jphein/ember.realm.watch/site/README.md

# Ember — GitHub Pages site

Mirrors the repo layout morpheus confirmed: **`docs/` is the Pages root.**

```
index.src.html           ← EDIT THIS
build.py                 ← then run this (it also runs build_print_sheet.py)
build_print_sheet.py     enclosure/PRINT-SHEET.md → docs/print-sheet.html
check_generated_current.py   pre-commit: source staged without its rebuilt page
check_served_current.py      after a push: what a VISITOR downloads vs origin/main
renders/                 enclosure figures — GENERATED, not hand-drawn:
                           case-*    enclosure/tools/make_renders.py        (desk)
                           mobile-*  enclosure/tools/make_mobile_renders.py (battery)
ember-art-web/og_card.py ← regenerates the social preview card
docs/                    ← the deliverable; stage this whole directory
  index.html          HTML + inline <style> + the inlined hero SVG
  print-sheet.html    generated; .nojekyll would otherwise serve the .md as text
  assets/*.wav        the six chimes, fetched on click
  assets/og-card.png  1200x630 social preview (PLACEHOLDER — see below)
  .nojekyll           serve the tree untouched by Jekyll
```

**The figures under `renders/` carry no hand-drawn geometry, and that is load-bearing.** The
button outline was once typed twice — once as a solid in `ember_case.py`, once as a polygon in
`make_renders.py` — and the two copies were free to disagree forever with nothing to notice.
They did: both were rectangles, the part was asked to become hexagons, and only the figure is
ever looked at. Every figure now reads the case module. *A second hand-drawn copy of geometry
is not documentation of it, it is a rumour about it.*

**No byte counts here on purpose.** They used to be quoted and they went stale every
build — this file claimed 138 KB for a page that had grown past 250. `build.py` prints
the real sizes, the inline/copied split and every outbound link on each run, so that
output is authoritative and this list is only a map.

## Editing a source is not publishing it, and publishing is not serving

Three separate gaps, and each one has produced a wrong **published** page while the repo looked
correct. The two checks above exist because notes about this did not work:

| gap | symptom seen | caught by |
|---|---|---|
| source edited, page not rebuilt | `docs/print-sheet.html` said **"⛔ DO NOT PRINT"** for hours after the source was cleared | `check_generated_current.py`, pre-commit |
| committed, not pushed | the retraction sat locally while the page still warned | `git status` / the sweep's ahead-behind line |
| pushed, not yet served | the fixed STL download served the **blocked** part for ~1 min | `check_served_current.py`, after a push |

⚠️ **`enclosure/PRINT-SHEET.md` does not look like a build input.** It is a markdown file in the
enclosure directory, and nothing at the point of editing says a page depends on it — which is
why the guard is mechanical rather than a request to remember. If you add another
source → page pair, add it to `PAIRS` in `check_generated_current.py` in the same change, and
run `--self-test`.

**`renders/` is now in `PAIRS` too, and it should have been from the start.** The guard's own
list of what it exists to prevent opens with *"`docs/assets/case-hero.png` was one render behind
after the case geometry changed"* — and the figures were never actually added, so that first
entry was the one case still uncovered. It matters more than "cosmetic" suggests: `build.py`
**inlines** the SVGs into `docs/index.html`, so regenerating a section drawing and staging it
without rebuilding publishes the previous geometry while the repo looks correct. All 13 figures
are listed, and `_compare` runs each builder once regardless of how many are staged, so the
guard did not get 13× slower. `--self-test` reports **15 pairs**.

The hook is not tracked by git (`.git/hooks` never is), so **a fresh clone starts unprotected**.
The install line is in [`docs/verification.md`](../docs/verification.md).

## ⚠️ One thing still outstanding

**`assets/og-card.png` is still the placeholder.** The card the site *should* ship —
lyra's, with the web-scale wyrm — is generated by `ember-art-web/og_card.py`, which is
in this repo and verified reproducible. What has not happened is the swap itself:
dropping its `og-card.png` into `docs/assets/` **and** updating `og:image:alt` in
`index.src.html` in the same change, because the alt currently describes the
placeholder. That pairing is the whole point — the page renders perfectly with a stale
alt, so nothing local will flag it. It surfaces only in a screen reader or a social
preview.

`og_card.py` will not let a wrong *engine name* through: it carries a `CLAIMS`
provenance table and a `BLOCKED` list (`whisper`, `openai`, `cloud api`, …) checked
against the artwork text and the alt text, and it exits non-zero on a hit. It cannot
check whether the alt still describes the right *picture*. That part is the human's.

*(Resolved: the canonical URL used to be flagged here as assumed. It is confirmed —
`https://jphein.github.io/ember.realm.watch/` serves 200.)*

**Never edit `docs/index.html`** — it is generated and will be overwritten.

```bash
$EDITOR index.src.html
python3 build.py
```

`build.py` replaces `{{ASSET:name}}` placeholders and refuses to write a file with any
placeholder left unresolved. It also warns if an off-box URL appears.

## Why one page

The story is one arc — what Ember is, what it looks like, what it sounds like, what went
wrong building it. The engineering half is the most interesting part, and splitting it across
routes would break the narrative exactly where a reader decides whether the project is
serious. One page is also one artifact to review and nothing to keep in sync.

If it grows past ~2× this length the natural seam is lifting "Engineering" out. Not before.

**The engineering notes deliberately do not duplicate `docs/hardware.md`** (nebula-docs owns
that). The split is by *job*: the site's job is to make you care, the reference doc's job is to
help you build. So the site carries a curated six-row table with narrative framing and links
out for the exhaustive version. If you find yourself copying a table between the two, one of
them is in the wrong place.

## Why art is inline and audio is not

The first version base64'd everything into one 345 KB file. The measurement said that was
wrong:

```
audio data URIs : 255 KB  (74% of the page)
image data URIs :  59 KB
everything else :  31 KB
```

A `data:` URI is **part of the document**, so `<audio preload="none">` over one is a lie — the
bytes are downloaded before the tag is parsed. Every visitor paid 255 KB for six chimes whether
or not they clicked one. As real files under `assets/`, `preload="none"` becomes true and each
chime is fetched on click. **345 KB → 95 KB initial page.**

Art stays inline: it is small, it is needed for first paint, and an extra round trip would cost
more than base64's ~33% overhead. It shrinks again when lyra's SVG lands — and SVG must be
inline regardless, because CSS cannot reach inside an `<img>` to animate it.

Still nothing off-box: no CDN, no external fonts, no remote images. Verify after any edit:

```bash
grep -o 'https\?://[^"'"'"')]*' docs/index.html | grep -v w3.org    # must print nothing
```

## Assets

`build.py` **discovers** `art/` and `sounds/` rather than hardcoding a path, because this page
was written before its repo existed. `_CANDIDATE_ROOTS`, in the order the code actually uses:

1. `REPO/esphome` — where the extraction put `art/` and `sounds/`. **This must stay first.**
2. `site/ember-art-web/` — lyra's web art.
3. `REPO` — assets at the repo root.
4. `~/Projects/ha/esphome` — pre-extraction, and **behind a hard stop**; see below.

⚠️ **Do not reorder this list from memory, and do not "tidy" entry 4 away.** This README
previously described a different order, with `ember-art-web` first and the old repo as a
plain fallback. Restoring that order is the bug: every candidate misses, discovery falls
through to `~/Projects/ha/esphome`, and the site rebuilds **from the old repo —
correctly, indefinitely, with nothing in the output to show it.** That is the exact
failure the extraction existed to end, and it has already been reintroduced once by a
drop that overwrote `build.py`.

Entry 4 is not a fallback. `_find()` **refuses to build** if discovery reaches it, with
an explicit message, unless `EMBER_ALLOW_STALE_ASSETS=1` is set by someone who means it.
A build that succeeds wrongly is worse than one that stops. `build.py` also prints which
roots it used on every run — that output, not this list, is the authority.

Curation is deliberate; every byte ships to every visitor.

- `chime_timer` is **omitted** — largest file, musically the least distinct (a longer
  `announce`), so it costs the most weight for the least added information.
- `chime_listening` is **included** even though the device never plays it. Hearing the tone
  that was deliberately silenced is the point of that section.
- The hero and the five state cards are **one** sprite (`wyrm_states_shipped.png`) sliced with
  CSS `background-position`, so the largest image is inlined once and used six times.

## Themes

Dark and light, both via `prefers-color-scheme` and CSS custom properties, plus
`:root[data-theme="dark"|"light"]` overrides so a host page or a future toggle can force
either. **Dark is the default** — it is the base `:root`, and the device itself is a dark
screen. The palette is the firmware's own fire ramp (ember → amber → gold → white-hot, ash
off-ramp) so the site and the hardware are the same object.

Embedded device art keeps its dark background in both themes on purpose: it is a screenshot of
a screen, and recolouring it would misrepresent the hardware.

Check light without changing your OS:

```bash
sed 's|<html lang="en-GB">|<html lang="en-GB" data-theme="light">|' docs/index.html > /tmp/l.html
xdg-open /tmp/l.html
```

## Accessibility

- Sprite-backed panels are `role="img"` with descriptive `aria-label`s, because a CSS
  background is invisible to a screen reader.
- Chimes are real `<button>`s with `aria-label` and `aria-pressed`.
- `prefers-reduced-motion` disables the hero glow and all transitions. **Note for lyra:** the
  global rule is `*{animation-duration:.001ms !important}`, which will neutralise your
  keyframes — that is intended, but it means you don't need your own media query.
- `:focus-visible` styled; mono type ≥ .68rem; contrast holds in both themes.

## Lyra's art — integrated

From `../ember-art-web/`, located by `_WEBART` in `build.py` (it is a *flat* directory, not an
`art/` subdir, so it is discovered separately from the device art).

| asset | how it is used | why |
|---|---|---|
| `wyrm-startle.svg` | **inlined** as markup | Its keyframes live inside it and CSS cannot cross an `<img>` boundary. This is the only asset that earns inlining. |
| `wyrm-states.svg` | file, CSS `background` | CSS never reaches *inside* a background image, so inlining would buy nothing and cost 33% base64 plus a worse gzip ratio. |
| `favicon.svg` | file, `<link rel="icon">` | 2.8 KB inline in every page load is worse than one cached fetch, and a favicon is a separate request regardless. |

**The inlining rule, stated once:** inline only what CSS must reach inside. That rule took the
page from 345 KB to 138 KB (31 KB gzipped) and it applies to art exactly as it applied to audio.

### Geometry that the CSS depends on

- Hero viewBox is **1136×528** (2.15:1). It fills the content column; nothing depends on the
  exact ratio, so a re-pose is safe.
- States viewBox is **1136×3020 — five exact panels of 1136×604.** The card CSS slices it with
  `background-size:100% 500%` at positions 0/25/50/75/100%. **If the panel count or the equal
  spacing changes, those stops need recomputing.** Card `aspect-ratio` is `1136/604`.

### Two things worth knowing before editing the hero

- **Do not add an overlay on top of the inline SVG.** It carries its own idle breath, so a second
  animation fights it — and an overlay sits between the pointer and the thing it is meant to wake.
  An earlier version of this page had exactly that and it was removed.
- **Her `<style>` block leaks to the whole document**, as every inline SVG's does. Its selectors
  are `.wyrm`, `.hearth`, `.is-awake` — verified against every class token on this page, no
  collisions. Her IDs (`belly`, `eyeglow`, `hearthglow`, `rim`, `skull`, `tongue`) are unprefixed
  but do not overlap `wyrm-states.svg`, so nothing cross-wires *while only the hero is inlined*.
  **If anyone ever inlines the states sheet as well, prefix both first.**

### Labels

Her art carries the state *name* ("1 · listening"); the HTML `.rung` line carries its position
on the fire *ramp*. Different information on purpose — and the HTML one matters because her
label is set in the artwork, so it shrinks with the two-column cards while the HTML does not.

## The share kit

Lifted from `~/Projects/moyoung-watch/docs/index.html` — JP's established pattern for a project
page — so the two sites behave the same way. Full Open Graph + Twitter card set, then six
buttons: Facebook, Hacker News and Reddit as real submit intents with pre-written titles;
Hackaday as copy-then-open (they take tips by paste, not by intent); Instagram as copy-only
(no web share exists); and `Share…`, hidden by CSS and revealed by JS only where
`navigator.share` actually exists.

Pre-written titles are in `index.src.html`. The hook is deliberately *no cloud at all* rather
than *dragon*, because the dragon is the reason people stay and the privacy claim is the reason
they click:

- **HN**: `Show HN: A $20 voice assistant with no cloud — local STT, a 35B LLM, and a dragon`
- **Reddit**: the same claim, spelled out, since Reddit tolerates length

`build.py` distinguishes **fetched resources** from **outbound links**. Self-containment means
nothing is *fetched* off-box; an `<a href>` to Amazon or Hacker News is a navigation and is the
whole point of those sections. The old check flagged both and would have cried wolf on every
build.

## Notes for whoever edits next

- Nothing here reads or writes `~/Projects/ha/scratch/ember-satellite.yaml`.
- **Hedge where the engineering is open — and tighten when it closes.** This note used to say
  the pop section's two candidate mechanisms "have not been distinguished, because they
  haven't," and asked the next editor not to tighten it into a victory claim. **That is no
  longer true and the instruction is now backwards.** The pop was resolved the same evening:
  the amp is the mechanism, and the codec mute is *positively excluded* rather than merely
  doubted. The page was correctly rewritten to match, and anyone obeying the old note would
  revert a good change.

  The principle it was protecting is still right, so keep it and drop the stale example:
  being accurate about what is open is part of why the page is worth reading — which cuts
  both ways. A hedge left standing after the question is answered is as wrong as a victory
  claim made before it. When a section's engineering settles, the section moves with it.
- Corollary, and it is cheap: **check a claim against the rendered page, not the source.**
  Flatten whitespace first — `re.sub(r'\s+', ' ', ...)` — because a per-line `grep` for a
  phrase that wraps across two lines returns nothing and reads as "absent". That false
  negative has bitten this project more than once.
