jphein/ember.realm.watch/docs/assets/dragon_sheet.png

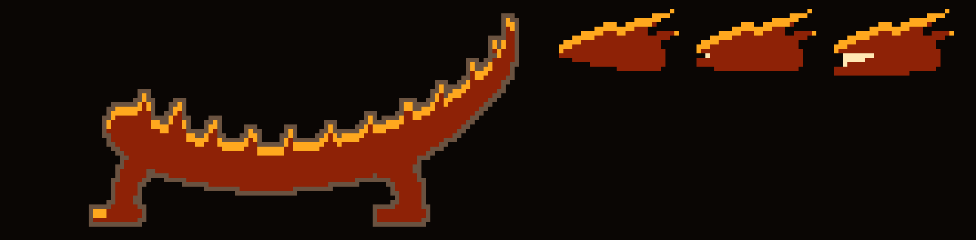
docs/assets/dragon_sheet.png
