jphein/ember.realm.watch/docs/assets/og-card.png

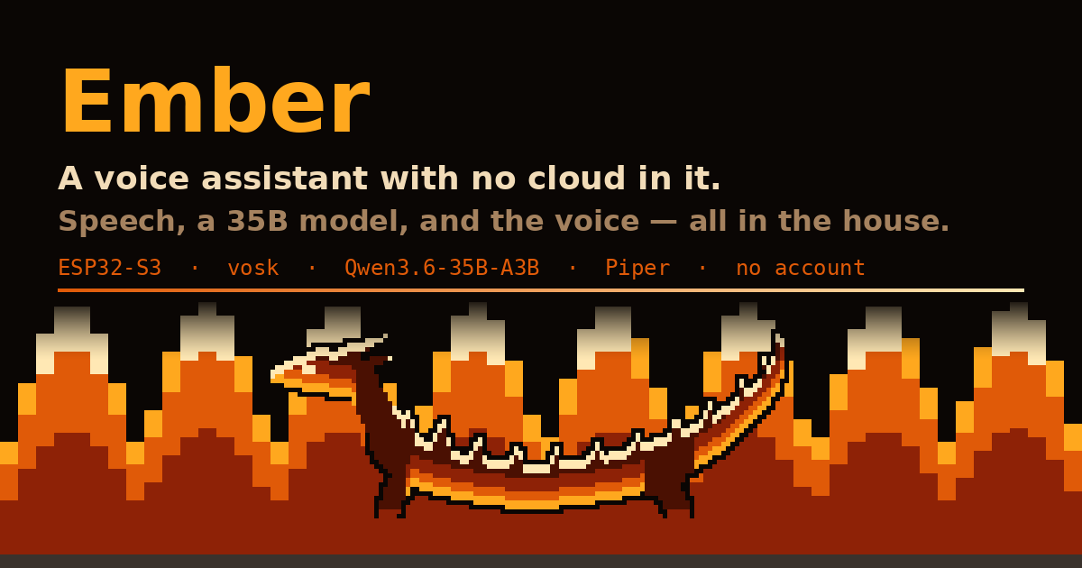
docs/assets/og-card.png
