jphein/ember.realm.watch/esphome/art/dragon_2x.png

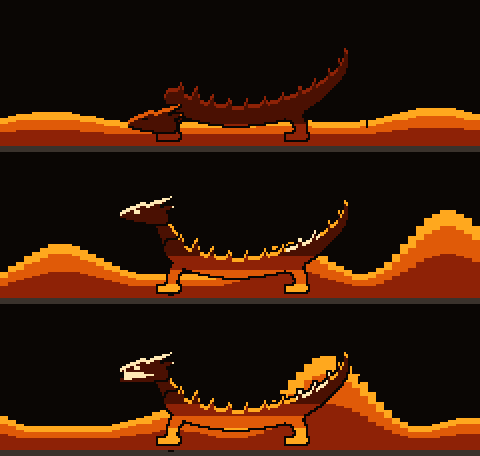
esphome/art/dragon_2x.png
