jphein/ember.realm.watch/esphome/art/dragon_in_fire.png

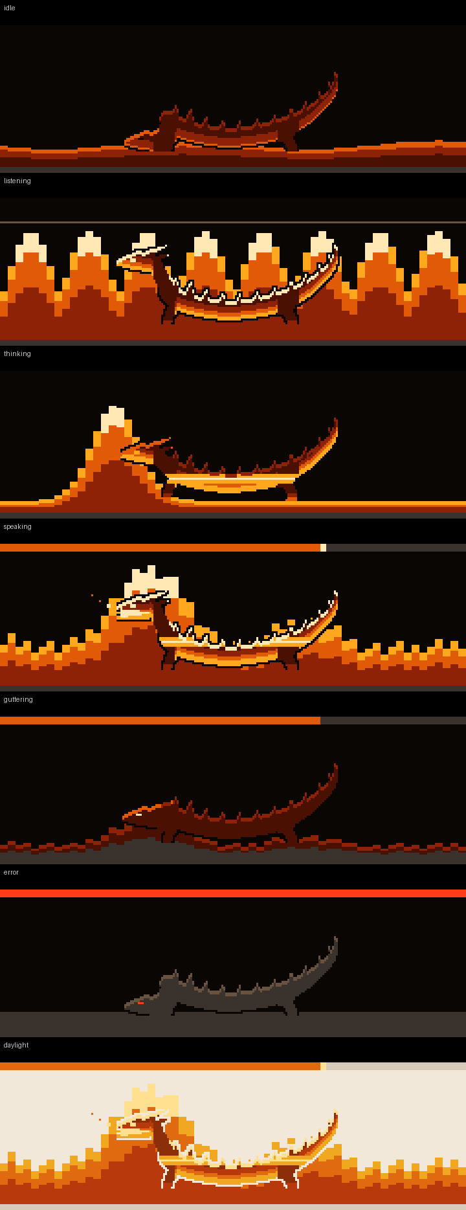
esphome/art/dragon_in_fire.png
