jphein/ember.realm.watch/esphome/art/dragon_speaking.png

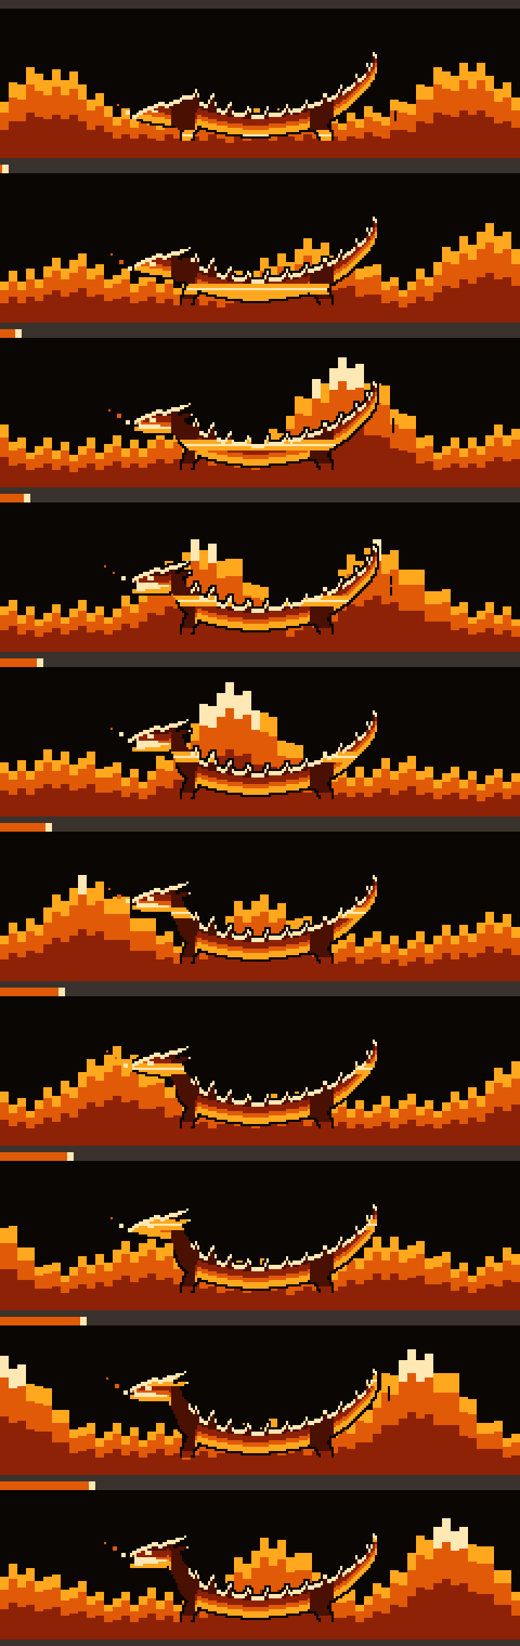
esphome/art/dragon_speaking.png
