jphein/ember.realm.watch/esphome/art/dragon_states.png

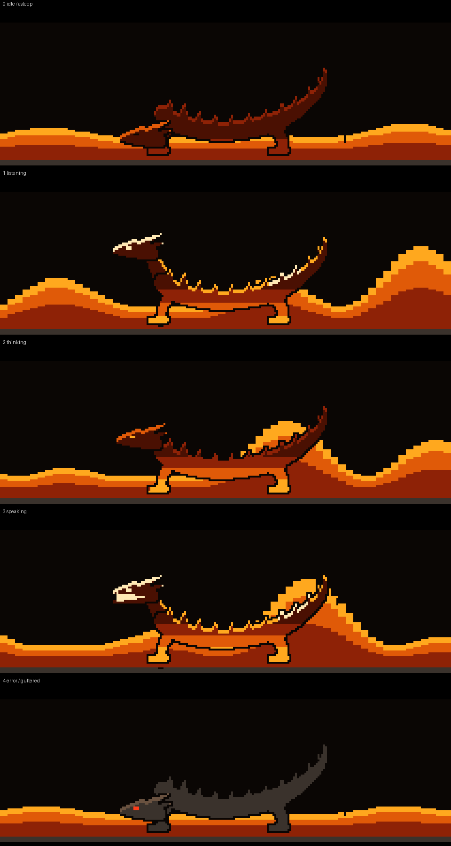
esphome/art/dragon_states.png
