jphein/ember.realm.watch/esphome/art/dragon_wing.png

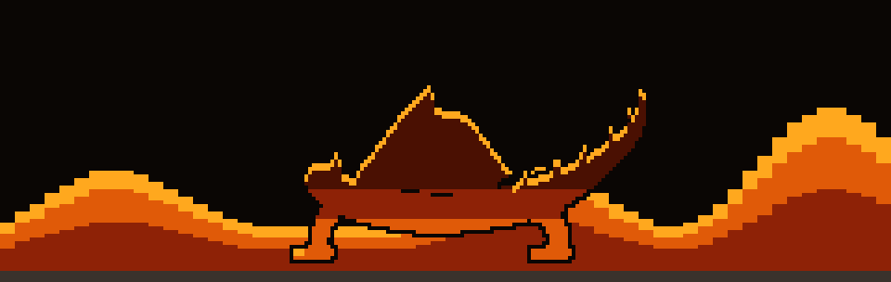
esphome/art/dragon_wing.png
