jphein/ember.realm.watch/enclosure/ember_mobile_case.py

"""
Ember MOBILE enclosure  --  ES3C28P + 18650 + integrated speaker, one handheld case
====================================================================================
Parametric source.  Run:  ../cadenv/bin/python ember_mobile_case.py
Outputs 2 new STLs and re-runs the vendor-STEP clearance boolean against both.

>>> THE BEZEL AND THE BOARD-CLAMPING STACK ARE NOT TOUCHED. <<<

`ember-front-bezel` is reused BIT-IDENTICAL from ember_case.py -- same STL, same four
M3x12 ISO 4762, same HOLES, same CBORE_DEPTH, same 5.34mm engagement. This file adds:

    ember-mobile-midframe   back_shell() + brow + bond plateau + pockets   (0.20 layers)
    ember-mobile-back       the cell/speaker cover                          (0.20 layers)

Why a backpack and not a deeper back shell: SCREW_LEN is an UNDER-HEAD length and
ember_case.py records that M3x14 bottoms out at the pilot's 6.20 end while "the failure
still looks like success". Deepening the shell moves the counterbore 21.80mm further from
the pilot and invalidates that entire derivation. Holding the midframe's back face at
BACK_Z = -9.70 means the bezel-board-midframe clamp is the SAME assembly as the desk case
and none of that analysis has to be redone.

The second consequence is the one that makes the product work: the cell sits behind a part
that carries no board load, so REMOVING THE COVER DOES NOT DISTURB THE BOARD.

COORDINATE SYSTEM: the board's own frame, identical to ember_case.py.
    X  0 .. 50    Y  0 .. 86    Z  glass +4.30 | PCB top 0 | deepest back component -6.30

⚠️ EVERY BOARD NUMBER AND EVERY SHELL NUMBER IS IMPORTED, NEVER RE-TYPED. If a constant
appears as a literal below it is because this file is the first place it exists; anything
ember_case.py already owns is read from `E`. That rule is the whole reason this file can be
trusted to stay in step with a part that is actively being printed from.
"""
from build123d import *
import os, sys, math

_HERE = os.path.dirname(os.path.abspath(__file__))
if _HERE not in sys.path:
    sys.path.insert(0, _HERE)
import ember_case as E

# ============================================================================
# 1. WHAT IS IMPORTED.  Named here so the dependency is a list, not a grep.
# ============================================================================
OX0, OX1, OY0, OY1 = E.OX0, E.OX1, E.OY0, E.OY1        # -2.95..52.95, -2.95..88.95
BACK_Z, CAV_FLOOR, SEAM_Z, FRONT_Z = E.BACK_Z, E.CAV_FLOOR, E.SEAM_Z, E.FRONT_Z
OUT_R, WALL, CHAMFER = E.OUT_R, E.WALL, E.CHAMFER
LH = E.LAYER_H_SHELL                                    # 0.20 -- this file's ONLY layer height
BAFFLE_T = E.BAFFLE_T                                   # 2.20
HEX_R, HEX_WEB, GRILLE_INSET = E.HEX_R, E.HEX_WEB, E.GRILLE_INSET
HEX_FIELD_X0 = E.HEX_FIELD_X0                           # 9.00, the back field's -X edge
DRIVER_W, DRIVER_H, DRIVER_T = E.DRIVER_W, E.DRIVER_H, E.DRIVER_T
DRIVER_R, DRIVER_CLR = E.DRIVER_R, E.DRIVER_CLR
CBORE_D, CBORE_DEPTH, SCREW_D, PILOT_D = E.CBORE_D, E.CBORE_DEPTH, E.SCREW_D, E.PILOT_D
SCREW_HEAD_D, SCREW_HEAD_H = E.SCREW_HEAD_D, E.SCREW_HEAD_H
bx, rbox, cyl, hexp = E.bx, E.rbox, E.cyl, E.hexp

# ⚠️ THE MOBILE'S OWN FLANK OPENINGS, NOT THE NOMINAL SET. JP suppressed SPK and BAT on this
# variant (SIDE_BLOCK in ember_case) — SPK because the driver lives in the cover's sealed cavity
# and its pigtail leaves through the SPK relief, BAT because the pigtail runs internally through
# the midframe's floor pass. Everything here that reasons about "where is the wall solid" must
# read THIS, not E._CH_*: the glow window's site is SOLVED at runtime from the solid spans
# between openings, so closing one silently moves a published feature. It did — see the [glow]
# line in the build log.
MOB_CH_HI, MOB_CH_LO = E.side_channels("mobile")


def cyl_y(cx, cz, d, y0, y1):
    """Cylinder with its axis along +Y. Same construction trick as E.rrect_y()."""
    return Pos(cx, y0, cz) * (Rot(-90, 0, 0) * extrude(Circle(d/2), y1 - y0))

# ============================================================================
# 2. THE COVER'S WALL, AND WHY IT IS 2.20 AND NOT THE FAMILY'S 2.60
# ============================================================================
#
# Two independent reasons converge on the same number, which is the only reason it is
# allowed to differ from WALL:
#
#   1. IT IS THE BAFFLE. The cover's outer wall over the driver IS the grille's baffle, so
#      its thickness IS the acoustic port length. The desk stand gets 2.20 by cutting
#      GRILLE_RECESS into a 4.0 wall; here the wall already is the baffle and the recess
#      disappears entirely. Setting COV_WALL = BAFFLE_T makes the port length identical to
#      the stand's BY CONSTRUCTION rather than by coincidence -- asserted at check 2.
#   2. THE X BUDGET DOES NOT CLOSE AT 2.60. Interior width must hold the cell bore (19.40)
#      plus a shared divider (2.00) plus the driver's tape footprint (28.20) = 49.60.
#      At WALL=2.60 the interior is 50.70, leaving 1.10 total; at 2.20 it is 51.50, leaving
#      1.90. The rim needs that. Asserted at check 3 so it cannot silently go negative.
#      (The bore figure was 19.60 here until 2026-08-01 -- stale since the bare-cell
#      re-primary. Check 3 measures the live constants, so only the prose had drifted.)
#
# 11 * 0.20 exactly, so the wall is a whole number of layers like everything else here.
COV_WALL = 11 * LH                                      # 2.20

# ============================================================================
# 3. THE CELL.  Designed to the LONGEST cell, not the nominal one.
# ============================================================================
#
# >>> THIS IS THE ANSWER TO "DOES A PROTECTED CELL FIT". IT IS A DIMENSION, NOT A HOPE. <<<
#
# An unprotected 18650 is 65.20 long; a protected one carries a PCB and a re-wrap and runs
# to ~71. Sizing the bay to the SHORT cell and hoping is the obvious mistake. Sizing it to
# the LONG cell and letting a spring take up the 5.80mm difference makes both fit, and turns
# the question into an arithmetic one that check 5 can actually test.
#
# ⚠️ AND IT IS NOT A FREE CHOICE. Open electrical question 3 (see the design note) is whether
# the board provides ANY over-discharge / over-charge protection. If it does not, a protected
# cell is MANDATORY -- which is exactly why this bay costs 9.55mm of case length rather than
# being sized to 65.20 and saving it.
#
# >>> 2026-08-01 REVERSAL (JP): "no, I only use bare cells, no protected tops." <<<
#
# BARE FLAT-TOP 18650 IS NOW THE ONLY CELL CLASS. Everything below is re-primaried to it, and
# two things that were true yesterday are now false:
#
#   * the 71.00 allowance existed solely for a protection PCB and its re-wrap. Gone -> the bay
#     drops 6.50 and the case drops 5.90.
#   * THE BUTTON KEYING IS VOID AND HAS BEEN REMOVED. A flat-top positive is the plain can face;
#     it cannot reach a contact recessed behind an aperture, so the keyed cover would have
#     rejected the only cells JP owns. There is NO mechanical keying available for flat-tops --
#     both ends are geometrically identical. Reverse protection is now MARKINGS ONLY. See §"MARK".
CELL_D_MAX      = 18.80     # bare flat-top can incl. wrap; bare stock is 18.4-18.6
CELL_BORE_CLR   = 0.30      # per side, hand-drop fit for a cylinder
CELL_BORE_D     = CELL_D_MAX + 2*CELL_BORE_CLR          # 19.40 = 97 layers, and the cover
                                                        # depth below must stay layer-whole
# >>> D3 SETTLED (JP, 2026-08-25, issue #44): the cell IS the mobile hearth's cell — the
# same bare flat-top 18650 stock, one household population. These four constants are the
# draft's TOLERANCE BANDS, not measurements — and that turned out to be GOOD ENOUGH,
# verified in the flesh rather than by calipers: JP, 2026-08-26, on the printed
# backpacks (midframe r12 + cover r15, in service since 08-09): "the 18650 cell works
# perfectly, size and temp." That closed #44's last gate (D1, the bench-supervised
# charge + temperature check). The caliper re-derivation this comment used to demand is
# therefore MOOT WHILE THE CELL POPULATION IS THIS ONE — the condition written next to
# the decision, per the house rule: if a future cell binds or rattles in the bore,
# measured values replace NOM/TOL here (every consumer — 5g preload assert, BAY_L,
# CELL_BORE_D layer count — flows from these four names) and nowhere else.
CELL_L_NOM      = 65.20     # bare 18650
CELL_L_TOL      = 0.30      # manufacturing spread, bare stock
CELL_L_MIN      = CELL_L_NOM - CELL_L_TOL               # 64.90
CELL_L_MAX      = CELL_L_NOM + CELL_L_TOL               # 65.50
# ============================================================================
# 3b. NO COIL SPRING.  A FOLDED NICKEL LEAF, AND THE CASE GETS SHORTER FOR IT.
# ============================================================================
#
# >>> JP: "design the mechanism to be just PLA printed and the nickel strips."  <<<
#
# The coil is gone. What takes up the cell's length tolerance is now a FOLD in nickel strip --
# the same 0.25 stock the contacts and the protection strip's tabs are already made of -- seated
# in a printed pocket at the bay's -Y end. Best case it is not even a separate part: the
# protection strip now lies in the lower band a few millimetres away (§5f), so its pre-welded
# B- tab can be folded up into the pocket and BE the spring and the contact in one, with zero
# extra hardware. If a tab turns out too short or too narrow to fold well, a separate folded
# nickel piece drops into the same pocket and the tab laps onto it -- the pocket does not care
# which, and check 5 measures the pocket rather than the metal.
#
# ⚠️ AND THE ALTERNATIVE -- A PRINTED PLA FLEXURE -- IS REJECTED ON CREEP, NOT ON PRINTABILITY.
# A cantilever in PLA holding a cell against a contact is under CONSTANT load for the life of
# the device, and PLA stress-relaxes: the deflection stays and the force does not. The printed-
# in-place button hinges in this family survive because they flex for a fraction of a second and
# spend their lives unloaded. A battery contact is the opposite duty cycle. So PLA does GEOMETRY
# here -- the datum, the travel stop and the retention -- and the metal does the force.
#
# ⚠️ THE FORCE IS JP-TUNABLE AND THAT IS DELIBERATE. A hand-formed fold's rate is whatever his
# fingers and pliers produce; nothing in this file can predict it. So the pocket is sized to
# accept a RANGE of fold depths and the numbers below bound the geometry, not the newtons.
LEAF_T          = 0.25      # nickel strip stock -- the same CONTACT_T the plate is
LEAF_FOLDS      = 3         # a Z-fold: three thicknesses plus bend radii when fully closed
LEAF_SOLID      = LEAF_FOLDS * LEAF_T                   # 0.75, the fold closed up
LEAF_FREE       = 3.60      # ⚠️ JP-TUNABLE: the fold's height at rest, formed by hand
# >>> AND THE MARGIN CAN BE SMALL HERE IN A WAY IT COULD NOT BE FOR THE COIL. <<<
# SPRING_MARGIN was 1.00 because a coil at its solid height is a SOLID CYLINDER: reach it and
# the cell physically will not go in, so the bay had to guarantee never reaching it. A fold has
# no such stop -- it just gets stiffer as it closes, and it can always take another tenth. So
# the margin is what the case length leaves over rather than a floor the case must respect,
# and it is DERIVED below and PRINTED, not chosen.
BAY_L           = None      # solved in section 4, against the desk profile. See MOB_OY1.

# ============================================================================
# 4. WHERE THE COVER STOPS, AND WHY THAT IS A REACHABILITY DECISION
# ============================================================================
#
# >>> THE CHIN IS BARE ON PURPOSE. <<<
#
# docs/verification.md lists REACHABILITY as the lens none of the geometric checks have, and
# names this exact failure: "the stand in front of the screen; THE BUTTONS SEALED INSIDE IT."
# BOOT carries DEBOSS_BIG and ember_case.py calls it "BOOT/volume, the one you reach for" --
# it is a volume key. Burying it under a battery door repeats a fault already paid for once,
# and no clearance boolean in this file would say a word about it.
#
# So the cover stops short of both caps and the midframe's back face stays exposed below it,
# exactly as in the desk case. DERIVED from cap_geometry(), never typed: a cap whose R or
# PAD_Y0 moved would drag this with it.
_BOOT_TOP  = E.cap_hex_top_y(*E.cap_geometry(E.BTN_BOOT_X)[:2])     # 15.80
_RESET_TOP = E.cap_hex_top_y(*E.cap_geometry(E.BTN_RESET_X)[:2])    # 10.80
CAP_KEEPOUT = max(_BOOT_TOP, _RESET_TOP) + E.SLOT_W                 # 16.40, moat included
COVER_CLR   = 1.60          # finger room past the moat before the step starts
COVER_Y0    = CAP_KEEPOUT + COVER_CLR                               # 18.00

# ---- and everything downstream of it, in one chain so nothing can drift ----
# ⚠️ THE LEAF'S SEAT IS RECESSED INTO THE -Y END WALL, and the amount is what the wall can
# actually spare -- MEASURED, not assumed. The commission for the no-lip round said the space
# below BAY_Y0 was owned by the chin screw's boss and the "-" mark, both movable. The solid says
# otherwise: a raster of the built cover across the cell lane reads 100% SOLID for eighteen
# consecutive 0.10 bands from y 18.00 to 19.80. It is this wall. The chin screw's cover pad is
# x 19.05..28.05 against a lane ending at CELL_X1 -- CLEAR OF THE LANE BY 0.40, so moving it
# frees nothing; and the "-" mark went to the mating face rounds ago (see the note in
# back_cover() where it used to be cut).
#
# What the wall can spare is bounded by the LEAF KERF, which has already eaten 0.35 of it: the
# void starts at 19.85 over the kerf's x span (wall 1.85), 20.20 outside it (wall 2.20). So the
# recess is (COV_WALL - kerf) - MIN_SOLID and no more, or the DOCKING FACE goes under the floor.
LEAF_KERF_ASSUMED = 0.35                  # == CONTACT_KERF; asserted against it in 5g
LEAF_SEAT_RECESS  = (COV_WALL - LEAF_KERF_ASSUMED) - 4 * 0.40           # 0.250. MIN_SOLID is
                                                                        # named in 5g, below.
BAY_Y0   = COVER_Y0 + COV_WALL - LEAF_SEAT_RECESS       # 19.95 — the leaf's seat (see 3b)
# ---- KEYING REMOVED.  There is none available, and saying so is the deliverable. ----
#
# The previous revision recessed the +ve contact behind a d7.00 aperture so a reversed cell's
# flat end could not reach it. That worked ONLY because a protected cell's positive is a raised
# button. On a bare flat-top BOTH ENDS ARE GEOMETRICALLY IDENTICAL: any aperture that stops a
# reversed cell stops a correct one too, and any opening that admits a correct one admits a
# reversed one. It is not a case of finding a cleverer shape -- the information is not present
# in the geometry.
#
# >>> SO REVERSE-INSERTION PROTECTION IS NOW MARKINGS ONLY, AND THAT IS AN ELECTRICAL GAP. <<<
#
# The contact plate therefore sits FLUSH with the bay again and the tip datum is BAY_Y0.
# KEY_PLATE_T lived here -- 0.80, "a 0.30 stamped contact plus room". It was the depth of a
# pocket that located the plate and retained nothing, and section 5g replaced it with a kerf
# whose width is derived from the strip's own thickness. Deleted rather than left to rot.
#
# >>> POLARITY IS THE OTHER WAY ROUND SINCE THE LEAF LANDED, AND IT IS NOT COSMETIC. <<<
#
# The coil used to live at the +Y end and the "+" plate at -Y. Both moved, because the protection
# strip moved: with the strip lying in the LOWER band (§5f) its pre-welded B- tab is inches from
# the -Y end wall, so putting the leaf there makes the tab and the spring the same piece of
# metal. The "+" plate goes to the +Y end and keeps its kerf, its detent and its throat
# unchanged in FORM -- only the wall it is cut into changed. The consequences are tracked:
# both polarity markings swap ends (_mark_face), and the divider's wire groove now carries B+
# the length of the bay instead of B-.
CELL_TIP_Y   = None                                     # -> BAY_Y1, solved below
# ============================================================================
# 4b. THE CASE'S LENGTH, SOLVED AGAINST THE DESK PROFILE.  "WHY DO WE HAVE A BROW?"
# ============================================================================
#
# >>> JP ASKED, AND WITH THE COIL GONE THE ANSWER IS: WE DO NOT. <<<
#
# This chain used to run FORWARD -- BAY_L from the cell and the coil, then BAY_Y1, then
# MOB_OY1 = 92.00 -- and the 3.05mm by which that overshot the desk shell's OY1 = 88.95 was the
# brow. Every version of the brow (a bolted-on block, then a one-profile extension) was a
# consequence of a coil spring's 2.50mm solid height plus the 1.00 of margin a solid height
# forces you to keep away from it.
#
# Take the coil out and the chain runs forward off the CELL instead of off the spring:
LEAF_MARGIN  = 0.30                                     # how far off closed the LONGEST cell
                                                        # ⚠️ WAS 0.50. The other 0.20 went to the
                                                        # no-lip solve (§4b): it is Y at the +Y
                                                        # corner, which is the axis the lip is on.
                                                        # JP-tunable by design -- he forms the
                                                        # fold by hand -- and check [cell] still
                                                        # proves BOTH length extremes fit.
                                                        # must still leave the fold
CELL_TIP_Y   = BAY_Y0 + CELL_L_MAX + LEAF_SOLID + LEAF_MARGIN   # 86.95, the "+" plate's face
# >>> ⚠️ AND THE FIRST ATTEMPT AT THIS SET MOB_OY1 = OY1 AND DECLARED THE BROW DEAD. IT WAS <<<
# >>> WRONG, AND ONLY THE CELL-vs-CRADLE BOOLEAN SAID SO -- 21.218 mm3, at x -0.45..3.50,   <<<
# >>> y 84.07..86.75.  THE COIL WAS NEVER THE ONLY REASON FOR THE BROW.                     <<<
#
# The cell lane runs hard against the -X wall (CELL_X0 = OX0 + COV_WALL, by construction -- the
# X budget has nothing to spare, see check 3). The case's own corner rounds at OUT_R, so over
# the last 6.45mm of the profile the outer skin curves IN toward the bore, which is already
# only 0.10 inside the interior wall on the flat. Where they converge the wall between the
# battery and the outside air runs out, and the interior rbox's own corner fillet -- which is
# just the constant-wall offset of that arc -- eats into the bore before the wall does.
#
# So the bay cannot end where the case does, whatever the spring is. This SETBACK is what the
# coil's 2.50 solid height plus 1.00 of margin had been paying for by accident, which is why
# nobody had ever had to name it: at BAY_Y1 = 89.80 the longest cell stopped at 86.00, 3.80
# short, and 3.80 happens to be more than enough. Delete the coil and the debt comes due.
#
# Derived, not chosen: the distance back from the corner at which the outer arc still leaves
# MIN_SOLID between itself and the bore's -X extreme -- MEASURED IN X.
#
# >>> ⚠️ "MEASURED IN X" IS THE WHOLE CAVEAT, AND IT IS NOT PEDANTRY.  SEE CHECK 7d.        <<<
# The void this defends ends in a CONVEX corner at (CELL_X0, CELL_TIP_Y), and at a convex corner
# the shortest line to the outer arc is the DIAGONAL, not the horizontal. So the expression below
# solves the X clearance and then reports more material than the part has: it delivers 1.41
# radially while naming 1.60. Check 7d measures that on the finished solid, and slice_probe.py
# measured 1.405 on the exported STL independently of any of this arithmetic -- two methods, one
# number. The [exempt] ledger carries the acceptance and the class.
#
# >>> JP, 2026-08-02, told the number and the class: "it's fine as is 1.41mm is pefefctly    <<<
# >>> thick."  ACCEPTED BY THE OWNER.  It is not left as-is because nobody noticed.          <<<
#
# A radially honest MIN_SOLID wants MOB_OY1 >= 91.06 -- the case getting LONGER by 0.38 -- which
# is the decision he declined with the number in front of him. So the expression stays exactly as
# it is; what changed is that it no longer claims to be something it is not.
_BORE_X0     = OX0 + COV_WALL                           # -0.75 -- the bore's -X extreme IS the
                                                        # interior wall; that is the X budget
                                                        # (CELL_X0 below, same expression)
_ARC_CX      = OX0 + OUT_R                              # 3.50, the corner arc's centre
_MIN_SOLID   = 4 * 0.40          # 1.60; MIN_SOLID itself is named in 5g, below
_ARC_DY      = math.sqrt(max(OUT_R**2 - (_MIN_SOLID + _ARC_CX - _BORE_X0)**2, 0.0))
# ⚠️ THE THREE COMMENTS BELOW WERE STALE BY 0.20 AND WERE FIXED 2026-08-02. They read 3.53 /
# 90.48 / 88.28 against live values of 3.733 / 90.683 / 88.483 -- liars with plausible values, the
# fourth instance of the class in this file (dead SD_PLATE, dead GRILLE_SLOT_W, the 5mm ghost).
# A wrong number in a comment is worse than none, because the next reader budgets against it.
CELL_END_SETBACK = OUT_R - _ARC_DY                      # 3.733
# >>> FLUSH.  JP: "no litle lip in backpack figure it out pls."  MOB_OY1 IS OY1 NOW. <<<
# CELL_END_SETBACK is retained above as the RECORD of what used to set this -- it was the case
# buying corner clearance with LENGTH, and the no-lip solve buys it with the -X WALL instead
# (§4b). It is no longer in the expression, and the assert below is what keeps it honest.
MOB_OY1      = OY1                                      # 88.95 -- IDENTICAL to the desk profile
BAY_Y1       = MOB_OY1 - COV_WALL                       # 86.75, the COMPARTMENT's void end
assert MOB_OY1 == OY1, "the mobile is not flush with the bezel and the lip is back"
assert CELL_TIP_Y + COV_WALL <= MOB_OY1 + 1e-9, (
    f"the cell tip at {CELL_TIP_Y:.3f} leaves only {MOB_OY1-CELL_TIP_Y:.3f} of +Y end wall "
    f"against COV_WALL {COV_WALL} -- the -Y end has not given back enough for flush")
BAY_L        = CELL_TIP_Y - BAY_Y0                      # 66.75, the cell's own working length
# ...and the cell lane is SOLID from the plate to BAY_Y1, so the fillet is filled rather than
# dodged: back_cover() adds that bulkhead and cuts the "+" kerf into its -Y face.
assert CELL_END_SETBACK > COV_WALL, (
    f"the corner setback solved to {CELL_END_SETBACK:.2f}, at or under the {COV_WALL} end wall "
    f"-- if so the corner has stopped being the binding constraint and this whole block "
    f"can collapse back to MOB_OY1 = CELL_TIP_Y + COV_WALL")
# CONTROL, and it is the one that would have caught the mistake: a cell reaching all the way to
# BAY_Y1 must still be REJECTED by the same arithmetic, or the setback is not being applied.
assert (OUT_R - (BAY_Y1 - CELL_TIP_Y)) > 0 and \
       (math.sqrt(max(OUT_R**2 - (OUT_R - COV_WALL)**2, 0.0)) - (_ARC_CX - _BORE_X0)) < _MIN_SOLID, (
    "control failed: a bay ending COV_WALL from the case's end reads as leaving MIN_SOLID "
    "between the bore and the corner arc, so the setback above is not defending anything")
assert LEAF_FREE - (BAY_L - CELL_L_MIN) > 0.30, (
    f"the SHORTEST cell ({CELL_L_MIN}) leaves {BAY_L-CELL_L_MIN:.2f}mm against a {LEAF_FREE} "
    f"free fold -- under 0.30mm of preload, so a short cell rattles and the contact is "
    f"intermittent. LEAF_FREE is the knob and JP forms it by hand")
assert (LEAF_FREE - LEAF_SOLID) >= 2 * CELL_L_TOL, (
    f"the fold's travel {LEAF_FREE-LEAF_SOLID:.2f} does not span the cell's "
    f"{2*CELL_L_TOL:.2f}mm length spread -- one end of the tolerance band will not seat")
# CONTROL: the coil this replaced must FAIL the same bay, or the shortening is not evidence.
assert BAY_L - CELL_L_MAX - 2.50 < 1.00, (
    "control failed: the deleted coil's 2.50 solid height plus its 1.00 margin still fits this "
    "bay, so the bay did not actually shrink and the leaf bought nothing")
# ...and the saving, stated as the number it is rather than as the number I wanted it to be.
MOB_OY1_WAS  = 92.00            # the coil-and-tunnel case, for the record
assert MOB_OY1 < MOB_OY1_WAS, (
    f"the case is {MOB_OY1:.2f} long against the coil version's {MOB_OY1_WAS:.2f} -- the leaf "
    f"has not shortened anything and the whole exercise is a wash")

# ---- POLARITY MARKINGS.  The only reverse-insertion measure left. ----
#
# "+" on the low-Y end wall, "-" on the high-Y end wall, both facing INTO the bore so they are
# read at the moment the cell goes in. Groove width is the repo's LABEL_W floor.
#
# ⚠️ min_gap IS VACUOUS ON THESE TWO GLYPHS AND MUST NOT BE USED AS THEIR PROOF. I ran it:
# "+" returns (inf, 0 pairs) because its two strokes CROSS, so _touch() excludes the only pair
# there is; "-" returns (inf, 0 pairs) because one stroke has no pair at all. Asserting
# `min_gap >= LABEL_W` would pass on `inf` for any glyph of this shape, including a broken one.
# That is this repo's own recurring defect -- an invariant insensitive to the failure it names.
# Check 15 measures the DEBOSSED VOLUME on the finished solid instead, which can fail.
MARK_H       = 14 * LH                                  # 2.80 stroke-to-stroke, layer-whole
# ---- DEBOSS DEPTHS: "as deep as we can", DERIVED PER WALL (JP, r11) ----
#
# JP: "all debosses should be even deeper as deep as we can." So no deboss depth in this file is
# a chosen number any more -- each is (local wall - that feature's own floor), and the floors are
# the ones already proven here. What "as deep as we can" MEANS depends on the face's print class,
# and the two classes quantize on DIFFERENT axes:
#
#   BED / CAVITY FACE (horizontal)  depth runs in Z  -> quantize to LAYER_H. Layer boundaries.
#   SIDE WALL        (vertical)     depth runs in X/Y -> layer height does NOT govern it
#                                   (ember_case.py:291 says so for the label grooves already).
#                                   Quantize to EXTRUSION WIDTH instead.
#
# ⚠️ AND A DEPTH THAT LANDS EXACTLY ON ITS FLOOR IS NOT "AS DEEP AS WE CAN", IT IS ON A
# CONSTRAINT BOUNDARY. LABEL_DEBOSS's own block settled this: 3 layers left the cap wall at
# exactly 1.20 against a 1.20 floor, so it took 2 and kept 0.20 of slack. Same rule here --
# every depth below leaves at least one quantum over its floor.
_EXTRUSION = 0.40                       # one bead at the 0.40 nozzle; MIN_SOLID is 4 of these
#
# >>> AND "AS DEEP AS WE CAN" HAS A SECOND BOUND THAT IS NOT THE WALL. <<<
# A groove deeper than it is WIDE stops being a marking: the nozzle cannot reach the bottom
# cleanly, the floor prints ragged, and the slot becomes a dirt trap that fills and reads as a
# solid line. So every glyph-class deboss is capped at its own stroke width -- aspect <= 1:1 --
# and the wall budget only binds when it is the SMALLER of the two. Both bounds are printed in
# the [deboss] table so it is visible which one is doing the work for each feature.
_ASPECT_MAX = 1.0

def _max_deboss(wall, floor=None, quantum=None, on_floor_ok=False):
    """Deepest deboss a `wall` can carry while keeping `floor` of material, quantized DOWN.

    Quantized down and then checked for slack, so the answer is never sitting on the floor it
    was derived from. Returns 0.0 rather than a negative number if the wall cannot carry one.
    """
    # _MIN_SOLID, not MIN_SOLID: this helper is defined ABOVE the public alias (§5g binds it).
    # Same ordering trap that put check 6d before `cov` existed -- a dependency read before it
    # is bound fails only when the line actually runs, which for a default arg is every call.
    floor = _MIN_SOLID if floor is None else floor
    quantum = LH if quantum is None else quantum
    # ⚠️ THE TOLERANCE IS LOAD-BEARING AND ITS ABSENCE WAS ALREADY CHANGING ANSWERS.
    # Two features sit behind a 2.20 wall -- the driver outline and the blind top mesh -- and the
    # bare `>=` sent them different ways purely on float dust (2.20 arrives as 2.2000000000000028
    # from one derivation chain and 2.2 from another, so `3*quantum >= wall-floor` was True for
    # one and False for the other). A print-floor rule decided by the last bit of a mantissa is
    # not a rule. Rounded to a tenth of a quantum, both now answer the same way.
    _n = int((wall - floor) / quantum + 1e-9)
    _lands_on_floor = round(_n * quantum, 6) >= round(wall - floor, 6) - 1e-9
    if _lands_on_floor and _n > 0 and not on_floor_ok:
        _n -= 1                          # never land ON the floor -- LABEL_DEBOSS's precedent
    return max(_n, 0) * quantum


# ---- the two polarity marks, each derived against ITS OWN face ----
# "+" cuts +Y into the bay's +Y end wall: solid behind it runs CELL_TIP_Y -> MOB_OY1.
# "-" cuts -Z into the cover's mating face in the chin band, where the cover is solid for
# tens of millimetres -- so there the ASPECT cap is what binds, not the wall, and that is
# exactly the case the cap was written for.
MARK_DEPTH_WALL = min(_max_deboss(MOB_OY1 - CELL_TIP_Y, quantum=_EXTRUSION),
                      int(_ASPECT_MAX * E.LABEL_W / _EXTRUSION) * _EXTRUSION)
# The "-" mark's face is the cover's MATING FACE, and the cover is solid for tens of millimetres
# under the chin band -- so the ASPECT cap binds and the wall never does. Stated that way rather
# than derived from COVER_Z0 because COVER_Z0 is defined further down this file and a constant
# that reads a not-yet-bound name is the ordering trap this round has now hit twice. The claim
# that the wall does not bind is not left as a comment: check 8a's min-solid sweep covers this
# face, and _deboss_ledger() below re-derives it against the real number every build.
MARK_DEPTH_MATE = int(_ASPECT_MAX * E.LABEL_W / LH) * LH        # 0.80 = 4 layers
MARK_DEPTH   = MARK_DEPTH_MATE      # kept as the shared name every existing caller already reads
                                    # (was a typed 3*LH = 0.60; JP r11: as deep as we can)


MARK_PATHS_P = [[(-MARK_H/2, 0.0), (MARK_H/2, 0.0)], [(0.0, -MARK_H/2), (0.0, MARK_H/2)]]
MARK_PATHS_N = [[(-MARK_H/2, 0.0), (MARK_H/2, 0.0)]]
MARK_INK     = MARK_H + E.LABEL_W                       # 3.70 overall ink extent
# MOB_OY1 and BROW_Y0 used to be defined here. MOB_OY1 moved UP to section 4b, because it is
# now an INPUT to the bay rather than an output of it. BROW_Y0 is deleted outright: there is no
# brow, so there is no y at which one starts.
# ⚠️ THESE TWO COMMENTS SAID -31.50 AND -29.30 UNTIL 2026-08-01, i.e. they were correct for a
# CELL_BORE_D of 19.60 and the bare-cell re-primary took it to 19.40 without them following.
# Harmless here because both are DERIVED and nothing reads the comment -- but it cost real time
# downstream: a slice script written against -31.50 sliced the cover 0.20 too high and read a
# tooth 0.20 up its own skew. §11 defect #8 is this exact class, one file over.
# ============================================================================
# 4c. THE BAY IS DEEPER THAN THE BORE, AND THE EXTRA LANDS AT THE BOTTOM.
# ============================================================================
#
# >>> JP: "the lid is flat teh battery is round isn't there space?"  --  YES, AND HE IS  <<<
# >>> RIGHT.  My tangency finding measured the bore's EXTREMES and called the bay full.   <<<
#
# The bore is tangent to CELL_X0, CELL_X1 and the bay floor -- all three gaps 0.00 -- and I
# read that as "no room". It is not: a ROUND bore in a SQUARE bay leaves four CORNER SOLIDS,
# 4.53mm of diagonal each at the top pair, 4.11 at the bottom (the cell rides CELL_BORE_CLR
# low, which costs the bottom corners 0.42 of diagonal and buys the top ones the same). That
# is where the BMS body goes -- pocketed into a corner, lying against the cell, which is
# exactly what "hugs the battery" means.
#
# ⚠️ AND IT IS STILL 0.33 SHORT, WITH JP'S CALIPERED BODY. A 4.50 x 2.50 body plus 0.40 of
# clearance needs 2.90 of depth at 5.30 of width, and the best corner offers 2.17. So the bay
# grows -- but by BAY_EXTRA, not by the 2.50 I first estimated, because the corner does four
# fifths of the work. +1.20 misses by 0.01, which is a coincidence and not a fit; 8 layers
# lands it with 0.39 of real clearance and keeps every depth layer-whole.
#
# ⚠️ AND THE BORE IS HUNG FROM THE MATING PLANE SO THE EXTRA LANDS AT THE BOTTOM, which is
# JP's own refinement ("or even better at teh bottom") and it is the better call for a reason
# he did not have to state: the strip lays into the bottom channel FIRST and the cell DROPS ON
# TOP OF IT. No threading a part down beside a cylinder that already fills the bore. Note the
# derivation is a NO-OP today -- BACK_Z - CELL_BORE_D/2 and CAV_Z0 + CELL_BORE_D/2 are the same
# number until BAY_EXTRA is non-zero -- which is why it is written this way rather than as a
# constant: it says WHICH END the growth belongs to.
# ⚠️ BACK TO ZERO.  JP: "i want it flush with teh main body. i don't thingk gorwing it is the
# answer."  The corner-solid growth of the previous checkpoint is reverted and the envelope is
# 39.00 again. What houses the body instead is the DIVIDER's own 2.00, deleted across the span
# the strip needs -- his call, made after being told plainly what it costs (§5f-c).
BAY_EXTRA = 0 * LH                                      # flush. See 5f-c for what pays for it.
COVER_Z0 = BACK_Z - COV_WALL - CELL_BORE_D - BAY_EXTRA  # -32.90, the cover's outer face
CAV_Z0   = COVER_Z0 + COV_WALL                          # -29.10, baffle inner AND bore floor
# ⚠️ CAV_Z0 IS ONE PLANE SERVING TWO FEATURES AND THAT IS DELIBERATE. The sealed cavity's
# floor and the cell bore's floor are the same surface at the same Z because both are
# "COV_WALL above the outer face". Writing them as two constants is how the stand's base
# plate went stale against CHAM_Y1 (ember_case.py:1721) -- a copy that was right when it was
# typed and wrong from a distance, with nothing able to notice.

# ============================================================================
# THE NO-LIP SOLVE.  JP: "no litle lip in backpack figure it out pls."
# ============================================================================
#
# The whole problem is ONE CIRCLE. The outer plan corner is an arc of OUT_R centred
# C = (OX0+OUT_R, top_y-OUT_R); the cell void's convex +Y/-X corner is P; the wall between them
# is OUT_R - |P-C|. At flush (top_y = OY1) that wall was 0.296 and it needed 1.60.
#
# Everything that RESHAPES the corner is bounded and measured dead -- the plan-view family by a
# shape-independent 1.299 bound, the Z-banded tail by the cradle fact (an 18650 loads straight
# down, so the void's -X extreme does not retreat above the equator). Check 7e keeps both, with
# the numbers, so nobody re-derives them. What was never tried is MOVING P, and P has two axes:
#
#   +X  thicken the -X wall, walking the bore out from under the arc  -> CELL_WALL_X
#   -Y  recess the leaf seat + spend LEAF_MARGIN                      -> CELL_TIP_Y, -0.450
#
# and one shape term that is free:
#
#   r   round the void's own plan corner to match the cell's rolled edge
#
# ⚠️ r IS BOUNDED BY THE LANE CLEARANCE AND THIS IS THE WHOLE SAFETY ARGUMENT. A square-cornered
# cell has its corner at (CELL_X0 + CELL_BORE_CLR, CELL_TIP_Y). That point is inside the rounded
# void iff (CELL_BORE_CLR - r)^2 + r^2 <= r^2, i.e. iff r <= CELL_BORE_CLR. JP eyeballed his
# cells at "Slightly rounded, ~0.5mm" -- A VISUAL ESTIMATE, NOT A CALIPER READING -- and a round
# built to 0.50 would interfere with a square-cornered cell. So r is taken from the bore
# clearance, a number this file already owns: the geometry is then correct for ANY real cell,
# including one with no roll at all, and cell_phantom() needs no roll modelled to stay honest.
# THE COST OF THAT INDEPENDENCE IS 0.44 OF DRIVER TRAVEL, and it is worth it -- the failure mode
# it buys off is a cell that will not seat, discovered at the bench.
NOLIP_ROLL   = CELL_BORE_CLR                            # 0.30. See the bound above.
NOLIP_TARGET = 4 * 0.40 + 0.10                          # 1.70 -- MIN_SOLID plus the margin this
                                                        # file demands (it rejects features that
                                                        # SIT on a constraint; see LABEL_DEBOSS).
_NL_C   = (OX0 + OUT_R, OY1 - OUT_R)                    # the outer corner arc's centre, at FLUSH
_NL_dy  = (CELL_TIP_Y - NOLIP_ROLL) - _NL_C[1]
_NL_disc = (OUT_R - NOLIP_TARGET - NOLIP_ROLL) ** 2 - _NL_dy ** 2
assert _NL_disc > 0.0, (
    f"no -X wall thickness can carry {NOLIP_TARGET:.2f} at the +Y corner: the Y term alone "
    f"({_NL_dy:.3f}) already exceeds the {OUT_R - NOLIP_TARGET - NOLIP_ROLL:.3f} the arc allows. "
    f"CELL_TIP_Y must come further -Y before X can finish the job")
OX0_WALL_SOLVE = (_NL_C[0] - math.sqrt(_NL_disc) - NOLIP_ROLL) - OX0    # 3.678
# CONTROL: the solve must REJECT the wall it replaced. At the old COV_WALL the corner has to come
# out UNDER the floor, or this derivation is not the thing that fixed the lip and the whole block
# is decoration bolted onto a part that was already fine.
assert OUT_R - math.hypot(_NL_C[0] - (OX0 + COV_WALL + NOLIP_ROLL),
                          _NL_C[1] - (CELL_TIP_Y - NOLIP_ROLL)) - NOLIP_ROLL < 4 * 0.40, (
    "control failed: the -X wall at its ORIGINAL COV_WALL already carries MIN_SOLID at the +Y "
    "corner with the case flush, so the lip was never bought by this wall and the solve above "
    "is not what closed it")

# ---- X LANES.  A SINGLE SHARED DIVIDER, because two walls do not fit. ----
#
# >>> ⚠️ THE -X WALL IS NO LONGER COV_WALL, AND IT HAS A NAME NOW BECAUSE OF WHAT THAT COST. <<<
#
# JP: "no litle lip in backpack figure it out pls."  The mobile ran MOB_OY1 = 90.683 against the
# bezel's 88.95 -- a 1.733 ledge across the whole top edge, and the only place the mobile was
# longer than the case it shares a bezel with. Every way of removing it by RESHAPING the corner
# is bounded and was measured dead (check 7e keeps the ledger). What was never tried is moving
# the thing the corner is short of: the CELL BORE. Thickening this wall walks the bore +X, out
# from under the OUT_R arc, and the lip closes with no shape tricks and no thin walls.
#
# The wall was spelled `OX0 + COV_WALL` in five places and `COV_WALL` was doing double duty as
# "the shell's wall" and "the -X wall specifically". The moment those two diverge the second
# meaning is a liar -- and it nearly took the cell bay's only pressure-relief path with it: the
# vent labyrinth derives its band and skins from the wall it is cut in, and at the old
# expression the two slots would have stopped meeting by 0.20 and become blind pockets. Named,
# so it cannot happen silently again. See §5d's re-derivation.
CELL_WALL_X = OX0_WALL_SOLVE                            # 3.678 -- solved below, not typed
CELL_X0     = OX0 + CELL_WALL_X                         # 0.728
CELL_X1     = CELL_X0 + CELL_BORE_D                     # 20.128
CELL_AXIS_X = (CELL_X0 + CELL_X1) / 2                   # 10.428
CELL_AXIS_Z = BACK_Z - CELL_BORE_D / 2                  # -19.40, HUNG from the
                                                        # mating plane: see 4c
DIVIDER_W   = 4 * 0.40                                  # 1.60 = MIN_SOLID (named in 5g) -- was 2.00, i.e. 0.40 OVER the
                                                        # floor. That 0.40 is the cheapest of the
                                                        # three X payments and the only free one.
RIM_X0      = CELL_X1 + DIVIDER_W                       # 21.728
# ⚠️ THE +X OUTER WALL IS RE-QUANTIZED, and it is the same argument §2 already accepted for the
# +Y end wall: this is a wall printed as PERIMETERS, so its quantum is extrusion width, not layer
# height. COV_WALL 2.20 is 5.5 extrusions -- half a bead that the slicer has to do something with.
# 2.00 is FIVE EXACTLY. It is a better wall and it hands 0.20 to the driver's lane.
WALL_X1     = 5 * 0.40                                  # 2.00, the +X outer wall
RIM_X1      = OX1 - WALL_X1                             # 50.95
RIM_WALL    = 8 * LH                                    # 1.60
# ⚠️ RIM_Y0 WAS BAY_Y0 -- I.E. THE RIM'S LOW-Y SIDE WAS THE COVER'S OWN BOTTOM WALL -- AND THE
# SEAL CHECK REJECTED IT. With the rim starting at the very bottom of the compartment there was
# nowhere along the bottom edge to put a screw pilot or a hook pocket that was not inside the
# seal's footprint, and the first attempt put the screw at (25.00, 19.20): the boolean measured
# the rim landing on 98.36% solid instead of 100%, because the pilot bored straight through the
# ring. 1.6mm3 of hole, and it would have vented the "sealed" cavity into the board cavity
# through the one fastener the user is meant to undo.
#
# So the rim is held off the bottom by RETENTION_STRIP, and every retention feature lives in the
# gap. That is a layout consequence of an acoustic requirement, which is exactly the kind of
# coupling that is invisible at both call sites -- check 6b now asserts it in coordinates as
# well, so the boolean is not the only thing standing between this and a leak.
RETENTION_STRIP = 9.80
RIM_Y0      = BAY_Y0 + RETENTION_STRIP                  # 30.00
RIM_INNER_Y = 44.80
RIM_Y1      = RIM_Y0 + RIM_INNER_Y                      # 74.80

# ============================================================================
# 5. ACOUSTICS.  THE QUESTION IS NOT SEALED-VS-PORTED.
# ============================================================================
#
# ember_case.py:1689 -- "It is a SEALED-BACK MODULE, not a bare driver: a plastic box
# carrying its own rear cavity ... That is why the stand's chamber volume barely matters
# acoustically -- the module brings its own. What matters is the FRONT."
#
# So porting a box behind this driver does nothing; it already has a sealed back. The only
# decision available is the FRONT cavity, and the desk stand is the reference because that
# is the enclosure the driver is KNOWN to sound acceptable in.
#
#   stand chamber  54.00 x 15.30 x 33.00        = 27264.6 mm3
#     - driver     rrect(40,27,r3) x 10.00      = -10722.7
#     - tape pad   rrect(41.2,28.2,r3.6) x 0.80 =   -920.6
#     NET SEALED FRONT AIR                      =  15621.3 mm3
#
# Check 7 recomputes that from E's live constants and measures the mobile cavity by boolean,
# so neither figure is inherited from a comment.
#
# THE DRIVER TAPES DIRECTLY TO THE MIDFRAME'S BACK FACE -- no proud pad. The stand needs
# PAD_PROUD only to stand clear of its chamber's wall/floor junction; the midframe's back
# face is a 3678mm2 printed BED FACE, the flattest plane in the project, and a strictly
# better bond surface. A proud pad here would also be the lowest feature on a bed face,
# which is the defect ember_case.py:2771 records on both shell parts in one session.
# ---- THE BOND LINE, WHICH WAS NEVER A NUMBER UNTIL THE COVER STOPPED SLIDING ----
#
# ⚠️ AN ALLOWANCE, NOT A MEASUREMENT, AND IT IS FLAGGED AS ONE. JP's words are "double-stick
# tape" and nothing more; the class runs from 0.05 (transfer tape) to 1.10 (foam). 1.00 is the
# PESSIMISTIC end, chosen because every question this number is asked is a clearance question
# and the wrong direction to be optimistic in. Check 8d sweeps the driver at this position;
# check 7's acoustics are indifferent to it (they difference volumes, and the module's volume
# does not move). If it ever turns out to matter, it is one constant.
TAPE_T = 1.00                                           # ⚠️ ALLOWANCE, not calipered
FRONT_GAP_MOBILE = (BACK_Z - TAPE_T - DRIVER_T) - CAV_Z0        # 8.60
# ⚠️ NAMED BECAUSE IT IS A DEPARTURE, NOT BECAUSE IT IS DERIVED. The stand holds FRONT_GAP at
# 2.50 on the stated grounds that "extra depth is not extra enclosure, it is extra AIR IN
# FRONT OF THE DIAPHRAGM". That reasoning is about TOTAL front air, and total front air here
# comes out slightly BELOW the stand's -- the same air has moved from lateral to axial. I
# believe that is neutral-to-better (check 7 prints both cavities' first modes and the
# governing one goes UP), but it is an assumption and it is flagged rather than buried.

# ---- GRILLE.  Identical lattice, identical port length, and NO FLARE. ----
#
# GRILLE_FLARE exists in the stand because issue #28's grille DROOPED: there the hexes are
# horizontal bores through a VERTICAL wall, so every cell roof is an unsupported span. Here
# the cover prints outer-face-down and the hexes are VERTICAL PRISMS IN A BED FACE -- zero
# unsupported span, nothing to droop. So the mouth web stays the full HEX_WEB = 0.90 instead
# of the stand's GRILLE_MOUTH_WEB = 0.4670, and the "fin" trap that constant guards against
# cannot arise at all.
#
# ⚠️ THE STAND'S OPEN-AREA FIGURES ARE STALE AND ARE NOT INHERITED. ember_case.py:1948 records
# "THROAT 678.0 ... MOUTH 886.1 ... field itself (37 x 24, r1.5)". rrect(37,24,1.5) = 886.1
# EXACTLY, so that raster was taken with GRILLE_INSET = 1.5. The live constant is 1.0
# (ember_case.py:2015), giving a 38.0 x 25.0 r2.0 field of 946.6mm2. It is a correct
# measurement of an object the file no longer builds -- verification.md section 24. Check 8
# rasters this part's own throat and measures the stand's the same way for comparison.
GRILLE_FW = DRIVER_H - 2*GRILLE_INSET      # 25.00 across X -- driver is rotated 90deg here
GRILLE_FH = DRIVER_W - 2*GRILLE_INSET      # 38.00 along Y
# ============================================================================
# THE FULL SEPARATOR WALL, AND THE DRIVER SHIFT THAT PAYS FOR IT  (JP, r11 final)
# ============================================================================
#
# JP: "Shift it -- build the wall." Authorised with the trade in front of him.
#
# >>> AND THE LANE MATTERS AGAIN: THIS WALL GOES +X OF RIM_X0, NOT IN THE STUB LANE. <<<
# The partial wall this replaces stood in the old divider's lane (x CELL_X1..RIM_X0) and could
# not span the strip's Y range, because the strip loads STRAIGHT DOWN through a PROT_W column
# that the cell pins to exactly that lane. A wall on the DRIVER'S side of RIM_X0 never enters
# that column at all -- the pocket ends AT RIM_X0 -- so it can run the chamber's whole length.
# That is the actual reason the shift works, and it is not the reason I first gave.
# _MIN_SOLID: this block sits ABOVE §5g where the public MIN_SOLID alias is bound. That is the
# THIRD time this round a constant defined up here reached for a name bound further down, so it
# is worth stating as a rule rather than a bug: everything above §5g uses the private names.
SEP_WALL_T = _MIN_SOLID                                 # 1.60, four extrusions
SEP_WALL_X0 = RIM_X0
SEP_WALL_X1 = RIM_X0 + SEP_WALL_T                       # 22.25, the chamber's new -X face
#
# THE SHIFT IS DERIVED FROM A WINDOW, NOT CHOSEN, AND JP'S 0.45 IS OUTSIDE IT.
# At +0.45 the driver clears the wall by 0.40 as intended -- but the MIDFRAME'S LOCATING GROOVE
# is drawn at driver + 2*DRIVER_CLR, so it is 1.20 wider per side than the driver, and at +0.45
# its -X edge lands 0.20 INSIDE the new wall's footprint. That groove is a 0.60-deep channel cut
# into the very face this wall bears on, so the overlap would be a leak path running the entire
# length of the wall built to stop leaks. Two bounds, therefore:
#
#     groove -X edge >= the wall's chamber face   ->  shift >= 0.65
#     groove +X edge <= RIM_X1 (the case wall)    ->  shift <= 0.95
#
# and the shift is the CENTRE of that window, so neither bound is sat on. 0.80.
_GRV_HALF = (DRIVER_H + 2 * DRIVER_CLR) / 2
_shift_lo = (SEP_WALL_X1 + _GRV_HALF) - (RIM_X0 + RIM_X1) / 2
_shift_hi = (RIM_X1 - _GRV_HALF) - (RIM_X0 + RIM_X1) / 2
# >>> ⚠️ THAT WINDOW IS NOW EMPTY, AND IT IS A FACT TO RECORD RATHER THAN A FAILURE TO RAISE. <<<
# The no-lip solve (§4b) spent the rim's slack walking the cell bore +X, so a MIN_SOLID wall
# standing in the DRIVER'S lane no longer has anywhere to be. That retires the SEP_WALL option
# permanently instead of leaving it as a tempting near-miss for the next round: the separator
# that IS built is SEP2, and SEP2 survives this change precisely because it does NOT stand in
# the driver's lane -- it sits between RIM_X0 and the driver, and DRV_SHIFT below is solved to
# keep its full section. The assert is inverted: if a window ever reopens here, something gave
# the rim its slack back and BOTH separators want re-deriving together.
assert _shift_hi <= _shift_lo, (
    f"the SEP_WALL shift window has REOPENED at [{_shift_lo:.2f}, {_shift_hi:.2f}] -- the rim "
    f"has slack again, so the no-lip solve has been weakened or the driver has shrunk. "
    f"Re-derive SEP_WALL and SEP2 together; do not just widen one of them")
# >>> AND THE GATE KILLED THAT WALL AT 21.50 mm3. THE SHIFT IS NOT BUILT. WHY, IN NUMBERS. <<<
#
# The window above is real but it is not the binding one, because it never asked where the STRIP
# actually sits. prot_phantom() places the body at PROT_PKT_X0 + PROT_PKT_CLR, so its +X face is
# at x 21.05 -- 0.40 PAST RIM_X0, into space that used to be open chamber and is now wall. The
# strip fouled the cover by exactly PROT_L * PROT_T * PROT_PKT_CLR = 21.50 mm3 and check 13 said
# so. The assembly clearance the pocket was always carrying is the thing the wall wants to stand
# in. And the pocket cannot move -X to buy the 0.40 back: at the pocket's top Z the cell bore's
# edge is 15.87 against PROT_PKT_X0 16.15, i.e. 0.28 available against 0.40 needed -- the 18650
# pins it.
#
# >>> THE WALL IS NOW BUILT, BUT NOT AS SEP_WALL_T AND NOT BY SHIFTING. SEE §4c-b. <<<
# DRIVER_CLR came back from JP's bench at 0.40 and DRIVER_H calipered 27.5, which moves the
# groove's -X edge to 21.55 and leaves a 0.50 lane over the strip -- so the wall is stepped
# (0.90 above the strip pocket, 0.50 beside it) rather than 1.60 anywhere. The constants and the
# full derivation live with the STRIP in §4c-b, because the strip is what pins them; the two
# names below survive only as the r11 proposal the §4c-b control keeps rejecting.
#
# DRV_SHIFT STAYS 0, and now for a measured reason rather than a deferred one: the case wall
# caps the shift at _shift_hi = 0.90, so the thickest wall any legal shift can reach is 1.40 --
# still under MIN_SOLID. A shift would buy a thicker EXPERIMENTAL wall and move the grille
# field, the witness outline and the acoustic centre on the part JP is printing. Asserted in
# §4c-b so nobody re-opens it from prose.
# ⚠️ NO LONGER ZERO, AND IT IS SOLVED RATHER THAN PICKED.  DRV_CX is derived as the rim's
# CENTRE, so when the no-lip solve walks RIM_X0 +X the driver only follows by HALF of it -- and
# SEP2, which is pinned between RIM_X0 and the driver's body, gets crushed by the difference.
# Left at zero it collapses from 0.90 to 0.461, i.e. under even SEP2_T_THIN. That is the whole
# reason DRV_SHIFT exists. Solve it so SEP2 keeps its FULL section and the driver keeps
# SEP2_DRV_CLR; the +X side then lands on 0.42, which is DRIVER_CLR with 0.02 to spare.
_SEP2_T_WANT = 0.90                     # SEP2_T_FULL, bound in 4c-b below; asserted against there
DRV_SHIFT = (RIM_X0 + _SEP2_T_WANT + DRIVER_H/2 + 0.40) - (RIM_X0 + RIM_X1) / 2   # +0.439
assert RIM_X1 - ((RIM_X0 + RIM_X1)/2 + DRV_SHIFT + DRIVER_H/2) >= DRIVER_CLR, (
    f"the shifted driver's +X face leaves "
    f"{RIM_X1 - ((RIM_X0+RIM_X1)/2 + DRV_SHIFT + DRIVER_H/2):.3f} to the case wall, under "
    f"DRIVER_CLR {DRIVER_CLR}. The no-lip solve has taken more X than the rim had -- give some "
    f"back at CELL_WALL_X, do NOT thin SEP2 to pay for it")
DRV_CX    = (RIM_X0 + RIM_X1) / 2 + DRV_SHIFT           # 36.50
DRV_CY    = (RIM_Y0 + RIM_Y1) / 2                       # 52.40 -- the comment said 42.60 until
                                                        # 2026-08-01, and that was never right at
                                                        # any RIM_Y0: plainly wrong, not drift.

# ---- driver locating groove: alignment only, the tape does the work ----
LIP_DEPTH = 3 * LH                                      # 0.60
LIP_WIDTH = 1.20
# ---- the plateau that refills the vent hexes so the rim lands on solid material ----
PLATEAU_MARGIN = 2.00
# ============================================================================
# 5g. COVER RETENTION.  THE UNDERCUT HOOKS ARE DEAD.  READ THIS BEFORE REVIVING THEM.
# ============================================================================
#
# >>> VERDICT (JP, 2026-08-01): "the cavity is bridging too far for the PLA to be able to <<<
# >>> do those kind of tolerances."  THE HOOKS ARE NOT COMING BACK.                      <<<
#
# What used to be here: two L-shaped barbs on the cover at x = 4.50 and x = 45.50, each dropping
# into an 8.00 x 4.60 recess cut into the midframe's back face and sliding +Y under a lip, plus
# the one M3 x 22. The engagement was HOOK_LIP_T = 0.60 of lip standing under a HOOK_SLOT_D =
# 0.80 slot, 8.00 wide. Three separate reasons it cannot be printed, and only the first was
# JP's -- the other two are this file's own arithmetic, found while replacing it:
#
#   1. THE POCKET'S CEILING IS A BRIDGE, AND IT IS IN THE BED FACE. The midframe prints back-
#      face-down, so `p -= bx(..., BACK_Z, BACK_Z + HOOK_D)` is a void that starts AT THE BED
#      and is roofed at BACK_Z + 1.40 -- an 8.00 x 7.80 mm flat ceiling with nothing under it.
#      The evidence is a day old: issue #47, the desk stand's grille, where 0.90mm webs
#      collapsed on this machine on this filament. A 0.60mm lip cantilevered off one edge under
#      a 62mm2 bridge is a worse ask than the webs that already failed.
#   2. AND IT COULD NEVER HAVE GONE TOGETHER ANYWAY. The barb needed HOOK_BARB_L - HOOK_CLR =
#      2.90mm of +Y slide with the parts already mated. The driver hangs DRIVER_T = 10.00 below
#      BACK_Z into the cover's sealed cavity and the rim's high-Y wall stands the cavity's full
#      19.40 -- the clearance between them is (RIM_INNER_Y - DRIVER_W)/2 = 2.40mm, see check 8d.
#      A 2.90mm slide drives the rim wall through the speaker. NO CHECK IN THIS FILE LOOKED, and
#      the driver is a phantom, so no boolean could have. Check 8d now sweeps the assembly.
#   3. IT RETAINED THE WRONG 5mm OF AN 74mm COVER. Both hooks and the screw sat inside
#      y 18.60..23.40. Everything above y = 23.40 -- the cell bay, the whole sealed cavity, the
#      brow -- was held by nothing at all and would have gapped open along both long edges.
#
# ---------------------------------------------------------------------------
# THE REPLACEMENT, PICKED BY JP: DOVETAIL SLIDES ON BOTH LONG WALLS + THE SAME ONE SCREW.
# ---------------------------------------------------------------------------
#
# >>> THE DEFINING CONSTRAINT IS PRINT ORIENTATION, AND IT IS THE SAME FOR BOTH PARTS. <<<
#
# PRINT_LIFT (see section 8) translates each part in Z ONLY -- midframe by -BACK_Z, cover by
# -COVER_Z0. Neither is rotated. So MODEL +Z IS PRINT UP ON BOTH PARTS, and a face's angle in
# this file's coordinates IS its as-printed angle. That single fact is what makes the geometry
# below checkable at all, and check 8b asserts it rather than trusting this comment.
#
# The rule that follows: every face of the joint must be VERTICAL or at least 45 degrees from
# horizontal, and NO void may have a flat roof.
#
# ---------------------------------------------------------------------------
# ROUND 2, THE SKEW RAILS: ALSO DEAD, AND FOR A DIFFERENT REASON THAN THE HOOKS.
# ---------------------------------------------------------------------------
#
# They ran along both long walls, and their cross-section was a SKEW rather than a flare --
# the void kept its 1.20 width and translated 0.60 outboard as it rose -- because the side
# cable channels (ember_case.py:1541) cut the flank at z CAV_FLOOR..PCB_BOT, leaving only the
# 2.60 floor beneath them, and a flared dovetail's 45-degree gable would not fit in it.
#
# That reasoning was sound and the geometry gated green. It was still unprintable, because the
# whole exercise was conducted in the wrong units: squeezing a joint into 2.60 of Z and 2.60 of
# X produced a 0.60mm SOLID tongue, which is a third thinner than the solid webs #47 measured
# collapsing on this machine. THE CONSTRAINT WAS REAL AND THE CONCLUSION WAS WRONG -- the right
# answer to "the joint does not fit in the wall" was never "make the joint smaller", it was
# "this is the wrong wall". Kept here because the arithmetic below reuses it: the long walls
# are eliminated by exactly the budgets this paragraph worked out.
#
# >>> ROUND 3, AND THE FIRST TWO ARE THE EVIDENCE.  JP, ON SEEING THE SKEW RAILS RENDERED: <<<
# >>> "the dovetail is way too tiny of features for my Ender 3 with PLA."  HE IS RIGHT.      <<<
#
# ⚠️ AND THE ERROR WAS MINE IN A PRECISE, NAMEABLE WAY. The comment that used to sit here cited
# both halves of this machine's calibration set on ONE LINE -- "SLOT_W's 0.60 VOID prints open
# and #47's 0.90 WEBS collapsed" -- and then made the tongue a 0.60 SOLID rib, citing the void
# as its justification. A void is not a solid. 0.60 of solid is a THIRD THINNER than the solid
# class this machine is documented to have failed, and the counter-evidence was in the same
# sentence. Nothing in the check suite could see it: every check here measures whether the
# geometry is SELF-CONSISTENT and printable in principle -- no bridge, faces >= 50 degrees,
# capture > clearance -- and NOT ONE OF THEM KNOWS WHAT THIS MACHINE CAN HOLD. That missing
# lens is why check 8a now exists, and why its control is #47's own 0.90.
#
# ---------------------------------------------------------------------------
# WHERE A CHUNKY JOINT CAN GO.  THE ANSWER IS NOT "THE SAME PLACE, BIGGER".
# ---------------------------------------------------------------------------
#
# At a 1.60 minimum solid and a 0.45 per-face clearance, measured against the live constants:
#
#   -X WALL IS DEAD. OX0 to the cell's own surface is 2.50 of X, total. Skin 1.60 + clearance
#     0.45 leaves a 0.45 tongue; even at a 1.20 skin (already below the failed class) it is
#     0.85. The cell bore sits CELL_BORE_CLR from the wall's inner face and that is the whole
#     story -- there is no arrangement that reaches 1.60.
#   +X WALL IS ALSO DEAD, less obviously. A chunky joint needs 4.90 of X and is 3.13 deep. The
#     side wall is WALL wide; past it the midframe is only the 2.60 floor, and the gable's apex
#     lands over that floor. It would break into the board cavity.
#   THE TOP BLOCK IS THE ONLY VIABLE SITE, and it is viable by a mile: solid BACK_Z..SEAM_Z,
#     14.40 tall, full width, no cell, no seal rim, no cable channel.
#
# ---------------------------------------------------------------------------
# ROUND 4: AND THE BROW DOVETAIL DIED TOO, ON THE ONE AXIS NOBODY WAS MEASURING.
# ---------------------------------------------------------------------------
#
# >>> JP, having double-stick-taped the speaker to the printed midframe:                  <<<
# >>> "the backpack can't involve any sliding, it has to come straight down."             <<<
#
# A dovetail is an undercut, and an undercut needs a slide. The driver is now a TAPED PART on
# the midframe's back face, so any Y travel shears the cover's rim wall across a bonded
# speaker. Rounds 1-3 all died on this same axis and it is worth naming: hooks (a bridged
# pocket in a bed face), skew rails (0.60 SOLID ribs on a machine that failed 0.90 ones), brow
# dovetail (needs a slide). EVERY SLIDE-BASED SCHEME WAS DOOMED FROM THE MOMENT THE DRIVER
# BECAME A TAPED PART -- which this model already implied, because RIM_INNER_Y is set by the
# driver's tape pad, and which nobody read as an ASSEMBLY-ORDER constraint until JP put tape on
# plastic. Check 8d is now a straight-down sweep and it sweeps the driver, because that is the
# object the whole question is about.
#
# ---------------------------------------------------------------------------
# WHAT IT IS NOW: TWO M3 x 22, ON THE CASE'S OWN CENTRELINE, STRAIGHT DOWN.
# ---------------------------------------------------------------------------
#
# >>> AND THE CENTRELINE IS THE FINDING, NOT A TIDY-UP. <<<
#
# Round 4b/4c proved that THE CELL LANE MAKES THE ENTIRE -X HALF OF THE COVER UNFASTENABLE:
# for x < CELL_X1 the bore owns y 20.20..89.80, y >= BAY_Y1 fails SCREW_EDGE_MIN against the
# y = MOB_OY1 end, and y <= BAY_Y0 fails it against COVER_Y0. There is no valid -X screw
# position at any y. The instinct after that is to put the top screw where there is room --
# out at x = 46 on the +X half -- and that is exactly wrong: it would leave the -X edge
# 28.95mm from the nearest fastener and the +X edge 26.95, i.e. it would SPEND the asymmetry
# rather than absorb it. Putting BOTH screws on (OX0+OX1)/2 makes the two long edges
# equidistant at 27.95 each. The -X half still cannot hold a screw; the centreline is simply
# the furthest -X that any fastener can legally reach, and standing there costs the +X edge
# nothing. Check 8f prints both numbers.
# ⚠️ SCREW_EDGE_MIN IS NOT A STYLE RULE. Two builds were lost to it and both are worth keeping.
# At y = 19.20 the d5.80 counterbore spanned y 16.30..22.10 against a part starting at
# COVER_Y0 = 18.00, so 1.70mm of it hung off the end: the "hole" was a NOTCH in the outline and
# the head had no annular seat on its low-Y side. EVERY NUMERIC CHECK PASSED -- 3.20mm of
# engagement, pilot clear of the board, seal ring 100% solid. Only a slice of the finished mesh
# showed it. Then 21.50 failed for a second reason the first fix did not cover: the bed face
# carries a 0.80 CHAMFER, and a chamfer running into a hole 0.60 away cannot produce a valid
# face -- OCC threw StdFail_NotDone from inside chamfer_outline(). So the edge distance owes the
# counterbore's own radius AND the chamfer AND margin, and its assert lives at MODULE level
# because the check suite runs after the geometry that would already have died.
SCREW_EDGE_MIN  = CBORE_D/2 + CHAMFER + 0.50            # 4.20
# ⚠️ THE LANE IS SOLVED, AND IT IS SOLVED AGAINST THE PROTECTION STRIP, NOT AGAINST SYMMETRY.
# Both screws share one x, and that x is as far -X as the d5.80 counterbore can sit before it
# breaks into the shared divider's base (the counterbore's floor lands 0.80 above CAV_Z0, i.e.
# INSIDE the compartment, so "the wall is thick enough" is not the question -- the divider is).
# Everything else about the lane follows: it leaves the widest possible +X pocket for the strip
# in the lower band (§5f), and it carries both fasteners 1.45mm closer to the -X edge, which is
# the one edge of this part that can never hold a screw at all.
SCREW_LANE_X    = RIM_X0 + CBORE_D/2                    # 23.55
# ⚠️ 7.00 WAS TOO SMALL, and the reason is not obvious from the section: CBORE_DEPTH is 3.00
# and COV_WALL is only 2.20, so THE COUNTERBORE IS DEEPER THAN THE WALL IT IS SUNK IN. Its
# floor lands 0.80 above CAV_Z0 -- inside the compartment -- so the head does not bear on the
# outer wall at all, it bears on a boss. At d7.00 that is (7.00-5.80)/2 = 0.60mm of annulus
# against ember_case's BOSS_MIN_ANN of 1.00. The seat probe read 86.9% and found it. It is
# defined HERE, above the screw positions, because the TOP screw is placed by the boss's
# radius rather than by its counterbore's -- see below.
SCREW_BOSS_D    = 9.00                                  # (9.00-5.80)/2 = 1.60 of annulus
SCREW_BOSS_H    = 4.00                                  # CAV_FLOOR -7.10 -> -3.10, PCB is -1.60
SCREW_XY        = (SCREW_LANE_X, COVER_Y0 + SCREW_EDGE_MIN + 0.40)   # (23.55, 22.60) the chin
# ⚠️ THE TOP SCREW'S EDGE DISTANCE IS SET BY THE BOSS, NOT THE COUNTERBORE, AND THE FIRST
# VERSION USED THE COUNTERBORE. SCREW_BOSS_D/2 is 4.50 against SCREW_EDGE_MIN's 4.20, so a
# screw placed by the counterbore's rule left the d9.00 boss standing 0.30 PROUD of the case's
# own end face -- on BOTH parts. The bounding box said 90.98 where the profile says 90.68, and
# the dock check found it as interference. A bump on the silhouette is the defect JP caught by
# eye at the top of this case once already.
TOP_SCREW_XY    = (SCREW_LANE_X,
                   MOB_OY1 - max(SCREW_EDGE_MIN, SCREW_BOSS_D/2 + 0.20))    # (23.55, 85.98)
SCREWS          = (SCREW_XY, TOP_SCREW_XY)
# ---- THE TOP COLUMN STEPS.  Recorded as the priced escape in f0d72a3; the no-lip solve is
# what finally needed it, and the vent's own assert is what asked for it by name.
#
# SCREW_BOSS_D is THE HEAD'S ANNULUS -- (9.00 - CBORE_D)/2 = MIN_SOLID of bearing ring -- and an
# annulus only exists where there is a counterbore. Above the counterbore's roof the column
# carries nothing but the shank, so d9.00 up there is 1.60 of material per side bought for no
# reason and spent somewhere expensive: the column stands IN THE DIVIDER, and the divider is
# where the internal labyrinth vent lives. Flush moved the top screw -Y and the full-diameter
# column crowded the vent's window to 4.659 against the 5.485 a LAT hex needs.
#
# So: full section while it is an annulus, shank-plus-a-printable-wall above. The full run is
# kept COV_WALL past the seat so check 11b's seat probe (which samples 0.20 ABOVE the roof)
# still lands on solid ring -- the step is not allowed to eat the bearing surface it protects.
# Narrowing UPWARD is free in the cover's print orientation: the ledge faces +Z, nothing bridges.
TOPBOSS_STEP_Z  = COVER_Z0 + CBORE_DEPTH + COV_WALL      # -26.10
TOPBOSS_D_UP    = SCREW_D + 2 * _MIN_SOLID               # 6.50 -- shank + a printable wall
assert TOPBOSS_STEP_Z > COVER_Z0 + CBORE_DEPTH + 0.20, (
    f"the column steps at {TOPBOSS_STEP_Z:.2f}, inside check 11b's seat probe slab -- the "
    f"head's bearing ring would be measured on the stepped section and read as broken out")
assert TOPBOSS_D_UP >= SCREW_D + 2 * _MIN_SOLID, (
    f"the stepped column is d{TOPBOSS_D_UP:.2f} around a d{SCREW_D} shank, leaving "
    f"{(TOPBOSS_D_UP-SCREW_D)/2:.2f} of wall")
# CONTROL: the step must actually BUY something at the divider, or it is complexity for nothing.
assert TOPBOSS_D_UP < SCREW_BOSS_D - 0.5, (
    "control failed: the stepped diameter is no smaller than the full one, so the step frees no "
    "divider and the vent window it was cut for is unchanged")
# ⚠️ LENGTH IS DERIVED FROM THE COVER'S DEPTH, NOT CHOSEN -- and JP has explicitly released it
# as a constraint ("i don't ccare about the lendthte of the screws"). Every millimetre the
# backpack grows comes off the thread one for one: at BAY_EXTRA 1.60 this had to be 25 because
# an M3x22 engaged only 1.80, under check 11's floor, and it would have felt perfectly tight
# going in. Back at flush, 22 engages 3.40. Check 11 is the arbiter; the report carries the
# shopping line.
MOB_SCREW_LEN   = 22.00                                 # M3 x 0.5 x 22 ISO 4762, under-head
MOB_PILOT_DEPTH = (BACK_Z - CAV_FLOOR) * -1 + SCREW_BOSS_H   # 2.60 floor + 4.00 boss = 6.60
# ---- WHY THE TOP SCREW ALSO NEEDS A MIDFRAME BOSS, WHICH IS NOT WHAT THE SITE LOOKS LIKE ----
#
# At (25.00, 87.80) the midframe is solid BACK_Z..SEAM_Z -- 14.40mm, no pocket, no cavity. The
# obvious reading is "bore a pilot into it and stop thinking". That reading is wrong by 1.40mm.
# The board pocket's +Y wall is at PY1 = 86.35 and the pilot's own -Y extreme is at
# 87.80 - PILOT_D/2 = 86.55, so ABOVE CAV_FLOOR the web between the bore and the board cavity is
# 0.20mm. Not a hole -- a 0.20 wall, which is a quarter of the thinnest thing this machine has
# ever printed successfully, and the self-tapper would push it into the cavity on the first
# turn. Every check in this file would have passed: engagement 3.40, edge distances fine, no
# collision with the board, seal untouched.
#
# The fix is the chin screw's own trick, mirrored: a boss that grows UP into the board cavity,
# where standing proud costs nothing. Coaxial with the screw and the same d9.00, it fills
# y 83.30..86.35 of the pocket's +Y end locally and the web becomes the boss's own radius less
# the pilot's -- 3.25mm, all the way round. Whether that intrudes on anything is not reasoned
# about: the STEP clearance boolean measures it, and the region it fills (x 20.50..29.50,
# y 83.30..86.35, z -7.10..-3.10) reads EMPTY in the vendor solid -- the nearest back-side
# feature is the PCB antenna pour at z -1.65, 1.45mm above the boss's top.
#
# ⚠️ AND THE PILOT MUST STOP AT THE BOSS'S TOP. MOB_PILOT_DEPTH lands it exactly there
# (BACK_Z + 6.60 = -3.10 = CAV_FLOOR + SCREW_BOSS_H). One millimetre deeper and its last
# millimetre is back in the 0.20 web this boss exists to abolish.
# ---- THE UNVALIDATED LATTICE.  Shared with the stand ON PURPOSE. ----
#
# >>> JP: "we have proven two that collapse and none that survives." <<<
#
# The cooling fields below use HEX_R / HEX_WEB -- the STAND'S OWN grille constants, 4.75 across
# flats on a 1.25 web -- and that is the OPPOSITE call from GLOW_R and GLOW_WEB three sections
# down, which were deliberately PINNED away from this same pair after #47. The difference is
# what the two features are for. The glow window's size is set by the 5.50mm cavity band it
# lives in, so inheriting another part's lattice was pure accident and it broke the fit. The
# cooling fields have no such constraint and exist precisely to BE the pattern under test: if
# JP prints these and the 1.25 web survives, that answers #47 for the whole family at once,
# and one shared pair of constants is how the answer propagates. If it collapses, it collapses
# everywhere in one place.
#
# ⚠️ SO THIS WEB IS BELOW THE 1.60 MINIMUM SOLID FLOOR AND IT IS *NOT* IN CHECK 8a's LIST.
# It is not an oversight and it must not be "fixed" by adding it -- 8a would fail the build on
# a pattern that is deliberately on trial. It is printed as an [unvalidated] line instead, so
# it is loud rather than silent.
# ---- THE SMALL MESH, AND WHY ITS WEB IS NOT ONE NUMBER ----
#
# >>> JP: "i want the top hex vents at the top of both peices to be the same hex grill on <<<
# >>> the back of the midframe; the hexasgons are too big"                                <<<
#
# The reference is the back grill: 3.2 across flats on a 0.80 web, and it has PRINTED -- his r1
# midframe carries ~113 of those cells. So MESH_AF matches it exactly.
#
# ⚠️ BUT THE WEB CANNOT MATCH EVERYWHERE, AND THE REASON IS BORE DIRECTION, NOT WIDTH. The
# back grill's cells are VERTICAL PRISMS IN A BED FACE -- every layer supported by the one
# below, which is why 0.80 survives there. The fields at the +Y ends are HORIZONTAL BORES, the
# same class as the stand's grille, where 0.90 COLLAPSED (#47) and 1.25 is the current
# unvalidated fix. Matching 0.80 into a horizontal bore would put these fields THINNER THAN THE
# WEB THAT ACTUALLY FAILED, so the web is chosen per class and the class is stated per field:
#
#   blind battery-side deboss  0.60 of surface relief, NO BORE  -> MESH_WEB_BLIND 0.80, and it
#                              cannot fail as a web at all: the material behind it is 1.60 of
#                              continuous membrane, not a rib.
#   LED-side through field     horizontal bores, 2.20 long      -> MESH_WEB_BORE 1.25
#   midframe +Y end vent       horizontal bores, 2.60 long      -> MESH_WEB_BORE 1.25
#
# JP asked for the HEXAGONS to be smaller, which is cell size; that is delivered exactly. The
# web is the one thing he did not ask about and the one thing #47 measured.
MESH_AF        = 3.20                   # = the back grill's, JP's own reference
MESH_R         = MESH_AF / math.sqrt(3)
MESH_WEB_BLIND = 0.80                   # PROVEN: the back grill's own web, printed on r1
MESH_WEB_BORE  = 1.25                   # horizontal bores stay clear of #47's 0.90 collapse
LAT_AF   = math.sqrt(3) * HEX_R                         # 4.75 across flats -- the stand's own
LAT_WEB  = HEX_WEB                                      # 1.25 -- the stand's own
LAT_R    = HEX_R                                        # circumradius; AC = 2*LAT_R = 5.485
MIN_SOLID = _MIN_SOLID                  # 1.60 = four extrusion widths. Check 8a enforces it.

# ---- MODULE-LEVEL SCREW ASSERTS, so they cannot be outrun by the geometry they constrain ----
for _sxy, _who in ((SCREW_XY, "chin"), (TOP_SCREW_XY, "top")):
    for _e, _d in (("cover bottom edge", _sxy[1] - COVER_Y0),
                   ("cover top edge",    MOB_OY1 - _sxy[1]),
                   ("cover -X edge",     _sxy[0] - OX0),
                   ("cover +X edge",     OX1 - _sxy[0])):
        assert _d >= SCREW_EDGE_MIN - 1e-9, (
            f"the d{CBORE_D} {_who} counterbore at {_sxy} is {_d:.2f}mm from the {_e}, under "
            f"the {SCREW_EDGE_MIN:.2f} it needs (its own radius + the {CHAMFER} bed chamfer + "
            f"margin). Too close and it is a notch in the outline; closer still and the chamfer "
            f"will not build at all")
assert (19.20 - COVER_Y0) < SCREW_EDGE_MIN and (21.50 - COVER_Y0) < SCREW_EDGE_MIN, (
    "control failed: the two rejected screw positions (19.20 notched the outline, 21.50 killed "
    "the chamfer) both read as having adequate edge distance")
# and the chin boss must not run into the seal rim's wall on its way back
assert SCREW_XY[1] + SCREW_BOSS_D/2 <= RIM_Y0 - RIM_WALL + 1e-9, (
    f"the chin screw boss reaches y={SCREW_XY[1] + SCREW_BOSS_D/2:.2f}, past the retention "
    f"strip's end at {RIM_Y0 - RIM_WALL:.2f} -- it would foul the seal rim's low-Y wall")
# ...and the top boss must not reach back into it from the other side
assert TOP_SCREW_XY[1] - SCREW_BOSS_D/2 >= RIM_Y1 + RIM_WALL + 1e-9, (
    f"the top screw boss reaches y={TOP_SCREW_XY[1] - SCREW_BOSS_D/2:.2f}, into the seal rim's "
    f"high-Y wall at {RIM_Y1 + RIM_WALL:.2f}")
# THE ONE THAT KILLED ROUND 4c, STATED SO IT CANNOT COME BACK SILENTLY: a top screw cannot go
# on the -X half at any y, because the cell lane owns it.
assert not (SCREW_LANE_X - CBORE_D/2 >= OX0 + COV_WALL and SCREW_LANE_X + CBORE_D/2 <= CELL_X1), (
    "control failed: the screw lane reads as fitting inside the cell bore's X span, so the "
    "arithmetic that eliminated every -X fastener position is no longer being applied")


def _yprism(pts, y0, y1):
    """Extrude an ABSOLUTE (x, z) cross-section along +Y.

    ⚠️ ITS CALLER LIST HAS TURNED OVER COMPLETELY AND A HANDOFF NOTE SAID OTHERWISE. It was
    written for the dovetail, then "kept because the spring tunnel uses it" -- and both of
    those are now deleted. Its one live caller is the +Y end cooling vent (§5h). Kept on that
    evidence, not on the note: `grep _yprism` is the check, and it is two lines long.

    Rot(-90,0,0) sends sketch +v to world -Z and the extrude direction to world +Y -- the same
    trick cyl_y() and the polarity markings use -- so a sketch point (x, -z) lands at (x, y, z).
    """
    sk = make_face(Polyline(*[(x, -z) for (x, z) in pts], close=True))
    return Pos(0, y0, 0) * (Rot(-90, 0, 0) * extrude(sk, y1 - y0))


GRILLE_CELL_N = None                                    # set by back_cover(), read by the checks
TOPMESH_N     = None                                    # ditto, the blind end-face mesh
TOPVENT_N     = None                                    # ditto, the LED-side through field
# Narrowest a clipped grille opening may be before it is dropped from the cutting set. Above
# HEX_WEB's 0.90 print floor and above SLOT_W's 0.60 proven void, with margin: a hole this
# narrow in a 2.20 baffle is a slot the nozzle has to trace, not a feature that resolves.
GRILLE_MIN_W  = 1.20

# ============================================================================
# 5c. THE FAST-CHARGE OPTION.  A POCKET THAT COSTS NOTHING WHEN EMPTY.
# ============================================================================
#
# Onboard charging (5b) is the DEFAULT and needs no extra hardware -- but at 290 mA a 3400 mAh
# cell is ~15.8 h. A TP4056-class module (or its USB-C sibling, TP4057/IP2312) runs ~1 A, which
# is 3400/1000 x 1.35 = ~4.6 h. That is the option; it is not a necessity, and the geometry is
# shaped so an unpopulated build pays nothing for it:
#
#   * THE POCKET IS THREE RIBS ON A FLOOR THAT WAS ALREADY EMPTY. No cavity is hollowed for it,
#     no wall is thinned, no check depends on it. Leave it unpopulated and it is decoration.
#   * THE APERTURE IS A KNOCK-OUT, NOT A HOLE. The default cover is SOLID here: the port is cut
#     from the INNER face only, leaving TP_KNOCKOUT of wall standing at the outer face. Populate
#     the module and you slice that membrane out with a knife. Ship it empty and there is no
#     opening into the cell bay at all -- asserted both ways at check 13.
#
# ⚠️ ELECTRICAL, AND EXPLICITLY NOT DECIDED HERE: with the board's own charger AND a TP4056 both
# wired to one cell, plugging in both USB ports at once puts TWO CC/CV chargers on the same
# cell, fighting each other. The safe wirings are (a) the TP4056 as the ONLY charge path with
# the board's BAT as load-only, or (b) a "never both at once" usage rule. Picking between them
# is JP's call -- see the issue. This file provides the pocket, the aperture and the warning.
TP_W, TP_L, TP_H = 26.00, 17.00, 4.00      # generic TP4056 module: X x Y x Z, lying flat
# ---- AND A PROTECTION STRIP, WHICH IS WHAT THE POCKET NOW HOLDS ----
#
# >>> RE-PRIMARYING TO BARE CELLS SHRANK THE FREE COMPARTMENT PAST WHAT A TP4056 NEEDS. <<<
#
# The free region above the seal rim is RIM_Y1+RIM_WALL .. BAY_Y1 = 13.40mm of Y, and a TP4056
# is 17.00 in its short axis -- it does not fit in EITHER orientation (26.00 in the other).
# Check 13 measures that rather than asserting it in prose. Getting it back costs the entire
# 5.90mm the bare-cell re-primary just saved, because the rim cannot move: RIM_INNER_Y is set
# by the driver's 41.20 tape pad. THAT IS A TRADE FOR JP, NOT A CALL FOR ME -- and with bare
# cells the missing protection is the sharper of the two gaps, so the pocket is sized for a
# protection strip by default and the issue states the price of the alternative.
# ============================================================================
# 5f. THE 1S PROTECTION STRIP.  REQUIRED EQUIPMENT, NOT AN OPTION.
# ============================================================================
#
# >>> SETTLED BY THE PRIMARY SOURCE: docs/vendor/ES3C28P_Schematic.pdf. <<<
#
# I read the sheet rather than the note beside it. The battery area is exactly two blocks --
# "Battery charge and discharge management" (TP4054 U2, PROG R12 3.3K -> ~290 mA, SL2305 P-FET
# power path Q3, B5819W D8) and "Battery level detection" (200K/200K divider -> BAT_ADC).
# THERE IS NO PROTECTION BLOCK. JP1 (BAT) goes straight to the cell.
#
# So with bare cells the over-discharge floor is only the ME6217 LDO's dropout -- the device
# browns out around 3.4 V and THEN KEEPS DRAINING, ~9 uA through the divider alone plus
# quiescent. A cell left flat in a drawer goes to zero. That is why the strip is required
# equipment and not a nicety, and it is the part of the story a "it browns out first" reading
# misses.
#
# PROT_L is ESTIMATED, not measured: JP, 2026-08-01, "20mm about" -- an eyeball figure,
# so it carries +/-2 and the seat leaves that much end slack. W and T remain the class
# placeholders. If calipers ever land, the three constants are still the whole edit.
# Same date, JP froze the length trade: the case STAYS at 94.95 -- in-case TP4056 is
# permanently out (external bay chargers cover fast-charge for removable cells).
#
# THE CLASS IS CERTAIN (JP's photo): a 1S DW01 + dual-FET PCB with pre-welded nickel tabs at
# both ends, components on one face. Briefed class figure: 31.00 x 6.50 x 2.50.
#
# ⚠️ AND THE BRIEFED 31.00 DOES NOT FIT. The free compartment is RIM_X0..RIM_X1 = 30.10 wide,
# so the longest PCB that seats flat is 30.10 - 2*PROT_CLR = 29.30 -- short by 0.90. It does not
# fit rotated either (the compartment is only 13.40 in Y), nor on edge (a 31 strip against 19.40
# of depth), nor diagonally in plan (a 31 x 6.5 rectangle needs 30.96 of X at its best angle).
# The compartment cannot grow: X is pinned by the cell bore on one side and the case wall on the
# other, and Y by the driver's tape pad setting RIM_INNER_Y. So the placeholder is set to the
# MAXIMUM THAT FITS and the assert enforces it -- if JP's strip measures over 29.30 the build
# fails and says by how much, which is the right time to learn it rather than at assembly.
PROT_L_CLASS  = 31.00                                   # briefed class figure, for the record
PROT_CLR      = 0.40
# ⚠️ THIS IS NO LONGER THE BINDING LIMIT AND IT IS KEPT AS THE RECORD OF WHAT WAS. The bare
# compartment would seat 29.30; the chin screw's boss pad takes the -X end of the lower band,
# so the real limit is the one derived beside the strip's placement below. Both are printed.
PROT_L_MAX    = (RIM_X1 - RIM_X0) - 2*PROT_CLR          # 29.30, the bare compartment
PROT_L        = 21.50           # JP re-measured: "a little over 21" — seat derives to 22.30 between ribs
PROT_W        = 4.50            # JP-MEASURED 2026-08-02: "like 4.5mm wide"
PROT_T        = 2.50            # JP-MEASURED 2026-08-02: "and 2.5mm thick"
                                # (the placeholder was right, which is luck, not evidence)
PROT_COMP_CLR = 1.00            # over the component face (the FETs are the tall parts)
PROT_RIB_W    = 1.60
# ---- THE STRIP'S Z-RETENTION IS ITS TABS, AND THAT IS STATED, NOT IMPLIED. ----
#
# JP asked what holds the metalwork. For the strip the honest answer is: the two nickel tabs it
# is soldered to at BOTH ends, one running into the divider's wire groove and one to the
# spring. Those are real anchors, not friction, and a lid-clip over the strip would be a
# DOWNWARD-FACING ledge in the cover's print orientation -- the bridging class JP rejected --
# and would also make the strip unfittable, since a 21.50 PCB cannot slide under clips inside a
# 22.30 seat. So: no clip, reliance recorded.
#
# What the ribs CAN do for free is stop it tipping, and at 1.20 against a 2.50 strip they did
# not: the PCB could ride up on one edge and sit proud. Raised to 12 layers = 2.40, just under
# the strip's own thickness so the ribs never lift it off its flat floor. Check 13b measures
# that the floor stays flat and that the sky above the component face stays clear.
# ⚠️ AND 2.40 WAS WRONG ONCE THE DETENTS WENT ON, IN A WAY ONLY THE MESH CHECK CAUGHT. A rib
# 0.10 SHORTER than the PCB has nothing at the PCB's top edge for a detent to grow out of, so
# the first version's bumps were FLOATING BOXES 0.10mm off the rib and 0.40mm off the board --
# and every numeric check passed. `_check_manifold` reported one non-manifold edge on the cover
# and that was the only sign. The ribs are OUTSIDE the strip's footprint, so their height was
# never what kept the board flat; 15 layers puts the detent's root on solid rib.
PROT_RIB_H    = 15 * LH                                 # 3.00 = PROT_T + PROT_DET_H, exactly
# >>> THE STRIP MOVES TO THE LOWER BAND, AND IT FIXES THREE THINGS AT ONCE. <<<
#
# JP's constraint is the metal, not the plastic: "the strip has to lie flat close to the battery
# so the already-soldered nickel strips reach the places." It used to sit CENTRED in the UPPER
# compartment, PROT_CX = 35.70, PROT_Y1 = 85.00, which was the worst place in the part:
#
#   1. IT BLOCKED THE TOP SCREW. Round 4c: the boss must reach y 83.30 (the edge rule less its
#      own radius) and the strip's top was 85.00 -- a 1.70mm overlap, and there is no x in a
#      30.10mm compartment where a d9.00 boss clears a 25.50mm pocket. Three escapes were tried
#      and all fail on arithmetic (move it -X: the conflict is the 83.30 line, not x; move it
#      -Y: its lowest legal top is 83.40 against the boss's 83.30, short by 0.10; thicken the
#      cover wall past CBORE_DEPTH: the pad lands exactly where the strip sits).
#   2. ITS B- TAB HAD TO REACH THE OTHER END OF THE BAY. The negative contact is at the bay's
#      -Y end; the strip was at +Y. That is a ~60mm run for a pre-welded tab, and it was the
#      LONGER of the two runs rather than the shorter.
#   3. ITS PIGTAIL HAD TO REACH THE LEAD PASS, which is at y 20.00..26.50 -- the far end again.
#
# In the lower band, y BAY_Y0..RIM_Y0-RIM_WALL, all three invert: the boss is unobstructed, the
# B- tab folds up into the leaf pocket a few millimetres away and IS the spring (§3b), and the
# pigtail exits into the lead pass directly across the divider. Only B+ makes the long run, in
# the groove that already exists for it.
#
# ⚠️ AND THE LOWER BAND WAS NOT FREE EITHER -- THE CHIN SCREW WAS ALREADY IN IT. Its boss pad
# runs x SCREW_LANE_X +/- 4.50 the full height of the band. At the old lane x = 25.00 that left
# x 29.50..50.75 = 21.25 for a pocket needing PROT_L + 2*PROT_CLR = 22.30. Short by 1.05. So
# the SCREW LANE moved -X to the furthest point its own d5.80 counterbore can reach without
# breaking into the divider's base -- see §5g -- which buys 1.45 and leaves 1.20 of clearance.
# That the same move also carries both screws 1.45mm closer to the -X edge, the one edge that
# can never hold a fastener, is a second reason and not the first one.
# >>> THE BODY LIVES IN THE BAY'S BOTTOM +X CORNER NOW.  §4c is why it fits at all. <<<
#
# Centred along the bay so both 34.25 tabs reach their fold seats (check 13d), tucked into the
# corner solid under the cell's shoulder, opening onto the bore so the cell lies on it.
# +X rather than -X because the other three corners are spent: -X bottom bought the ease
# (1.87 of wall left on its diagonal), -X top is the vent labyrinth's (z -18.40..-11.50), and
# the top pair cost the same growth as the bottom while making JP thread the strip in beside a
# seated cell instead of laying it down first.
PROT_PKT_CLR  = 0.40                                    # all round the body in its pocket
PROT_SOLDER   = 3.00                                    # joint room at the output end
PROT_CX       = None                                    # -> the bay, not the chin band
PROT_Y0       = (BAY_Y0 + CELL_TIP_Y)/2 - PROT_L/2      # body centred along the bay
PROT_Y1       = PROT_Y0 + PROT_L
# ============================================================================
# 5f-c. THE STRIP LIES BESIDE THE BATTERY, IN THE DIVIDER'S PLACE.
# ============================================================================
#
# >>> JP, after being told what it costs: "no strip and nickel lay besid ethe batteyr like <<<
# >>> i toild you" / "you can delete that inner wall it's fine" / "or modify it".           <<<
#
# Every other construction was measured and none closes at 39.00: the bay's corner solid is
# 0.73 short axis-aligned and cannot be rotated into a fit (no angle satisfies both the divider
# and the outer wall); a midframe straddle is 0.21 short; the upper compartment fits but puts
# the body 74.70mm of tab-path from the far leaf seat, needing 52.08mm of NEW soldered nickel
# against 23.25 of surplus. The divider's own 2.00 is the only space in the case, and it is
# 4.17 with the corner -- real clearance, plus room for the solder JP correctly points out will
# make his part thicker than 2.50.
#
# ⚠️ WHAT IT COSTS, SO NOBODY RE-LEARNS IT: the divider IS the sealed speaker chamber's -X
# wall -- one wall doing two jobs, as its own definition has said since it was written. Over
# RIM_Y0..RIM_Y1 the chamber and the cell bay become ONE VOLUME. Check 7b reports that side
# instead of asserting it, check 19c restates the ingress picture, and the report carries the
# opening map. This is an informed owner's decision, not an oversight, and it is recorded as
# one.
#
# The body lies FLAT ON THE BAY FLOOR beside the cell, mid-bay -- which is also what keeps the
# 34.25 tabs closing with no extension at all (check 13d). Its +X half stands clear of the cell
# entirely (the cell's surface has fallen away by then), so THE SOLDER JOINTS GO ON THAT SIDE
# and their thickness stops being a constraint.
PROT_PKT_X1   = RIM_X0                                  # up to where the divider used to be
PROT_PKT_X0   = PROT_PKT_X1 - PROT_W                    # 16.15, the body's -X edge
PROT_PKT_Z0   = CAV_Z0                                  # it stands on the bay's own floor
PROT_PKT_Z1   = PROT_PKT_Z0 + PROT_T + PROT_PKT_CLR
PROT_BOSS_CLR = 0.50            # plan clearance, strip corner to the chin screw's boss
# ============================================================================
# 5f-b. THE STRIP IS CASE-RESIDENT AND ITS HOME IS UNRESOLVED.  READ BEFORE MOVING IT.
# ============================================================================
#
# >>> JP, 2026-08-02: "the bms strip hugs teh battery" / "no the nickel struip stays in <<<
# >>> the case with the excess strip as little leaf springs" / "entire strip with nickel <<<
# >>> strips included is 90mm" / "soldered to the battery wires"                         <<<
#
# The architecture he describes is: the strip lives in the case permanently, lying flat in the
# CELL BAY against the cell's side; the surplus nickel folds into leaf springs at BOTH ends;
# its output is soldered to the pigtail. That is coherent and the length budget closes -- see
# the arithmetic in check 13d, which is printed every build.
#
# ⚠️ AND IT DOES NOT FIT, FOR A REASON THAT IS ARITHMETIC AND NOT PREFERENCE. The cell bore is
# INSCRIBED EXACTLY in the bay -- tangent on three sides, measured, not estimated:
#
#     -X extreme  -0.75 vs CELL_X0  -0.75    gap 0.00
#     +X extreme  18.65 vs CELL_X1  18.65    gap 0.00
#     bottom     -29.10 vs CAV_Z0  -29.10    gap 0.00
#     seated cell top -10.30 vs BACK_Z -9.70 -> 0.60 of headroom
#
# That is the X budget closing (check 3: bore + divider + driver pad = 51.50 of 51.50), not
# slack anyone forgot to use. A PROT_T strip needs PROT_T of clearance somewhere and there is
# 0.00 on three sides. The spendable X slack is (rim - driver pad - 0.50) = 1.40, still short,
# and spending it moves the divider, the rim, DRV_CX, the grille field and the bond plateau.
#
# So the case-resident strip needs the CASE to grow -- COVER_Z0 down ~2.5, or the X budget
# re-cut -- and PROT_W/PROT_T are still ⚠️ UNMEASURED placeholders. JP calipered the LENGTH
# (21.50) and the FLAT ASSEMBLY (90.0); he has never measured the section. Growing the backpack
# 2.5mm on a guessed thickness is not a change this file should make on its own.
#
# UNTIL THEN THE STRIP IS MODELLED WHERE IT WAS: the chin band pocket below. That is a
# STATEMENT OF AN UNRESOLVED ITEM, not a claim that the chin band is right -- if it stays
# there, the leaf-spring-at-both-ends chain and the "hugs the battery" geometry are both
# unbuilt, and the chamber wall's deletion loses the premise it was granted on (that the band
# would be empty).
BMS_PACK_FLAT_L = 90.00         # JP-MEASURED: strip body + both nickel tabs, laid flat
_INT_R        = max(OUT_R - COV_WALL, 1.0)              # the interior rbox's own radius, 4.25
_pkt_dx = PROT_PKT_X0 - CELL_AXIS_X
_pkt_need = math.sqrt(max((CELL_D_MAX/2)**2 - _pkt_dx**2, 0.0))
assert (CELL_AXIS_Z - CELL_BORE_CLR) - PROT_PKT_Z1 >= _pkt_need, (
    f"the seated body's top is {(CELL_AXIS_Z-CELL_BORE_CLR)-PROT_PKT_Z1:.2f} below the cell's "
    f"axis and the cell's own surface is {_pkt_need:.2f} down at that x -- THE CELL WOULD SIT "
    f"ON THE BODY. Move PROT_PKT_X0 +X (the cell's surface falls away fast there) or thin the "
    f"seat; do NOT grow the case, the envelope is JP's one hard line")
# THE SOLDER SIDE MUST BE CELL-FREE. JP: "once i solder teh battery wires it wil be thikcer."
# Past the cell's +X extreme there is no cell at any height, so joints and wire roots have the
# whole compartment above them and their thickness stops being a dimension anyone has to know.
assert PROT_PKT_X1 > CELL_AXIS_X + CELL_D_MAX/2, (
    f"the body's +X edge at {PROT_PKT_X1:.2f} does not clear the cell's surface at "
    f"{CELL_AXIS_X+CELL_D_MAX/2:.2f} -- there is nowhere on it for a solder joint to stand, and "
    f"JP has said twice that his joints make the part thicker")
# ...and the body must sit inside the span the divider actually vacated.
assert PROT_Y0 >= RIM_Y0 and PROT_Y1 <= RIM_Y1, (
    f"the body at y {PROT_Y0:.2f}..{PROT_Y1:.2f} runs outside the divider's deleted span "
    f"({RIM_Y0:.2f}..{RIM_Y1:.2f}) -- past either end a STUB is still standing and the body "
    f"would have to pass through it")
assert PROT_Y0 > BAY_Y0 and PROT_Y1 < CELL_TIP_Y, (
    f"the body at y {PROT_Y0:.2f}..{PROT_Y1:.2f} has run past a contact face "
    f"({BAY_Y0:.2f}/{CELL_TIP_Y:.2f}) -- the tabs fold at those faces")

# ============================================================================
# 4c-b. THE SEPARATOR WALL, BUILT AT LAST -- AND IT LIVES HERE BECAUSE THE STRIP PINS IT.
# ============================================================================
#
# §5f derives DRV_CX and reasons about this wall in prose; the CONSTANTS are here, below the
# strip, because the strip is what sets the wall's -X face. Putting them next to the driver is
# what produced r11's wrong answer twice: a lane derived from the driver alone never asks where
# the strip sits, and the strip is the binding party.
#
# >>> WHAT CHANGED SINCE r11 CALLED THIS BLOCKED: BOTH DRIVER NUMBERS ARE NOW MEASURED. <<<
# r11 refused to touch DRIVER_CLR while JP was bench-testing that exact fit, and was right to.
# The bench came back ("a little play, ~half a mm") and the fit is now 0.40 a side; the driver
# itself calipered 27.5, not the 27.0 class figure. Both land in this lane, in opposite
# directions, and the net is what it is:
#
#   the strip's +X face, at its full +X drift   x 21.05   (PROT_PKT_X0 + PROT_PKT_CLR + PROT_W)
#   the locating groove's -X outer edge         x 21.55   (DRV_CX - (DRIVER_H + 2*DRIVER_CLR)/2)
#   ---------------------------------------------------------------------------------------
#   the whole lane                                   0.50
#
# >>> SO THE BRIEFED "0.90 LANE" IS NOT THERE, AND THE GATE SAYS SO IN mm3. <<<
# A 0.90 wall standing on RIM_X0 (20.65) reaches x 21.55 and fouls the seated strip by exactly
# PROT_L * PROT_T * PROT_PKT_CLR = 21.50 mm3 -- measured by boolean before this was written, the
# same 21.50 check 13 threw at r11. 0.90 is the room between RIM_X0 and the groove; it is not
# the room between the STRIP and the groove, and the strip is the thing in the way.
#
# >>> AND NO DRIVER SHIFT SAVES IT.  THIS IS THE ARGUMENT THAT CLOSES THE QUESTION. <<<
# The case wall caps the shift at _shift_hi (the groove's +X edge may not pass RIM_X1), so the
# thickest wall ANY legal shift can produce is (21.55 + _shift_hi) - 21.05 = 1.40, still under
# MIN_SOLID. Shifting therefore buys a thicker EXPERIMENTAL wall and nothing else -- while
# moving the grille field, the witness outline and the acoustic centre on the midframe JP is
# printing. Not worth it: DRV_SHIFT stays 0 and the wall is stepped instead. Asserted below so
# the next reader does not have to re-derive it.
#
# THE STEP.  Full thickness everywhere the strip is not, thinned only where it is:
#
#     z PROT_PKT_Z1 .. BACK_Z   (85% of the height)   x 20.65..21.55   0.90   full section
#     z CAV_Z0 .. PROT_PKT_Z1,  over the strip's Y     x 21.05..21.55   0.50   thinned
#     z CAV_Z0 .. PROT_PKT_Z1,  elsewhere in Y         x 20.65..21.55   0.90   full section
#
# The step is a 0.40 downward-facing ledge one extrusion wide, hanging off the 0.50 core along
# its whole length -- the same class as every counterbore shoulder in this part, not a bridge.
SEP2_DRV_CLR  = 0.40            # the wall's own clearance to the driver BODY
# TWO bounds, and they are NOT the same bound even though today they give the same number.
# The groove is 0.60 deep and cut into the very face the wall's top bears on; the body is
# 0.40 further +X. They coincide only because SEP2_DRV_CLR == DRIVER_CLR right now, so take
# the min rather than the coincidence -- change either constant and they diverge.
SEP2_X1       = min(DRV_CX - (DRIVER_H + 2*DRIVER_CLR)/2,       # the locating groove's -X edge
                    DRV_CX - DRIVER_H/2 - SEP2_DRV_CLR)         # the driver body + clearance
SEP2_X0_THIN  = PROT_PKT_X0 + PROT_PKT_CLR + PROT_W             # 21.05, the strip at full drift
SEP2_X0_FULL  = RIM_X0                                          # 20.65
SEP2_T_THIN   = SEP2_X1 - SEP2_X0_THIN                          # 0.50
SEP2_T_FULL   = SEP2_X1 - SEP2_X0_FULL                          # 0.90
SEP2_Z_STEP   = PROT_PKT_Z1                                     # -26.20, the pocket's own top
SEP2_Y_PAD    = PROT_PKT_CLR                                    # the thinned band's Y overrun
#
# ⚠️ EXPERIMENTAL, AND IT IS THE THINNEST SOLID IN THE FAMILY.  NAMED, NOT SLIPPED IN.
# 0.50 is 1.25 extrusions at the 0.40 nozzle -- thinner than SIDE_LBL_SD_W's groove is wide, and
# that one is already flagged. The MITIGATION is the orientation: this wall stands VERTICAL on
# the bed, supported along its entire 44.80 bottom edge, so every layer is a straight 2-perimeter
# run. That is a strictly easier class than the HORIZONTAL 1.25 web JP validated on the r10 bench
# ("clean, webs crisp"), and a different class again from issue #47, whose collapsed 0.90 was an
# unsupported web spanning a bore. Under the floor is still under the floor, so it is exempt
# EXPLICITLY in check 8a with its own reason -- no other feature inherits the carve-out.
# COST OF FAILURE, stated: a floppy or absent wall. Nothing structural depends on it (the cell's
# lateral datum is the stub lane, the seal is the rim, the screws are elsewhere), and if it
# prints badly it comes out with scissors. What it buys is the whole -X separation.
assert SEP2_X0_FULL >= PROT_PKT_X1 - 1e-9, (
    f"the wall's -X face at {SEP2_X0_FULL:.2f} is inside the strip's straight-down insertion "
    f"column (x {PROT_PKT_X0:.2f}..{PROT_PKT_X1:.2f}). Everything in this bay loads from above; "
    f"a wall in that column means the strip cannot be fitted at all")
assert SEP2_T_THIN > 0 and SEP2_T_FULL > SEP2_T_THIN, (
    f"the separator lane collapsed: thin {SEP2_T_THIN:.2f}, full {SEP2_T_FULL:.2f}. The strip "
    f"({SEP2_X0_THIN:.2f}) and the groove ({SEP2_X1:.2f}) have met -- no wall fits between them")
assert SEP2_Z_STEP >= PROT_PKT_Z0 + PROT_T - 1e-9, (
    f"the step at z {SEP2_Z_STEP:.2f} is BELOW the seated strip's top ({PROT_PKT_Z0+PROT_T:.2f}) "
    f"-- the full section would come down on the body")
# CONTROL, anchored to the feature r11 actually tried: the 1.60 wall standing on RIM_X0 reached
# x 22.25, and it must still be REJECTED by the groove bound. If it ever passes, this lane has
# stopped being measured against the driver and the whole derivation above is decorative.
assert SEP_WALL_X1 > SEP2_X1 + 1e-9, (
    f"control failed: r11's {SEP_WALL_T:.2f} wall (+X face {SEP_WALL_X1:.2f}) now clears the "
    f"groove at {SEP2_X1:.2f}, so the bound that forced the step is not binding on anything")
# ...and the shift argument, as an assert rather than as a paragraph nobody re-runs.
assert (SEP2_X1 + _shift_hi) - SEP2_X0_THIN < MIN_SOLID, (
    f"a driver shift of {_shift_hi:.2f} now yields a "
    f"{(SEP2_X1+_shift_hi)-SEP2_X0_THIN:.2f} wall, which CLEARS MIN_SOLID -- so the step is no "
    f"longer necessary and this wall should be rebuilt full-section on a shifted driver")

# ---- THE HOLD-DOWN.  JP: "secured with the ... strip-securing features", not tape or hope. ----
#
# The ribs stop it sliding; nothing stopped it LIFTING, and the previous revision said so out
# loud ("no clip, reliance recorded") because a lid-clip over the PCB is a downward-facing
# ledge in the cover's print orientation -- the bridging class JP rejected the hooks for.
#
# The answer is already in this file, at the contact kerf: a DETENT, not a clip. A bump left
# standing on the rib faces at the PCB's top edge overhangs by its own PROT_DETENT and nothing
# else -- under one extrusion width, which is what makes the contact bar printable. The PCB
# deflects past 0.30 of interference going in and the same coming out, and 0.30 on a 2.50 board
# is a positive snap rather than a friction fit.
PROT_DETENT   = 0.30            # how far each bump overhangs the seated PCB
PROT_DET_H    = 2 * LH          # 0.40, the bump's height -- same as the contact bar's
# ---- NICKEL TAB SLOTS.  The tabs are the wiring, and they are FLAT. ----
#
# ⚠️ TOPOLOGY CORRECTION, because these strips are SOLD to be spot-welded to a cell under its
# wrap and that is emphatically not what happens here. THE STRIP IS FIXED IN THE CASE AND THE
# CELL STAYS BARE AND REMOVABLE. Nothing attaches to the cell. The chain is:
#
#     bay spring (-)  --tab-->  B-        P-  --.
#     + contact plate --tab-->  B+        P+  --'--> JST 1.25 2P pigtail --> BAT (CONN_L[0])
#
# The tabs are ~5mm x 0.15 flat conductors, so they run in SHALLOW SLOTS rather than round-wire
# channels, and the excess is trimmed. Solder access is the thing these pockets always forget:
# here the whole compartment is open from +Z until the midframe goes on, so every joint is
# reachable with an iron while the strip is seated. That is a property of the assembly order,
# and check 13b measures that nothing overhangs the pocket to spoil it.
TAB_W         = 5.40            # 5.00 tab plus clearance
TAB_D         = 2 * LH          # 0.40 deep: 0.15 of tab plus solder

# ============================================================================
# 5g. THE BAY'S METALWORK.  A CONTACT THAT FALLS OUT IS A DESIGN FAILURE.
# ============================================================================
#
# >>> JP, 2026-08-01: "we need features to hold the spring, and to hold the metal strips." <<<
# >>> AND LATER THE SAME DAY: "just PLA printed and the nickel strips."                    <<<
#
# The second sentence deleted the first one's subject. There is no spring to hold any more --
# the coil is gone (§3b) and what takes its place is a FOLD in the same nickel the contacts are
# made of. So the bay's metalwork is now exactly two pieces of 0.25 strip and they are RETAINED
# THE SAME WAY, by one construction used at both ends of the bay:
#
#     -Y end   the FOLDED LEAF  -- its root in a kerf, its fold projecting into the bay
#     +Y end   the FLAT PLATE   -- its whole body in a kerf, flush with the end wall
#
# ⚠️ ONE CONSTRUCTION, TWO ENDS, AND THAT IS THE POINT. The version this replaces had a
# d9.00 gabled tunnel for the coil and a kerf for the plate -- two unrelated retention schemes,
# two sets of constants, two ways to be wrong. A kerf with a detent bar does the whole job at
# both ends: it is the seat, the insertion throat and the tab's lane in one cut, its walls are
# vertical, it has no roof, and the bar left standing across the back of it is what stops the
# metal coming out the way it went in. The tunnel's over-travel stop is not lost either -- the
# end wall behind the leaf IS the stop, and it is a whole wall rather than an annular lip.
#
# THE ACCEPTANCE BEHAVIOUR IS STILL JP'S AND IT IS STILL SHARP: cell OUT, case held
# OPEN-SIDE-DOWN, the metal stays put. Check 8g asks it that way at BOTH ends now, with the
# escape direction and a control that must NOT collide.
#
# ---- WHY THE LEAF IS METAL AND NOT A PRINTED FLEXURE.  CREEP, NOT PRINTABILITY. ----
#
# A PLA cantilever pressing a cell against a contact is loaded CONSTANTLY for the life of the
# device, and PLA stress-relaxes under constant strain: a month later the deflection is still
# there and the force is not. This family's printed-in-place button hinges are the counter-
# example that proves the rule -- they flex for a fraction of a second and spend the rest of
# their lives unloaded, which is why they survive. A battery contact is the opposite duty
# cycle, so PLA does the GEOMETRY (datum, travel stop, retention) and nickel does the force.
#
# ---- AND THE FORCE IS JP-TUNABLE, WHICH THE POCKET HAS TO ALLOW FOR ----
#
# A hand-formed fold's rate is whatever his fingers and pliers produce. Nothing here can
# predict it, so the pocket is dimensioned to accept a RANGE of fold depths: the kerf fixes the
# root and the bay is open in front of it, so a deeper fold simply starts further +Y. What IS
# bounded is the geometry -- LEAF_FREE against the shortest cell for preload, LEAF_SOLID
# against the longest for closure -- and both are asserted in section 4b, on the constants, and
# again in check 5 on the built solid.
#
# ⚠️ CONTACT WIPE IS A FEATURE AND IS RECORDED AS ONE. The cell's flat can face slides across
# the fold's crown as it seats, which scrubs the oxide off both. A flat-to-flat plate contact
# does not do that, which is part of why the + end keeps its own detent pressure.
LEAF_SEAT_Y   = BAY_Y0          # the fold's back bears on the bay's -Y end wall
                                # (LEAF_W and LEAF_KERF alias the plate's, below)


# ---- THE "+" CONTACT.  A KERF, NOT A POCKET. ----
#
# CONTACT_T IS JP-CONFIRMED, THE KERF IS NOT. JP confirmed the MATERIAL: 0.25mm nickel strip,
# his words on the thickness only -- "I don't know the kerf". So the slot width is DERIVED here
# and owned here: CONTACT_T + CONTACT_PLAY, where the play is this design's FDM fit allowance
# and is the first constant to move if the printed slot binds or rattles. Neither number is
# calipered; if a fit issue ever appears, CONTACT_T is the second thing to measure.
CONTACT_T      = 0.25                       # JP-CONFIRMED DEFAULT (material), not calipered
CONTACT_PLAY   = 0.10                       # MINE: FDM fit allowance, tune this first
CONTACT_KERF   = CONTACT_T + CONTACT_PLAY               # 0.35
CONTACT_W      = 10.00                      # plate width in X -- was the old pocket's 10
CONTACT_H      = 10.00                      # plate height in Z
CONTACT_Z0     = CELL_AXIS_Z - CONTACT_H / 2            # -24.50, the kerf's floor
CONTACT_Z1     = CONTACT_Z0 + CONTACT_H                 # -14.50, the plate's top when seated
# ---- and the detent, because friction alone is not retention ----
#
# The kerf has to be OPEN AT THE TOP or the plate cannot be got in: it is 10mm square and
# nothing 10mm square passes a closed slot. Open at the top means it can also come back out, so
# a bar is left standing across the back of the slot just above the seated plate, filling
# CONTACT_DETENT of the kerf's 0.35. The plate has to deform past 0.05 of interference going in
# and the same coming out. Printability is free here: the bar's underside overhangs by the
# kerf's own 0.35 depth and nothing else, which is under one extrusion width.
CONTACT_DETENT = 0.15                       # how much of the kerf the bar fills
CONTACT_DET_H  = 2 * LH                     # 0.40, the bar's height
# ---- and the leaf's root uses the SAME kerf, because it is the same metal ----
LEAF_W    = CONTACT_W                       # 10.00
LEAF_KERF = CONTACT_KERF                    # 0.35
assert abs(LEAF_T - CONTACT_T) < 1e-9, (
    f"the leaf is {LEAF_T} stock and the plate is {CONTACT_T} -- they no longer share a kerf, "
    f"so LEAF_KERF has to stop being an alias and become its own derivation")


def leaf_phantom(height, dz=0.0):
    """The folded nickel leaf, as the envelope its fold sweeps, so the bay can be asked about it.

    Modelled as a plain box: a fold's exact profile is whatever JP's pliers produce and the
    questions asked of it are all envelope questions -- does it fit, is it captive, does the
    cell reach it. Its Z window is the PLATE's, because both are cut from the same strip into
    the same kerf and the cell's can face is what both have to meet.

    ⚠️ IT INCLUDES THE ROOT, AND THE FIRST VERSION DID NOT -- it started at LEAF_SEAT_Y, i.e.
    it modelled only the part of the leaf standing in the bay. The captivity test then lifted a
    phantom that was nowhere near the detent bar and read 0.00 mm3 of interference, which the
    gate correctly called a failure: THE THING THAT MAKES IT CAPTIVE IS THE PART THAT WAS
    MISSING FROM THE MODEL. A phantom that omits the retained feature cannot test retention.
    """
    return bx(CELL_AXIS_X - LEAF_W/2, CELL_AXIS_X + LEAF_W/2,
              LEAF_SEAT_Y - LEAF_KERF + 0.02, LEAF_SEAT_Y + height,
              CONTACT_Z0 + dz, CONTACT_Z1 + dz)

def plate_phantom():
    """The FLAT +Y contact plate, as its own phantom.  IT HAD NONE, AND A CHECK NEEDED IT.

    ⚠️ WHY THIS EXISTS: check 15 measures whether a polarity marking can be SEEN, and it ran
    that lens against `leaf_phantom()` alone -- the -Y metalwork. The "+" marking is on the
    OTHER end wall, 66mm away, so the lens was measuring the "+" mark against a piece of metal
    that is nowhere near it. That is the identical defect `leaf_phantom`'s own docstring records
    ("a phantom that omits the retained feature cannot test retention"), one end further along:
    a phantom that omits the +Y metalwork cannot test the +Y marking.

    The plate lies FLUSH IN ITS KERF -- body from CELL_TIP_Y to CELL_TIP_Y + CONTACT_KERF, i.e.
    entirely BEHIND the wall face the mark is cut into, projecting nothing into the bore. That
    is the whole reason the two markings are placed asymmetrically, and now it is MEASURED
    instead of asserted in a comment.
    """
    return bx(CELL_AXIS_X - CONTACT_W/2, CELL_AXIS_X + CONTACT_W/2,
              CELL_TIP_Y, CELL_TIP_Y + CONTACT_KERF,
              CONTACT_Z0, CONTACT_Z1)


def prot_phantom():
    """The 1S protection body, in its bay pocket, so its fit is measured and not asserted.

    All three dimensions are JP-calipered now, so this phantom is the real part rather than a
    class placeholder -- which is what makes the 0.39mm of cell clearance over it (§4c) a
    clearance and not a hope. Its 4.50 face lies against the cell; its 2.50 goes into the
    corner solid.
    """
    return bx(PROT_PKT_X0 + PROT_PKT_CLR, PROT_PKT_X0 + PROT_PKT_CLR + PROT_W,
              PROT_Y0, PROT_Y1,
              PROT_PKT_Z0, PROT_PKT_Z0 + PROT_T)

def tp4056_phantom():
    """The module that NO LONGER FITS. Kept so check 13 can prove that, not just claim it.

    Placed where the STRIP is, because that is the only free floor left: the lower band. Its
    17.00 short axis against a band of RIM_Y0-RIM_WALL - BAY_Y0 = 8.20 is the arithmetic, and
    the boolean is what says so.
    """
    _cx = (RIM_X0 + RIM_X1) / 2
    return bx(_cx - TP_W/2, _cx + TP_W/2, RIM_Y1 + RIM_WALL, RIM_Y1 + RIM_WALL + TP_L,
              CAV_Z0, CAV_Z0 + TP_H)
# ---- cell lead pass into the board cavity, landing on CONN_L[0] = BAT ----
#
# BAT is a 1.25mm JST 2P on the SAME LONG EDGE as UART -- docs/enclosure.md:160 ("...BAT (2P),
# UART (4P)") and :213 ("all four 1.25 mm JST positions"), which agrees with ember_case's
# CONN_L labelling. So the bay-to-board lead is a JST 1.25 2P pigtail leaving the cell's
# contacts, up through this pass, to CONN_L[0] on the x=0 edge. The cell lane is deliberately
# on that side: it is the shortest possible route.
# ⚠️ MOVED INBOARD 1.25 FOR THE -X DOVETAIL, 2026-08-01. It used to start at OX0 + COV_WALL -
# 0.40 = -1.15, i.e. 0.40 INSIDE the cover's wall footprint, for no stated reason -- the pass is
# a slot in the midframe's FLOOR and the pigtail leaves the bay well inboard of the wall. The
# dovetail groove needs u <= WALL of that wall unbroken over y 18.60..85.25, and at -1.15 this
# slot punched straight through it for 6.50mm of that run. Same width, same Y, shifted to clear
# the groove's inboard face (u = 2.60, x = -0.35) by 0.45. Check 8f measures the gap.
LEAD_X0, LEAD_X1 = 0.10, 3.75
LEAD_Y0, LEAD_Y1 = 20.00, 26.50

# ============================================================================
# 5b. CHARGING.  ONBOARD, AND THAT ANSWERS THE QUESTION THIS FILE ONCE ASKED.
# ============================================================================
#
# >>> THE BOARD CHARGES THE CELL ITSELF.  NO EXTRA HARDWARE IS REQUIRED. <<<
#
# docs/enclosure.md:165 (a verified-vs-inferred audited section): "Battery input is 3.7 V LiPo,
# charging at 290 mA actual / 500 mA max."  Corroborated independently, with the mechanism, by
# an earlier investigation -- scratch/hosyond-s3/battery.md, morpheus-battery 2026-07-30:
# "the board's TP4054 charges at a fixed 290 mA (R12 = 3.3 kOhm), there is no boost".
# 290 mA is attested twice; the TP4054/R12 detail is single-source, so it is cited as such.
#
# TWO CONSEQUENCES THAT ARE NOT ABOUT GEOMETRY BUT BELONG NEXT TO THE CELL:
#
#   1. NO PROTECTION CIRCUIT ON THE BOARD. ⚠️ THIS PARAGRAPH SAID "so a PROTECTED cell is
#      mandatory ... this case is 9.55mm longer than a bare-cell design would be" UNTIL
#      2026-08-01, WHICH CONTRADICTED SECTION 3 OF THIS SAME FILE. JP reversed to bare flat-tops
#      only ("no protected tops"), the bay was re-primaried to CELL_L_MAX = 65.50, and the case
#      got 5.90mm SHORTER rather than 9.55 longer. The electrical conclusion did not go away, it
#      MOVED: with bare cells the missing protection is carried by the 1S DW01 strip in section
#      5f, which is required equipment for exactly this reason. Two statements of the same fact,
#      and the stale one was still asserting the opposite design.
#   2. NO BOOST. On battery, +5 becomes the raw cell, and battery.md's finding is that the
#      device "browns out rather than shutting down". The strip's own cut-off is now what stops
#      the cell going to zero afterwards. Either way there is no graceful low-battery shutdown,
#      which is a firmware question and is flagged in the issue, not solved here.
#
# CHARGE TIME. Recomputed rather than inherited, using battery.md's own method so the two are
# comparable: it quotes 2000 mAh -> 9.3 h, i.e. C/I x 1.35 (6.90 h of CC plus a CV tail).
# Applying the same 1.35 to a 3400 mAh protected cell at 290 mA gives 11.72 x 1.35 = ~15.8 h.
# Overnight, and worth stating so nobody files it as a fault later.
CHARGE_MA        = 290.0        # docs/enclosure.md:165, "actual" (500 max)
CHARGE_CV_FACTOR = 1.35         # battery.md's implied CC/CV factor, reused for comparability
CELL_CAPACITY_MAH = 3400.0      # a typical protected 18650
# ---- negative-lead groove down the divider's cell-facing face ----
WGROOVE_D, WGROOVE_Z = 1.00, 27 * LH   # 5.40 deep in Z: widened from 3.20 so a FLAT 5mm nickel
                                       # tab lies in it instead of a round wire

# ============================================================================
# 5d. THE CELL-BAY FAILURE VENT.  A LABYRINTH FOLDED INSIDE A 2.20 WALL.
# ============================================================================
#
# A Li-ion cell in a sealed plastic box is the one thing in this design that can hurt someone,
# and "the compartment is not sealed to the board cavity" was too weak an answer. The bay now
# has a DELIBERATE path to outside air, and the enclosure is not the restriction:
#
#   ASSUMPTION, STATED BECAUSE IT SETS THE TARGET: an 18650's positive cap carries 3-4 vent
#   ports; taking 3 x d2.0mm gives ~9.42 mm2. That is general cell construction, not a
#   datasheet I hold -- if JP has real numbers, VENT_N is the knob.
#
# ⚠️ AND IT MUST NOT BE A HOLE. A straight slot through the wall is a light and dust path into
# the bay, and it is also the easy mistake to make while "adding a vent". So the path is folded
# INSIDE the 2.20 wall: cut VENT_D from the inside at one Y, VENT_D from the outside at a
# different Y, and let the two overlap in depth to leave a connecting band. Gas turns twice; a
# straight line finds 0.80mm of skin. Check 16 probes for exactly that, with a control that
# drills the wall through and proves the probe can see it.
#
#   band width = 2*VENT_D - COV_WALL = 0.60, which is SLOT_W -- this repo's proven void at a
#   0.4 nozzle with gap-closing set to 0 (PRINT-SHEET). Not a number picked for the vent.
#
# Every cut runs its long axis along model Z, which is the PRINT Z once the cover is on its bed
# face: these are vertical slots, self-supporting, with no bridge anywhere. That is why the vent
# is in a side wall and not the floor.
VENT_N     = 4
VENT_W     = 2.00       # slot width in Y
VENT_RIB   = 1.20       # material between a unit's inner and outer slot -- forces the turn
VENT_GAP   = 1.60       # material between units
VENT_PITCH = 2*VENT_W + VENT_RIB + VENT_GAP             # 6.80
# ⚠️ DERIVED FROM CELL_WALL_X, NOT COV_WALL, AND THAT DISTINCTION IS LOAD-BEARING NOW.
# These cuts are keyed to two different faces -- the inner slot to CELL_X0, the outer slot and
# the band to OX0 -- so they only meet if the arithmetic uses the wall they are ACTUALLY in.
# Against COV_WALL, with the -X wall thickened to CELL_WALL_X by the no-lip solve, the inner
# slot and the band would stop meeting by 0.20 and this becomes TWO BLIND POCKETS: the cell
# bay's only pressure-relief path, dead, and looking exactly like a working vent from outside.
# Hold the BAND at the proven SLOT_W void and let the skins take the extra wall.
VENT_BAND  = 0.60                                       # SLOT_W, the proven void -- held
VENT_D     = (CELL_WALL_X + VENT_BAND) / 2              # 2.139 from each face
VENT_SKIN  = CELL_WALL_X - VENT_D                       # 1.539 at each face, was 0.80
assert 2*VENT_D - CELL_WALL_X > 0.0 and abs((2*VENT_D - CELL_WALL_X) - VENT_BAND) < 1e-9, (
    f"the vent's two slots are {VENT_D:.3f} deep in a {CELL_WALL_X:.3f} wall and do not overlap "
    f"by the intended {VENT_BAND:.2f} -- it is two blind pockets, not a labyrinth")
VENT_Y0    = 30.00                                      # clear of every retention feature
CELL_PORTS_MM2 = 3 * math.pi * (2.0/2)**2               # 9.42, the assumption above

def _vent_units():
    """(inner slot y, outer slot y, band y) for each labyrinth unit."""
    out = []
    for i in range(VENT_N):
        iy0 = VENT_Y0 + i*VENT_PITCH
        oy0 = iy0 + VENT_W + VENT_RIB
        out.append(((iy0, iy0+VENT_W), (oy0, oy0+VENT_W), (iy0, oy0+VENT_W)))
    return out
VENT_Z0 = CELL_AXIS_Z + 1.00                            # -18.50, above the cradle's tangent
VENT_Z1 = BACK_Z - 1.80                                 # -11.50, below the mating plane
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
