jphein/ember.realm.watch/esphome/ember-satellite.yaml

########################################################################
# ember-satellite — LCDWIKI/QDtech ES3C28P (sold as "Hosyond 2.8in ESP32-S3")
#
# HA voice satellite for the Ember pipeline. The screen IS the hearth: one
# fire in a grate whose temperature is the whole state machine.
#
# Pinout is traced to the manufacturer's schematic (see
# scratch/hosyond-s3/nebula-prior-art.md + ES3C28P_official_schematic.pdf),
# NOT copied from community tables — several of those have the I2S data
# pins inverted because the silkscreen names them from the codec's side.
#
# Activation: TOUCH the screen (no wake word for now).
#
# ARCHITECTURE NOTE — why no LVGL:
#   The audio callback does maths ONLY (compute RMS, push to ring buffer).
#   The display redraws on its own interval and reads that buffer. This
#   deliberately decouples the I2S callback from SPI drawing, because mic
#   and speaker share one I2S hub on this board and blocking in the audio
#   path risks dropouts. A hand-drawn waveform is also far simpler and
#   lighter than bending LVGL widgets into a histogram (LVGL has no chart
#   widget in ESPHome 2026.7.2).
#
# ARCHITECTURE NOTE — BANDED PARTIAL REDRAW (added 2026-07-29):
#   The screen is divided into four fixed horizontal bands. At most ONE band
#   is repainted per frame, and mipi_spi flushes only the dirty bounding box,
#   so per-frame cost is proportional to the band, not the panel. This is what
#   buys a 20fps fire animation at LOWER main-loop duty than the previous
#   3.3fps full-frame repaint. Two hard requirements fall out of it:
#     - `auto_clear_enabled: false` (otherwise clear() dirties every pixel
#       before the lambda even runs — see the display block).
#     - Nothing may draw outside its own band. The framebuffer now PERSISTS
#       between frames, so a stray draw leaves permanent litter whose symptom
#       (ghosting) looks nothing like its cause.
#
# ARCHITECTURE NOTE — why the fire renders ROW-MAJOR:
#   The framebuffer is allocated by RAMAllocator, whose default flags are
#   ALLOC_INTERNAL|ALLOC_EXTERNAL == external FIRST (core/helpers.h:2185), so
#   153,600 bytes of it live in octal PSRAM. Display::filled_rectangle is
#   rows-of-horizontal_line over a per-pixel draw_pixel_at
#   (display.cpp:88-112 — whose own "Future:" comments flag this as the known
#   weak spot). A 4px-wide x 70px-tall flame column therefore touches ~70
#   separate PSRAM cache lines to write 8 useful bytes each. The fire is
#   instead emitted as horizontal RUNS, so every write is sequential in x with
#   rows ascending and each cache line is fully consumed.
#   >>> Do not "simplify" the fire back into per-column filled_rectangle
#       calls. It looks identical and costs several times more. <<<
########################################################################

substitutions:
  name: ember-satellite
  friendly_name: Ember Satellite

  # OTA credential, PER DEVICE. ember-mobile.yaml overrides this with its own
  # secret, and that separation is the whole point: with two boards from the same
  # batch on the same network, the expensive mistake is not an intruder, it is
  # pushing one board's firmware at the other. A device renamed by a mis-targeted
  # OTA answers to the wrong hostname and orphans 25 Home Assistant entities.
  # Distinct passwords make that fail at authentication instead of succeeding.
  #
  # Substitution rather than a bare `!secret` in the ota: block because !secret
  # cannot be given a computed key — the indirection is what lets each wrapper
  # choose its own. ESPHome tracks the provenance, so `esphome config` prints
  # `!secret 'ota_password_satellite'` and never the value.
  ota_password: !secret ota_password_satellite

  # ---- the cell (mobile variant only) ----
  # 0 here, 1 in ember-mobile.yaml. THE FIRST DEVICE-DIVERGENT DISPLAY FEATURE:
  # the desk unit has no cell — its GPIO9 reads an absent divider and the number
  # is noise — so everything battery flows through this gate and compiles OUT on
  # the desk build (the lambdas test a literal 0, which folds). Do not key any of
  # it off the measured voltage instead: noise on a floating pin can look like
  # any voltage you name, including a plausible one.
  #
  # Thresholds are PERCENT SOC (not volts) and live here so a bench build can
  # trip the ladder by editing two numbers, no code. Calibrated against the
  # observed 2026-08-06/07 discharge: 20% ≈ 3.50V rested — several hours of
  # warning before the ~3.4V regulator floor; 8% ≈ 3.40V — the last graceful
  # moment to say so out loud. That trace bottomed at 2.508V with nobody
  # watching, which is the event this whole ladder exists to make impossible.
  has_battery: "0"
  batt_low_pct: "20"    # candle gutters + chime_guttering, once per discharge
  batt_crit_pct: "8"    # HA-side: mobile speaks + ember_broadcast (desk/Slack)
  # Histogram width in samples; must match level_hist array size below.
  hist_len: "120"
  # dBFS window the level meter maps to 0-100%. THESE NEED CALIBRATING on
  # real hardware — too narrow and the meter pins, too wide and it looks dead.
  # Speak at normal volume ~40cm away and watch sensor.mic_rms, then set
  # db_floor just under the room-noise reading and db_ceil just over speech.
  db_floor: "-72.0"
  db_ceil: "-30.0"

  # ---- speaking-phase animation ----
  # The flame wave advances one full spatial cycle per this many ms of REAL
  # audio (frames clocked to the DAC), not per this much wall time.
  flame_cycle_ms: "900"
  # Fuse denominator: est_ms = tts_lead_ms + chars * tts_ms_per_char.
  # 62 ms/char ~= 16 chars/s, about right for en-GB Piper/Azure. CALIBRATE:
  # watch the "spoken x.xs / ~y.ys" line in the telemetry band and adjust until
  # the fuse lands near the right-hand edge as Ember stops talking.
  tts_lead_ms: "400"
  tts_ms_per_char: "62"
  # If the frame counter doesn't advance for this long while the speaker still
  # reports is_running(), the fire gutters and the telemetry band says so.
  stall_ms: "300"

  # Chime on THINKING. 0 = off (default), 1 = on. See the chime script for why this
  # is a switch and why `listening` deliberately isn't one.
  chime_on_thinking: "0"

  # ---- wake word mode ----
  #   0 = off. Touch-only. The shipped behaviour.
  #   1 = ON-DEVICE, microWakeWord "Okay Nabu" (stock model, vendored in wakewords/).
  #   2 = SERVER-SIDE, HA openWakeWord "don-kee".
  #
  # DEFAULTS TO 1, and that is a change of behaviour on the next flash: Ember will
  # start answering to "Okay Nabu" without being touched. Everything wake-word related
  # is inert at 0, and modes 1 and 2 are mutually exclusive by construction (every
  # guard tests for one specific mode, never "non-zero").
  #
  # WHY 1 AND NOT 0, given the #42 precedent shipped its wake word off: what justified
  # off there was the privacy cost of streaming room audio to HA, and mode 1 does not
  # have that cost. Nothing leaves the device until the word fires. The remaining risk
  # is the I2S one below, which is a bench-observable audio bug, not a data question —
  # and it is observed in the first ten seconds of a flash that JP is present for.
  #
  # ✅ FLASHED AND HEARD. This block read "⚠️ NEVER FLASHED" until 2026-08-03; JP
  # confirmed "Okay Nabu" works on the desk unit, and the same mode came up clean on
  # ember-mobile's first flash (wake word -> STREAMING_MICROPHONE -> STT, no bus
  # errors in the log). The I2S arbiter below yields the bus correctly. The risk the
  # old banner described was real when written and is now retired by observation.
  #
  # Kept as the rollback recipe, because the failure mode is still worth recognising:
  # if a board ever goes silent — no chimes, no replies, and the log repeats "Parent
  # bus is busy" or "Driver failed to start; retrying in 1 second" — the arbiter is
  # not yielding. Set this back to 0 and reflash; that restores touch-only exactly.
  #
  # ⚠️ WHAT A FRESH FLASH *DOES* DO, and it looks like a fault: a board that is on
  # WiFi but NOT YET ADOPTED IN HOME ASSISTANT sits in a ~1 Hz loop —
  #   micro_wake_word: Stopping / Starting
  #   [E][voice_assistant]: No API client connected
  #   [W]: sound_level.sensor ... Microphone isn't running
  # because the re-arm triggers fire on voice_assistant *ending* and a failed start
  # counts as an end. Nothing is wrong with the board or the bus. It stops the
  # instant HA adopts the device. Observed on ember-mobile's bring-up 2026-08-03 —
  # do not go hunting the arbiter for it.
  #
  # MODE 1 vs MODE 2, honestly:
  #
  #   Mode 2 streams 16 kHz room audio to Home Assistant continuously while idle.
  #   That is a privacy and airtime cost, and it is why mode 2 has never been
  #   switched on. Mode 1 has no such cost — detection is local and nothing leaves
  #   the device until the wake word actually fires. Mode 1 is strictly better on
  #   that axis, and it is the reason it exists.
  #
  #   The catch is the wake WORD, not the wiring: mode 1 answers to "Okay Nabu",
  #   because the only "don-kee" artifact left is an openWakeWord model and that
  #   format cannot run on-device (input [1,16,96] float32 — openWakeWord's
  #   classifier head; microWakeWord is int8 and self-contained, and ESPHome
  #   implements only the latter). They are not interconvertible; "don-kee"
  #   on-device needs RETRAINING. See docs/wake-word.md.
  #
  # ⚠️⚠️ MODE 1 IS NOT FREE ON THIS BOARD, and the reason is the shared I2S bus.
  # micro_wake_word holds the MICROPHONE open continuously, and on this device the
  # mic and the speaker are the same `i2s_bus` behind ONE mutex. The mic takes that
  # mutex in start_driver_() and does not give it back until stop_driver_()
  # (i2s_audio_microphone.cpp:98,228), and the SPEAKER also acquires it with a
  # non-blocking try_lock() that just gives up — "Parent bus is busy"
  # (i2s_audio_speaker_standard.cpp:400) — and retries a second later, forever.
  #
  # So a naively-always-on micro_wake_word makes Ember MUTE: every reply, chime and
  # announcement fails to get the bus for as long as the wake word is listening.
  # This is the exact mirror of the `timeout: never` trap documented on the speaker
  # below, which warns that a permanently-loaded SPEAKER starves the mic. Same
  # mutex, other direction, and it is just as silent.
  #
  # What makes mode 1 safe is the arbiter in `interval:` (search "WAKE-WORD
  # ARBITER"), which yields the microphone the instant anything wants to make
  # noise. Do not "simplify" micro_wake_word into always-on. It will look fine on
  # the bench until the first time Ember tries to speak.
  wake_word_mode: "1"

  # How long the touch spark takes to settle, ms. Long enough to read as a flare
  # rather than a flicker; short enough that it is gone before the pipeline answers.
  spark_ms_len: "500"

  # How long the amp is held in shutdown across a shared-I2S clock start, ms.
  #
  # ENABLED, on evidence. I had set this to 0 believing amp blanking caused a silent-TTS
  # regression. It did not: with blanking off JP reported "the pop was still there and it
  # didn't speak" — so the pop RETURNED the moment blanking stopped, and the silence was
  # concurrent but unrelated (an HA-side stale TTS stream subscription,
  # `ERROR tts: Invalid subscription`, from repeated OTAs; fixed by reloading the ESPHome
  # config entry). Correlation, not causation, and I had it backwards.
  #
  # So amp blanking does the one job REG31 provably cannot: suppress the MCLK cold-start
  # transient. Confirmed independently by nebula's prior-art review — vendor firmware
  # (Espressif Korvo BSP, xiaozhi) creates DUPLEX channels once and never calls
  # i2s_channel_disable, so the clock never stops. ESPHome is simplex behind one shared
  # mutex and calls i2s_del_channel() on every hand-off, so every mic/speaker transition
  # destroys and recreates the clock. That is the architectural root cause.
  #
  # >>> CORRECTED. An earlier version of this comment said "the amp finishes waking
  # before the blank lifts", which is impossible and led to a wrong latency estimate.
  # GPIO1 is `inverted: true` on an ACTIVE-LOW SHUTDOWN, so `output.turn_off:
  # amp_enable` genuinely DISABLES the amp. A disabled amp is not waking — its ~100ms
  # typical wake (TD) begins only when the watchdog RE-ENABLES it at T+180ms.
  #
  # So the real timeline is: amp off at T+0, re-enabled at T+180, usably awake at
  # ~T+280. Any audio inside that window is silenced or clipped, not protected. That
  # is why 180 is right for the MICROPHONE path (no audio is expected during it) and
  # why blanking is fundamentally incompatible with a short touch tone — see the
  # haptic exemption in ui_dispatch. 0 disables blanking entirely.
  #
  # ⚠️ OPEN, and only a listening test can settle it: the amp datasheet warns a large
  # input coupling cap increases pop and recommends 0.1-0.39uF. This board is reported at
  # 0.39uF (C44/C45) — the very top of that range — so PA gating may TRADE a codec pop
  # for an amp-enable pop rather than remove it. That value came from extracted schematic
  # text and pdftotext adjacency has misled us on this board before, so it is
  # unconfirmed. Compare 0 / 180 / 300 by ear before trusting any of it.
  amp_blank_ms: "180"

  # ---- text layout ----
  # cpl_body / cpl_sm are GONE. They were character budgets estimated from Roboto's
  # average advance, and they were the cause of the truncation JP reported: an average
  # advance under-counts any line with wide glyphs, so lines overran the band and were
  # clipped. Wrapping is now measured with it.get_text_bounds(), so there is no
  # estimate left to be wrong.
  said_lines: "4"              # visible lines of Ember's reply per page
  scroll_page_ms_len: "3500"   # how long each page is held before advancing

  # ---- the hearth-wyrm ----
  # Placement of the creature inside the flame band. Up here rather than buried
  # in a 400-line lambda for the same reason the ui_ block below is: these are
  # the numbers someone will actually want to nudge.
  #
  # NOTE dgn_y is relative to the TOP OF THE FLAME BAND (FLAM_Y), not the panel.
  # The whole point is that the wyrm cannot be moved out of its band by editing
  # this: the renderer clips every span to 0..dgn_h and the band owns rows
  # FLAM_Y..FLAM_Y+FLAM_H-1 regardless.
  dgn_x: "60"           # wyrm bbox, screen x
  dgn_y: "22"           # wyrm bbox, offset from the TOP OF THE FLAME BAND
  dgn_w: "120"
  dgn_h: "50"

  # ---- overlay geometry ----
  # SHARED between the display lambda (which draws the targets) and the
  # touchscreen hit-test (which must land on them). Defined once here because a
  # silent drift between "where it's drawn" and "where it's tappable" is the
  # classic touch-UI bug and it is invisible in review.
  ui_oy: "32"           # overlay origin y — must equal SCRL_Y
  # The single-press overlay: FOUR rows since 2026-08-09 evening (volume /
  # mic gain / brightness / reading font — JP: "font size should be
  # configurable in the volume menu too"). Four 46px control lines do not fit
  # in the overlay's 232px, so each row is an 18px label line over a 38px
  # drawn control line at a 56px pitch — and the HIT band is the full 56px
  # pitch, label included (see the mode-1 hit-test: by-18 .. by+bh). 56px
  # ~= 10.3mm, the same touch floor every menu row uses; the drawn box is a
  # picture inside a larger target, never smaller. Rows end y258 of 263.
  ui_vol_by: "52"       # volume +/- : top edge of the drawn boxes
  ui_vol_bh: "38"       # +/- drawn-box height, shared by all four controls
  ui_gain_by: "108"     # mic gain +/- : top edge
  ui_bri_by: "164"      # backlight brightness +/- : top edge
  ui_font_by: "220"     # reading-font size +/- : top edge
  # 2026-08-24: FIVE rows (Douse joined — JP: "an off option"), and five 46px
  # rows do not fit the 232px overlay. 41px rows at iy 58: 58 + 5*41 - 3 = 260
  # of 263 — the static_assert at the overlay background is the enforcement.
  # 41px ~= 7.6mm, under the 8.4mm floor the 46px rows carried, and the same
  # trade the audio overlay made for its fourth row: rows are contiguous
  # (edge-to-edge bands, no dead gaps), so a near miss lands on a neighbour
  # row's meat rather than on nothing — and the destructive rows still need a
  # deliberate second act (Douse and Rekindle sit at the bottom, cursor-last).
  ui_pm_iy: "58"        # power menu: first item top edge
  ui_pm_ih: "41"        # power menu: item height (41px ~= 7.6mm — see above)
  ui_pm_n: "5"          # power menu: item count
  # Auto-dismiss after this long without interaction.
  ui_vol_timeout: "8000"   # was 5000; two controls take longer to set
  ui_pm_timeout: "12000"
  vision_timeout: "120000" # the Slack image lingers 2 min, then the fire returns
  # Where the hearths fetch stashed visions from. The edge name, not a LAN IP:
  # the IDF cert bundle validates it, and the IP-moved-once lesson applies.
  ha_base: "https://ha.jphe.in:8123"
  # The horn — the intercom button (2026-08-05). Bottom-right block of the
  # telemetry band: 47px wide (~8.7mm) by the band's full 56px (~10.3mm). Shared
  # by the on_touch hit-test and the display lambda for the same reason as every
  # other pair in this block: drawn and tappable must not drift apart. ui_ic_y
  # must equal TELE_Y in the band geometry.
  # 2026-08-09: x 192 -> 172. JP's bench verdict: "hard to tap in the corner
  # there." The block was already 47px (~8.7mm) — above the 8.4mm floor — so
  # size was never the problem; the CORNER was. The case bezel overhangs the
  # glass edge, so the outer ~2mm of any edge-flush target is under plastic a
  # fingertip cannot reach. The fix is REACH, not size: extend the active block
  # inward to 68px (~12.6mm) so the tappable meat sits clear of the lip. Same
  # substitution drives drawing and hit-test, so both move together.
  ui_ic_x: "172"
  ui_ic_y: "264"

  # Compile-time identity for the face (2026-08-09, JP: each ember shows its
  # lexicon name "plus the sigil version so i know it's teh latest"). Injected
  # per build:  esphome compile ember-mobile.yaml -s sigil_version $(git
  # rev-parse --short HEAD)  — the default below is what a build that FORGOT
  # the flag shows, and it is deliberately loud about being nobody: a face
  # reading "unsigiled" tells JP the build is untraceable, where a stale hash
  # would tell him a lie with confidence (verification.md §32's whole genre).
  sigil_version: "unsigiled"

  # This device's own assist_satellite entity in HA — what the chronicle's
  # SPEAK button hands to script.ember_announce so a replay comes out of THIS
  # hearth. A substitution because the entity id is the device name with
  # underscores, and ESPHome substitutions cannot transform strings; each
  # wrapper states its own. (ember-mobile.yaml overrides this.)
  satellite_entity: assist_satellite.ember_satellite_assist_satellite

esphome:
  name: ${name}
  friendly_name: ${friendly_name}
  min_version: 2025.11.0
  name_add_mac_suffix: false
  on_boot:
    - priority: 600
      then:
        - light.turn_on:
            id: backlight
            brightness: 80%

    # Register the ONE thing this design takes from the speaker: a frame counter.
    #
    # !! THIS CALLBACK RUNS IN speaker_task, NOT THE MAIN LOOP. !!
    #    i2s_audio_speaker.cpp:239 invokes audio_output_callback_ from
    #    run_speaker_task(); i2s_audio_speaker.h:22-23 give TASK_STACK_SIZE 4096
    #    and TASK_PRIORITY 19. That is the SAME hazard class as the
    #    `microphone: on_data:` block warned about below — so the body here is
    #    deliberately ONE 32-bit add and nothing else. No floats, no ESP_LOG, no
    #    std:: containers, no allocation. DO NOT GROW IT.
    #
    # Cross-task safety, chosen deliberately rather than assumed:
    #   spk_frames is `volatile uint32_t`. An aligned 32-bit load/store on
    #   Xtensa LX7 is a single instruction and cannot tear, so no lock is
    #   needed; `volatile` is what stops the compiler caching the value across
    #   the display lambda's reads. The counter is monotonic and is only ever
    #   used for elapsed-time subtraction, so reading a value one callback stale
    #   is visually irrelevant. Strictly cheaper AND safer than a mutex.
    - priority: -100
      then:
        - lambda: |-
            id(spk)->add_audio_output_callback([](uint32_t frames, int64_t ts) {
              (void) ts;
              id(spk_frames) += frames;
            });

    # Put the DAC where HA thinks it is. This fixes a PRE-EXISTING desync that has
    # nothing to do with announce: TemplateNumber::setup() only calls
    # publish_state() and never control() (template/number/template_number.cpp:8-25),
    # so `set_action` — and therefore audio_dac.set_volume — NEVER RAN AT BOOT. The
    # es8311 sat at its own 0.75 (= 0dB) default while HA displayed 45%, which is
    # exactly the "too loud" symptom noted on the number below.
    #
    # Driving it through media_player.volume_set (rather than number.set) settles
    # all three at once: speaker->set_volume() writes the DAC, and on_volume mirrors
    # the value back into spk_volume so the number and the media_player entity agree
    # too. Priority -200 so it lands after every component has finished setup().
    # MIC PGA RESYNC — ITS OWN TRIGGER, DELIBERATELY, AND THE REASON IS A DIAGNOSIS.
    #
    # This was first appended to the -200 sequence below and produced NO log line on the
    # device across three flashes, guarded and unguarded. The generated code was present
    # (main.cpp:8128), the logger was at DEBUG with no tag filter, and the boot log was
    # captured with a client already attached across a reboot. So the code existed, the
    # level permitted it, and it still did not appear — which points at the SEQUENCE rather
    # than at the action: an on_boot `then:` is an ordered list, and anything earlier in it
    # that blocks or fails takes everything after it down silently.
    #
    # Rather than keep testing hypotheses about which earlier action that might be — four
    # wrong ones earlier today came from exactly that habit — this gets its own trigger,
    # where no other action can precede it. It is also strictly better design: a resync
    # that only matters to one component should not be the tail of a list about the DAC.
    #
    # -300 so it lands after the -200 block regardless of what that block does.
    - priority: -300
      then:
        - number.set:
            id: mic_gain_num
            value: !lambda 'return id(mic_gain_num).state;'
        # ---- PROVE IT, at a moment the proof can actually be observed ----
        #
        # Four flashes were spent watching for a boot-time log line that never appeared,
        # concluding each time that the code had not run. That inference was unfounded:
        # `esphome logs` subscribes over the API SECONDS after the device boots, so a line
        # emitted during setup has nowhere to go. ABSENCE OF A LOG IS NOT ABSENCE OF
        # EXECUTION unless you can show the transport was live when it was emitted — and
        # that was never established. The generated code was in main.cpp the whole time.
        #
        # So this stops testing the messenger and tests the thing: wait until a client is
        # certainly attached, then READ REG16 BACK OFF THE CODEC and print it beside the
        # number's state. Agreement proves the resync reached the hardware; disagreement
        # names the bug precisely. Either way it is a measurement rather than an inference
        # from silence.
        - delay: 25s
        - script.execute: mic_sync_check

    - priority: -200
      then:
        - media_player.volume_set:
            id: media_out
            volume: !lambda 'return id(spk_volume).state / 100.0f;'
        # Mute the DAC before anything can start I2S. The `dac_muted` global already
        # says true, but the CODEC has to agree — otherwise the very first audio
        # after boot still pops, since there is no previous stop to inherit a mute
        # from. Must run after the es8311 is set up, hence the late priority.
        - audio_dac.mute_on: es8311_dac

        # AND PUT THE MIC PGA WHERE HA THINKS IT IS, for the identical reason spelled out
        # above — which is the uncomfortable part of this fix.
        #
        # THE BUG WAS ALREADY DOCUMENTED IN THIS FILE, 700 LINES UP, WITH THE LINE NUMBERS.
        # TemplateNumber::setup() calls publish_state() and never control(), so a restored
        # value never runs its `set_action`. That was found, fixed and written up for
        # spk_volume — and then a second restoring number was added and shipped with the
        # same defect, because the fix had been applied to an INSTANCE rather than turned
        # into a rule. A note saying "this component behaves like X" does not protect the
        # next component that behaves like X.
        #
        # The mic case fails more quietly than the volume one did. The es8311 driver writes
        # REG16 in its own setup() from the compile-time `mic_gain: 36db` still on the
        # audio_dac, so after a reboot the number reads whatever was stored while the PGA
        # sits at 36dB. Set 12dB, reboot, and HA shows 12 while the hardware is at 36 —
        # ⚠️ and the ONLY value immune is the default, which is exactly what anyone would
        # test with. Found by a reviewer reading the component source, not by running it.
        #
        # Pushed back THROUGH the number rather than writing REG16 here, so the register
        # keeps a single writer. Two places writing one register is how the amp ended up
        # with three writers and one of them reachable.

        # ---- REPUBLISH THE MODE, or the select lies after a reboot ----
        #
        # FOUND ON HARDWARE, NOT IN REVIEW, and the compiler and the config check both
        # passed with it broken. `op_mode` is `restore_value: true` because the mode is a
        # preference; `sel_mode` is a VIEW with `restore_value: false` and
        # `initial_option: "Normal"`. Nothing re-synced the view at boot, so a device
        # rebooted while quiet came back with:
        #
        #     op_mode      == 2      (genuinely Hush: speech and chimes suppressed)
        #     switch Hush  == ON     (a lambda over op_mode, so it stayed truthful)
        #     select Mode  == Normal (WRONG -- reverted to initial_option)
        #
        # Measured exactly that on the device: set Hush, restart, re-read. The two
        # entities disagreed and the SELECT was the wrong one -- which is the dangerous
        # way round, because the select is the surface a person reads and the entity an
        # automation would consult to decide whether Ember may speak.
        #
        # The design claimed the view "cannot disagree with the mode". That was true of
        # the Hush switch and FALSE of the select, and the gap is exactly one power
        # cycle wide -- invisible to a compile, to `esphome config`, and to any check
        # that never rebooted the device in a non-default mode.
        #
        # set_index re-runs the select's own set_action, which writes op_mode back to the
        # value it already holds. Idempotent by construction, so this cannot itself
        # become a second source of truth.
        - lambda: |-
            // A corrupt restored byte must not wedge the device in an undrawn mode.
            if (id(op_mode) > 2) id(op_mode) = 0;
            id(sel_mode)->make_call().set_index((size_t) id(op_mode)).perform();

interval:
  # Cheap: one I2C register read a minute on a control-plane bus. Periodic rather than
  # boot-only because a divergence introduced later — by anything that writes REG16
  # without going through the number — would otherwise never surface.
  - interval: 60s
    then:
      - script.execute: mic_sync_check

  # ---- THE WAKE-WORD ARBITER ----
  #
  # The one thing that makes on-device wake word survivable on this board. Read the
  # ⚠️⚠️ note in the substitutions block before touching it.
  #
  # THE PROBLEM IN ONE LINE: micro_wake_word holds the MICROPHONE open forever, and on
  # this device the mic and the speaker are one `i2s_bus` behind ONE mutex.
  #
  #   mic  takes it in start_driver_() and returns it only in stop_driver_()
  #        (i2s_audio_microphone.cpp:98, 228) — i.e. for its whole running life
  #   spk  asks with a NON-BLOCKING try_lock(), logs "Parent bus is busy" and gives up
  #        (i2s_audio_speaker_standard.cpp:400), then retries a second later. Forever.
  #
  # So an always-listening wake word does not degrade Ember, it MUTES it: every reply,
  # chime and announcement loses the bus for as long as the wake word is armed. This is
  # the same trap as `timeout: never` on the speaker documented above — that one starves
  # the mic, this one starves the speaker. One mutex, two directions, both silent.
  #
  # THE RULE: the wake word may hold the microphone only while nothing wants to speak
  # and no conversation is running. This loop is the sole owner of that rule, and the
  # sole caller of mww start/stop besides stop_after_detection.
  #
  # WHY is_stopped() AND NOT is_running(): is_running() is `state_ == STATE_RUNNING`,
  # which is only reached AFTER the speaker has won the lock — which it cannot do while
  # we hold it. Keying on it would deadlock: we would wait for a state that our own
  # holding the mic prevents. is_stopped() is `state_ == STATE_STOPPED`, so it goes
  # false at STATE_STARTING — the moment the speaker WANTS the bus, before it asks.
  # That is the only edge available to us, and it is why this reads inverted.
  #
  # 100ms is deliberate. This is a backstop, not the fast path: the two paths that
  # actually matter for latency yield the mic ahead of time (ui_dispatch for touch,
  # on_announcement for pushed audio) so the speaker wins its FIRST try_lock instead of
  # eating the 1s retry. This loop catches everything else and re-arms afterwards.
  #
  # FAILURE DIRECTION, chosen the same way the DAC-mute manager chose its: a missed
  # STOP costs a mute, a missed START costs deafness until the next tick. So the stop
  # side is also driven from the two predictive anchors, while the start side lives
  # only here — the worst case for arming late is 100ms of not listening.
  - interval: 100ms
    then:
      - lambda: |-
          if (${wake_word_mode} != 1) return;      // compile-time constant; folds away
          const bool want = id(spk)->is_stopped() && !id(va)->is_running();
          if (want && !id(mww)->is_running()) {
            id(mww)->start();
          } else if (!want && id(mww)->is_running()) {
            id(mww)->stop();
          }

  # THE UNMUTE ANCHOR. This condition — "we believe we are muted AND the speaker is
  # actually running" — was written as a 250ms watchdog behind on_announcement /
  # on_play. It is in fact the only correctly-timed anchor available, so it has been
  # promoted to the primary mechanism and the period tightened to 10ms.
  #
  # WHY THE MEDIA_PLAYER TRIGGERS WERE THE WRONG ANCHOR:
  #   on_announcement / on_play fire when the media_player enters its playing state,
  #   which is BEFORE the pipeline starts the speaker and therefore before
  #   i2s_channel_enable(). Unmuting there unmutes ahead of the clock transient, so
  #   the pop survives — the fix would appear to do nothing. is_running() is the only
  #   signal that means "the clocks are already up".
  #
  # WHY 10ms AND NOT 250ms — the free 50ms window:
  #   The speaker preloads DMA_BUFFERS_COUNT (5) buffers of memset-zero SILENCE and
  #   only THEN calls i2s_channel_enable()
  #   (i2s_audio_speaker_standard.cpp:121-166, DMA_BUFFER_DURATION_MS = 10).
  #   Every playback therefore opens with 5 x 10ms = 50ms of digital silence, and the
  #   clock transient lands inside it. Separately the frame callback fires only for
  #   `real_frames > 0` (:231), so spk_frames does not advance during that silence.
  #   Unmuting inside the window costs ZERO audio. At 250ms the unmute would land
  #   ~200ms INTO real speech — audible as a clipped start, and mid-signal, so the
  #   unmute itself would click. At 10ms it lands in the silence.
  #
  # is_running() flips in the speaker's own loop() (i2s_audio_speaker.cpp:69), the
  # same main loop as this interval, so detection is typically 10-20ms after the
  # enable. The one thing that could push it past 50ms is a long main-loop block —
  # a full display repaint is up to 60ms. If a faint tick ever survives at the very
  # start of audio, that is the cause, and the lever is main-loop time, not this
  # period.
  #
  # THE FAILURE DIRECTION IS PRESERVED, and it is why this is safe to ship: the
  # condition is re-evaluated against live hardware every 10ms, so a stuck mute
  # cannot persist — the moment audio runs, this unmutes. The worst case remains the
  # pop coming back, never silence.
  - interval: 10ms
    then:
      # ================= THE SILENCE GATE =================
      # A mode that must not speak is enforced by DECLINING TO LIFT the protection
      # that already runs between every utterance — not by interjecting in the audio
      # pipeline. That is the whole design, and it is chosen on this file's own
      # evidence: every previous attempt to insert something into the single
      # announcement pipeline broke speech (the `done` chime on on_end clobbered the
      # reply's FLAC decoder; `enqueue: false` destroys the in-flight item BY DESIGN;
      # the touch tone wedged the shared I2S lock).
      #
      # It is also the ONLY approach where nothing else has to be re-verified. The
      # media_player still fetches and plays, the I2S driver still loads,
      # on_tts_start/on_end still fire on schedule, chime_until and tts_est_ms stay
      # correct, and the display's promotion to SPEAKING plus the paging timer are
      # untouched. The requirement is "everything else including displaying what it
      # says", and this is the approach that changes nothing else BY CONSTRUCTION
      # rather than by inspection.
      #
      # THE PREDICATE IS THE DISPLAY'S OWN. `spk->is_running() && !chiming` is
      # character-for-character what the display lambda uses to promote to SPEAKING,
      # so the thing silenced is EXACTLY the thing the screen calls speech — one
      # definition, no second source of truth. It is also what separates speech from
      # chimes, which share this speaker: chime_until already means "the audio now
      # playing is not speech", which is precisely the distinction mode 1 needs.
      #
      # va_state is deliberately NOT consulted: it reads 0 for the entire duration of
      # a spoken reply. This asks the hardware, like the chime guard does.
      #
      # FAILURE DIRECTION IS PRESERVED AND INVERTS SAFELY. Re-derived from live
      # hardware every 10ms, so nothing sticks. Wrongly true => silence, which in
      # these modes is the INTENT. Wrongly false => a brief leak. Moving back to
      # Normal mid-reply un-mutes within one tick and the reply continues audibly.
      #
      # COSTS, STATED RATHER THAN HIDDEN: a driver load/unload still happens per
      # reply, and a little power is spent decoding audio nobody hears. Both are
      # cheap, and both buy the "nothing else changes" property above.
      - lambda: |-
          // ---- ONE QUESTION: AM I PERMITTED TO MAKE SOUND RIGHT NOW? ----
          //
          // Two independent things can forbid it, and they are folded into a single
          // predicate rather than checked in separate places:
          //
          //   the MODE   forbids SPEECH (not chimes) at op_mode >= 1
          //   amp_switch forbids EVERYTHING, unconditionally — it is the user's master
          //
          // Making the switch an INPUT to this question rather than a competing writer
          // to the pin is what fixes the old bug: it used to be `platform: output` over
          // amp_enable, so it wrote the GPIO directly and the watchdog's enable branch
          // overrode it on the next playback. Now there is one writer and one question.
          //
          // >>> The switch therefore genuinely SILENCES rather than recording a desire,
          //     and it does so with BOTH layers: the amp is disabled (see `want` below)
          //     AND the DAC is held muted for the duration of any playback. Belt and
          //     braces, because the amp is the half nothing in ESPHome can clear and
          //     REG31 is the half that survives Amp Blank Width = 0. <<<
          const bool chiming = (int32_t) (id(chime_until) - millis()) > 0;
          const bool is_speech = id(spk)->is_running() && !chiming;
          // The second clause covers a case that is UNREACHABLE TODAY and is here for
          // exactly that reason. In Hush the `chime` wrapper returns before playing, so
          // no chime audio ever starts and the gate never sees one — but the gate would
          // have classified it as not-speech and PERMITTED it. Any future sound path
          // that bypasses the wrapper (a raw play_on_device_media_file somewhere else)
          // would therefore leak in the mode whose whole promise is silence.
          //
          // Same doctrine as the mute inversion and the chime guard asking
          // spk->is_running(): cover call sites that do not exist yet, rather than the
          // ones we happen to have thought of. Costs one clause and makes Hush silent
          // at the hardware rather than silent by the convention that everything goes
          // through one script.
          const bool permitted = id(amp_switch).state &&
                                 !(is_speech && id(op_mode) >= 1) &&
                                 !(chiming   && id(op_mode) >= 2);
          id(snd_block) = id(spk)->is_running() && !permitted;
      - if:
          condition:
            lambda: 'return id(dac_muted) && id(spk)->is_running() && !id(snd_block);'
          then:
            - script.execute: dac_unmute

      # ⚠️ RE-ASSERTED ON A CADENCE, AND NOT GATED ON OUR OWN BOOKKEEPING.
      #
      # `!id(dac_muted)` would be the obvious guard and it is exactly wrong, because
      # the things that clear REG31 behind our back do not update `dac_muted`.
      # Verified against the ESPHome source:
      #
      #   I2SAudioSpeakerBase::set_volume() calls audio_dac_->set_mute_off() for any
      #   volume > 0, and SpeakerMediaPlayer::set_volume_ calls that AND
      #   set_mute_state_(false). So ANY HA media_player.volume_set / volume_up /
      #   volume_down / unmute clears the mute TWICE OVER, mid-playback, while
      #   `dac_muted` still says true.
      #
      # A guard on our own flag would therefore be silently bypassed — the precise bug
      # shape this file keeps paying for: correct-looking state, wrong hardware. So the
      # gate re-states itself to the hardware every 250ms while closed, which bounds
      # any unenumerated clearer to a quarter second instead of to forever.
      #
      # (The device's OWN volume path is safe — number.spk_volume ->
      # audio_dac.set_volume writes REG32 only. It is the HA media_player surface that
      # is not, which is why on_volume also re-asserts.)
      - if:
          condition:
            lambda: |-
              return id(snd_block) &&
                     (id(gate_ms) == 0 || millis() - id(gate_ms) >= 250u);
          then:
            - audio_dac.mute_on: es8311_dac
            - lambda: |-
                id(dac_muted) = true;
                id(remute_at) = 0;
                id(gate_ms) = millis();
                if (id(gate_ms) == 0) id(gate_ms) = 1;
      - if:
          condition: { lambda: 'return !id(snd_block) && id(gate_ms) != 0;' }
          then:
            - lambda: 'id(gate_ms) = 0;'

      # ---- AND RE-MUTE THE MOMENT AUDIO STOPS: default-muted at idle ----
      #
      # This is the symmetric half, and it generalises the fix instead of chasing
      # cold starts one at a time. Previously the mute was asserted at two SPECIFIC
      # places (boot, and talk_begin), which protected the transients we happened to
      # have thought of. JP's result proved the mechanism works — exempting the talk
      # tap from the haptic removed the touch pop entirely — but also isolated the one
      # we had NOT covered: the REPLY's own driver cold start, ~2.95s after the chime,
      # because the 500ms driver timeout unloads the driver during the gap while Piper
      # synthesises. Nothing was in position to mute that one.
      #
      # Holding the DAC muted whenever the speaker is stopped means EVERY cold start
      # begins muted, including ones nobody has enumerated yet — the same reason the
      # chime guard asks `spk->is_running()` rather than tracking per-call-site flags.
      #
      # It costs ZERO audio, for the reason documented above: every playback preloads
      # 5 x 10ms of memset-zero silence before calling i2s_channel_enable(), so the
      # unmute above lands inside that window. This mute lands after the LAST frame,
      # which is quieter still.
      #
      # Failure direction is preserved and it is why this is safe: the condition is
      # re-evaluated against live hardware every 10ms, so a stuck mute cannot persist.
      # The moment audio runs, the branch above unmutes it. Worst case is the pop
      # returning, never silence.
      #
      # DELAYED BY 200ms, not immediate. Asserting REG31 mute steps the DAC output
      # while the amp is still enabled — the same class of event as the transient this
      # whole subsystem exists to suppress, just at the other end of playback. Two
      # things argued it was harmless and one argued it was not, and CORRECTING THE
      # DATASHEET ERROR (#3) REMOVES ONE OF THE TWO — so the conservative choice below
      # is now better justified than when it was made, not worse:
      #
      #   harmless: the last frame is end-of-speech near-silence.               STANDS.
      #   harmless: "ES8311 mute is normally a soft step".                      FALSE.
      #             DAC_RAMPRATE is bits 7:4 and the driver writes 0x08, which sets
      #             them to 0 = soft ramp DISABLED; bit 3 is DAC_EQBYPASS. The mute is
      #             a HARD STEP. This was the second of the two places that asserted
      #             slewing; the other was the pop-suppression block above.
      #   harmful:  this board's 0.39uF coupling caps are worst-case for pop per the
      #             amp's own datasheet.                                       STANDS.
      #
      # So it is one argument against and one for, on a board already known to be
      # worst-case. Rather than bet, the mute waits until the output has settled.
      #
      # 200ms also coalesces bursts: a volume tap that plays a tick every few hundred
      # ms would otherwise mute and unmute between every one.
      #
      # The deadline is CANCELLED if audio resumes, so a reply that stutters does not
      # get muted mid-sentence.
      - if:
          condition:
            lambda: 'return !id(dac_muted) && !id(spk)->is_running() && id(remute_at) == 0;'
          then:
            - lambda: 'id(remute_at) = millis() + 200u; if (id(remute_at) == 0) id(remute_at) = 1;'
      - if:
          condition:
            lambda: 'return id(remute_at) != 0 && id(spk)->is_running();'
          then:
            - lambda: 'id(remute_at) = 0;'
      - if:
          condition:
            lambda: |-
              return id(remute_at) != 0 &&
                     (int32_t) (millis() - id(remute_at)) >= 0;
          then:
            - audio_dac.mute_on: es8311_dac
            - lambda: 'id(dac_muted) = true; id(remute_at) = 0;'

      # ---- THE AMP FOLLOWS THE SPEAKER ----
      #
      # JP's two reports on the SAME build are a controlled experiment, and they point
      # at the amp rather than the codec:
      #
      #   mic cold start   (in talk_begin)  DAC muted + amp blanked  -> NO POP
      #   reply cold start (after the gap)  DAC muted, amp NOT       -> POP
      #
      # Both are MCLK restarts on the same clock domain. The only difference is the
      # amp blank. And the codec mute is now positively excluded: the watchdog holds
      # REG31 muted whenever the speaker is stopped, so the DAC was provably muted
      # before the reply's cold start — and it popped anyway. Every documented ES8311
      # anti-pop mechanism is counted in LRCK periods, which is exactly the resource
      # that stops. The bit persists; it just has no effect.
      #
      # So gate the AMP on the same signal, for the same reason the mute inversion
      # exists: cover every cold start, including ones nobody has enumerated, instead
      # of adding a third specific site. This SUPERSEDED talk_begin's amp_blank call,
      # which has since been deleted along with the script (#17) — at a tap the speaker
      # is already stopped, so the amp is already off.
      #
      # >>> THE COST IS REAL AND IS AUDIBLE: ~50ms of soft start on every reply. <<<
      # The FM8002E's wake is ~100ms typical but a playback only preloads 5 x 10ms of
      # silence, so the amp is still waking when the first ~50ms of speech arrives —
      # the first phoneme is attenuated. That is the trade: a soft onset instead of a
      # click. It is JP's ear that decides, so it is A/B-able live — the Amp Blank
      # Width number gates this whole branch, and setting it to 0 restores the amp
      # permanently and brings the pop back.
      #
      # Why "last speaker activity -> reply" and not "chime -> reply": the driver is
      # idle for ~7s across a turn (measured 19:07:05.910 -> 12.718), because the span
      # includes the user's own speech, STT and the LLM. So no realistic TTS speedup
      # keeps the driver loaded — `timeout` would have to be ~10s, which is
      # functionally `never`, which starves the microphone. Closing the synthesis gap
      # is still worth doing for the dead air; it is not a fix for this.
      #
      # >>> AND THE DEVICE IS ALREADY READY FOR IT — #11 NEEDS NO FIRMWARE CHANGE AND
      #     NO FLASH. <<< Verified in ESPHome's source rather than assumed:
      #     voice_assistant.cpp:812-825 handles VOICE_ASSISTANT_INTENT_PROGRESS and, if
      #     HA sends `tts_start_streaming` == "1" with a non-empty response URL, plays
      #     that URL immediately and enters STREAMING_RESPONSE — i.e. it begins speaking
      #     while Piper is still synthesising. It is gated on NOTHING in this file: no
      #     `streaming:` option, no flag, only `media_player:` being configured, which
      #     it is. `started_streaming_tts_` then suppresses the duplicate play at :886.
      #
      # So the ~2.8s of dead air is entirely HA's to close (streaming-capable TTS, or a
      # `low`-quality voice). Do NOT add a device-side workaround for it, and do not
      # reintroduce on_tts_stream_start looking for one — see the note on the
      # voice_assistant block, where those triggers are a validation error without
      # `speaker:`. The firmware's part of #11 is already done and was done before the
      # issue was filed.
      # ---- AMP BLANKING: the only lever downstream of the codec ----
      #
      # WHY DAC MUTE CANNOT FIX THE TAP-TO-START POP.
      #   `use_mclk: true` — MCLK is generated by the ESP32's I2S port, and the port only
      #   drives it while a channel is loaded. When BOTH the speaker and the mic are
      #   unloaded, MCLK STOPS ENTIRELY, and the ES8311 is a fully clock-dependent codec:
      #   with no MCLK its sigma-delta modulator and internal bias have no clock to run
      #   on. REG31 mute is enforced INSIDE that same clock domain, so it cannot hold the
      #   analog output across an MCLK stop/start — there is no clock with which to
      #   enforce it. That is a mechanism-level limit, not a tuning problem, and it
      #   explains the surviving pop precisely: tapping to talk starts the MICROPHONE,
      #   which restarts MCLK on the shared port while the DAC is muted and pops anyway.
      #
      # ── ONE PART, TWO NAMES ───────────────────────────────────────────────────────
      # This file used to call the amplifier SC8002B here and FM8002E above, which read
      # as two different chips. Settled on FM8002E, because that is where the numbers we
      # actually depend on come from: Ci 0.1-0.39uF and TD = 100ms typical are read off
      # the FM8002E datasheet specifically, and the ~100ms wake sets the floor under
      # amp_blank_ms.
      #
      # They are very likely the same part — FM8002E's vendor is 深圳市富满电子 /
      # superchip.cn, i.e. SC = SuperChip — and SC8002B is what the board schematic
      # prints. But pin-for-pin equivalence is UNCONFIRMED, so this is a naming decision
      # made for traceability, not an identification. If a measurement ever disagrees
      # with the datasheet, that gap is the first thing to suspect.
      # ──────────────────────────────────────────────────────────────────────────────
      #
      # SO THE ONLY REMAINING SOFTWARE LEVER IS THE AMPLIFIER. GPIO1 is a real hardware
      # disconnect on the FM8002E (schematic silkscreen says SC8002B — see above;
      # "Audio power amplifier circuit"), downstream of everything the codec does, so it
      # suppresses clock clicks that no codec register can reach.
      #
      # THE COST IS UNMEASURED AND MIGHT EXCEED THE BENEFIT. The FM8002E is bridge-tied,
      # so on enable both outputs slew together and the DIFFERENTIAL the speaker sees
      # should stay small — that is the argument for expecting a quiet enable. But it is
      # an argument, not a measurement, and a permanently-enabled amp is also the reason
      # there is no idle hiss today.
      #
      # Defaulted ON only because the baseline it replaces is a KNOWN audible pop with
      # zero mitigation, so any change is measurable against a bad known state.
      # >>> If the amp's own enable click is worse than the pop, set amp_blank_ms to 0
      #     and this becomes a no-op with no other edits needed. <<<
      #
      #
      # ---- ONE DESIRE, COMPARED AGAINST ONE TRACKED REALITY ----
      #
      # Replaces the two condition-pair branches that used to live here. They could not
      # express `amp_switch` correctly: the enable branch did not consult it at all,
      # and bolting the check on would have left `amp_off` able to desync from the
      # hardware whenever the switch was toggled (switch writes the GPIO, shadow flag
      # does not follow, and then neither branch fires because both are guarded on that
      # same stale flag — the amp then sits electrically live across the next cold
      # start, i.e. the pop returns for one playback after every switch-on).
      #
      # Computing the DESIRE once and comparing it to the tracked state is immune to
      # that: one writer, one comparison, and a mismatch is always corrected on the
      # next tick. `amp_off` is still tracked purely so an unchanged desire costs no
      # GPIO write at 100Hz.
      #
      # >>> THE AMP IS THE LOAD-BEARING HALF OF THE SILENCE GATE. <<<
      # `snd_block` is an independent conjunct here, so it forces the amp off
      # REGARDLESS of Amp Blank Width — including at 0, which the old branch structure
      # could not have expressed. That matters because the amp is a hardware disconnect
      # downstream of everything the codec does, and nothing in ESPHome's audio stack
      # touches it; the REG31 mute above is the half that can be cleared behind our
      # back. Two halves, failing in different directions.
      #
      # >>> THE COST IS REAL AND IS AUDIBLE: ~50ms of soft start on every reply. <<<
      # Unchanged by this rewrite, and not removable by scheduling — an amp awake
      # across the MCLK cold start is precisely what brings the pop back. The lever is
      # padding the audio, not moving the gate.
      #
      # ⚠️ AND THE PADDING CANNOT BE DONE FROM THIS DEVICE (#12). The obvious
      # device-side version — play ~100ms of silence at on_tts_start so the amp wakes
      # during it — is not merely redundant, it is IMPOSSIBLE, and the reason is one
      # flag in ESPHome's own source:
      #
      #   reply    voice_assistant.cpp:817 and :886
      #            make_call().set_media_url(url).set_announcement(true).perform()
      #            -> NO enqueue command
      #   announce voice_assistant.cpp:1064-1067
      #            .set_command(MEDIA_PLAYER_COMMAND_ENQUEUE)
      #
      # and in speaker_media_player.cpp:152-164, `if (!enqueue)` runs
      # `announcement_playlist_.clear()` and then start_url(). So a reply's own play
      # call CLEARS whatever we queued ahead of it. A silent pad would be destroyed by
      # the very audio it was padding — and it would be worse than doing nothing,
      # because it would load the driver, get wiped, and add one more clock stop/start
      # to a path whose entire problem is clock stop/starts.
      #
      # THIS IS WHY THE ANNOUNCE-PATH CORROBORATION DOES NOT TRANSFER. #12 notes,
      # correctly, that pushed announcements have no soft onset because the herald is
      # enqueued ahead of them. That is true and it is evidence the mechanism is right —
      # but it works ONLY because the announce path sets ENQUEUE and the reply path does
      # not. A reused mechanism does not carry its guarantees with it (#23's lesson, in
      # audio instead of navigation).
      #
      # AND THE EXISTING 50ms OF PRELOAD IS A HARDCODED CONSTANT, NOT A KNOB — this is
      # the lever that looks most promising and it is closed too. The ~50ms residual
      # exists because a playback preloads 5 x 10ms of memset-zero silence before
      # i2s_channel_enable(). If that were configurable, raising it WOULD be padding the
      # audio, on the device. From i2s_audio_speaker_standard.cpp:23-24:
      #
      #     static constexpr uint32_t DMA_BUFFER_DURATION_MS = 10;
      #     static constexpr size_t   DMA_BUFFERS_COUNT      = 5;
      #
      # Both are file-local `static constexpr` in the component, exposed to no YAML
      # option, so changing them means forking a core ESPHome component. And they are
      # not inert: WRITE_TIMEOUT_TICKS is DMA_BUFFER_DURATION_MS * (DMA_BUFFERS_COUNT+1)
      # and dma_buffers_duration_ms feeds the ring-buffer sizing — so buying 50ms of amp
      # runway also moves the write timeout and the buffer budget on a board whose
      # display already competes for main-loop time. That competition is why
      # `buffer_duration` is 500ms and not 100ms, and it was AUDIBLE. A poor trade for
      # one phoneme, and it would need re-verifying against choppiness rather than
      # arguing.
      #
      # So the padding has to come from wherever the TTS audio is PRODUCED, i.e. HA.
      # Nothing on the device can substitute, and no amount of firmware cleverness
      # changes the flag on someone else's `make_call()`.
      - lambda: |-
          // `snd_block` already carries amp_switch (it is an input to `permitted`
          // above), so this does not re-test it — one question, asked once. Naming it
          // twice is how the two writers got out of step in the first place.
          const bool want = !id(snd_block) &&
                            id(amp_switch).state &&
                            (id(amp_blank_ms_g) == 0 || id(spk)->is_running());
          if (want == id(amp_off)) {          // amp_off means "currently disabled"
            if (want) id(amp_enable)->turn_on();
            else      id(amp_enable)->turn_off();
            id(amp_off) = !want;
          }

esp32:
  variant: esp32s3
  flash_size: 16MB
  framework:
    type: esp-idf

# N16R8 module: 8MB OPI (octal) PSRAM. Octal consumes GPIO33-37 —
# do not use those pins. Without this, display buffers won't fit.
psram:
  mode: octal
  speed: 80MHz

logger:
  # NOTE: the i2c bus scan prints at [C]/CONFIG level, and in ESPHome's
  # ordering CONFIG is MORE verbose than INFO — so level: INFO silently
  # hides the scan results. Keep DEBUG until bring-up is finished.
  level: DEBUG
  #
  # TO VERIFY THE BANDED REDRAW (the one test that matters), swap the above for
  # the block below. mipi_spi logs both the dirty box and the flush time every
  # frame (mipi_spi.h:570, 575-576) at VERBOSE.
  #
  # The global `level:` is a COMPILE-TIME ceiling — esph_log_v is compiled out
  # entirely unless the global level is VERBOSE, so per-tag VERBOSE alone does
  # nothing. Raise the global and dial the noisy tags back down:
  #
  # level: VERBOSE
  # logs:
  #   mipi_spi: VERBOSE
  #   sensor: INFO
  #   voice_assistant: DEBUG
  #   esp32_rmt_led_strip: INFO
  #   i2s_audio: INFO
  #
  # Expected on a SPEAKING frame:  "x_low 0, y_low 188, x_high 239, y_high 263"
  #                                "Total update took 10..13ms"
  #
  # That upper figure was 7..10ms before the hearth-wyrm landed in this band. The
  # wyrm covers ~25% of the band's area and its per-pixel shading is the added cost,
  # so 10..13ms IS the healthy reading now. Anyone comparing against the old number
  # would report the wyrm as a performance regression — which is why it is corrected
  # here rather than left for the reader to reconcile. If it exceeds ~16ms, the two
  # documented flame-loop optimisations (cache the neck; restrict the per-pixel loop
  # to the stage columns) are the levers, in that order.
  # Expected between ticks:        nothing at all (empty box -> flush skipped,
  #                                mipi_spi.h:573).
  # If a flame frame logs y_low 0, band isolation is broken.

api:
  encryption:
    key: !secret api_key
  # Wake word can only be armed once HA is actually on the other end: arming is
  # `voice_assistant.start_continuous`, which sends a pipeline-start request over
  # this connection. Arming in on_boot would race the WiFi/API handshake and lose.
  #
  # This fires for ANY api client (the esphome CLI and the OTA dashboard included),
  # not just HA. That is harmless — wake_word_arm is `mode: restart` and no-ops when
  # the assistant is already running — but it is why the arm lives in a guarded
  # script rather than being inlined here.
  # ---- slack_note: the bridge tells us which conversation an announce
  # belongs to (contract: slack-bridge.md "Voice replies"; the ha session's
  # brief, 2026-08-09). Matches the newest announce entry with this exact
  # speech and stamps its channel; falls back to the newest announce when the
  # text drifted (the bridge may trim). The chronicle's reply button reads it.
  services:
    - service: slack_note
      variables:
        channel: string
        speech: string
      then:
        - lambda: |-
            int fallback = -1;
            for (int i = (int) id(chron).size() - 1; i >= 0; i--) {
              const std::string &e = id(chron)[(size_t) i];
              if (e.empty() || e[0] != 'a') continue;
              if (fallback < 0) fallback = i;
              if (e.substr(1) == speech) {
                id(chron_chan)[(size_t) i] = channel;
                return;
              }
            }
            if (fallback >= 0) id(chron_chan)[(size_t) fallback] = channel;
    # ---- show_image: the vision (2026-08-24, JP: "add the ability to
    # display slack images"). Bridge 1.4.0 stashes the announced image's
    # thumb at HA's /local/ember/ and the ember_slack_vision automation
    # relays it here. The device fetches over TLS (edge name, IDF cert
    # bundle) into PSRAM; on_download_finished is what opens the vision,
    # so a failed fetch degrades to the spoken announce and nothing else.
    - service: show_image
      variables:
        url: string
        caption: string
        urls: string
      then:
        - lambda: |-
            id(vision_caption) = caption;
            // urls (2026-08-24 evening, JP sent two photos and saw one):
            // ALL of the message's images as '|'-packed /local paths; url
            // stays as the absolute first for compatibility. Swipe moves
            // vision_idx through the set.
            std::string pk = urls;
            if (pk.empty()) {
              size_t sl0 = url.find("/local/");
              pk = (sl0 == std::string::npos) ? url : url.substr(sl0);
            }
            id(vision_urls) = pk;
            id(vision_idx) = 0;
            id(vision_url) = url;
            id(vision_view) = 0;
            id(vision_px) = 0;
            id(vision_py) = 0;
            // Stamp the newest announce entry with the WHOLE set (JP:
            // images "should appear in the chronicle") — same newest-'a'
            // targeting as slack_note's fallback: the announce this image
            // rode in on is seconds old at most. Stored as /local paths so
            // an edge-name change can't strand the chronicle.
            for (int i = (int) id(chron).size() - 1; i >= 0; i--) {
              const std::string &e = id(chron)[(size_t) i];
              if (!e.empty() && e[0] == 'a') {
                id(chron_img)[(size_t) i] = pk;
                break;
              }
            }
        - lambda: 'id(vision_img)->set_url(id(vision_url).c_str());'
        - component.update: vision_img
  on_client_connected:
    - script.execute: wake_word_arm

ota:
  - platform: esphome
    password: ${ota_password}

# ---- the vision's plumbing (2026-08-24) ----
# http_request exists for online_image; TLS to the HA edge rides the ESP-IDF
# certificate bundle (Let's Encrypt roots included), and the ~45KB handshake
# heap is fine on this PSRAM board. online_image holds ONE image — the newest
# vision — as RGB565 in PSRAM (240x188 = ~90KB); resize downscales the
# bridge's thumb_480 at decode to fit the overlay's image area (232px minus
# title and caption strips). update_interval: never — the show_image service
# is the only trigger, so the device never polls for a picture nobody sent.
http_request:
  timeout: 15s

online_image:
  # The FIT buffer: fullscreen-capable (240x320) since the tap-to-fullscreen
  # work — the framed view draws it through a clipping rect instead of a
  # smaller buffer, so one fetch serves both views. ~150KB RGB565 in PSRAM.
  - id: vision_img
    url: "https://ha.jphe.in:8123/local/ember/placeholder.jpg"
    format: jpeg
    type: RGB565
    resize: 240x320
    update_interval: never
    on_download_finished:
      - lambda: |-
          // Entered HERE, not in the service: a vision only opens once its
          // image is actually in memory, so mode 8 can never paint a stale
          // or half-fetched frame. Same action-only discipline as every
          // opener since the tome's per-report bug.
          id(ui_last_ms) = millis();
          id(ui_sel) = -1;
          id(ui_action) = 0;
          id(ui_mode) = 8;
          id(ui_gen)++;
    on_error:
      - lambda: 'ESP_LOGW("vision", "image fetch failed - staying on the hearth");'
  # The ZOOM buffer: the stash is a 480-wide thumb and the panel is 240, so
  # decoding at up to 480 yields true 2x detail. Fetched lazily on the first
  # pinch-out per image (zoom_url tracks which image it holds); ~355KB RGB565
  # in PSRAM. While it downloads, the zoomed view shows the fit buffer.
  - id: zoom_img
    url: "https://ha.jphe.in:8123/local/ember/placeholder.jpg"
    format: jpeg
    type: RGB565
    resize: 480x376
    update_interval: never
    on_download_finished:
      - lambda: |-
          if (id(ui_mode) == 8 && id(vision_view) == 2) id(ui_gen)++;
    on_error:
      - lambda: 'ESP_LOGW("vision", "zoom fetch failed - staying at fit scale"); id(zoom_url) = "";'

# ---- douse (2026-08-24, JP: "an off option") ----
# Deep sleep until the BOOT button is pressed — the battery alarm has said
# "or bid me goodnight" since the ladder was built, and this is finally that.
# GPIO0 is RTC-capable and already the board's one button; pressing it (LOW)
# wakes the chip cold, which is a full reboot into a normal boot. While
# doused: no display, no radio, no OTA — recovery is the same button. On the
# desk unit this works identically; it is simply "off until pressed".
deep_sleep:
  id: hearth_sleep
  wakeup_pin:
    number: GPIO0
    inverted: true
    ignore_strapping_warning: true
    # GPIO0 is ALSO the BOOT binary_sensor — deliberately: one button, two
    # roles, in two non-overlapping lifetimes (awake it clicks; asleep it
    # wakes). allow_other_uses on both is the schema's way of saying we did
    # this on purpose.
    allow_other_uses: true
    mode:
      input: true
      pullup: true

# ⚠️ THE RECOVERY PATH FOR A BOARD YOU CANNOT REACH WITH A CABLE.
#
# Added 2026-08-03 with the mobile variant (#44), and it is that board that makes
# it necessary rather than merely tidy: the desk unit is on a bench with a USB-C
# socket in easy reach, so a failed OTA there costs a cable. The mobile unit lives
# behind 2 x M3x22 and a battery cover, so the same failure costs a disassembly of
# a device with a bare 18650 in it.
#
# What it buys: if the firmware reboots repeatedly (num_attempts), the next boot
# comes up with WiFi and the OTA server ONLY — no display, no I2S, none of the
# code that might be the thing crashing — so a fixed build can be pushed over the
# air. Without it, a boot-looping board is only recoverable over serial.
#
# boot_is_good_after is the important number, not num_attempts: a boot is only
# "successful" once the device has stayed up this long, so a crash 20 s in still
# counts as a failed boot and still counts toward safe mode. Defaults are used
# deliberately (10 attempts / 1 min / 5 min reboot timeout) — this has never had
# to fire, so there is no measurement here to justify tuning them.
safe_mode:

wifi:
  ssid: !secret wifi_ssid
  password: !secret wifi_password
  ap:

captive_portal:

########################  buses  ########################

# ES8311 codec (0x18) and FT6336G touch (0x38) share one bus.
i2c:
  - id: i2c_bus
    sda: GPIO16
    scl: GPIO15
    frequency: 100kHz
    scan: true

spi:
  - id: lcd_spi
    clk_pin: GPIO12
    mosi_pin: GPIO11
    miso_pin: GPIO13

########################  audio  ########################

i2s_audio:
  - id: i2s_bus
    i2s_mclk_pin: GPIO4
    i2s_bclk_pin: GPIO5
    i2s_lrclk_pin: GPIO7

audio_dac:
  - platform: es8311
    id: es8311_dac
    i2c_id: i2c_bus
    address: 0x18
    bits_per_sample: 16bit
    sample_rate: 16000
    use_mclk: true
    # ESPHome's default mic_gain is 42DB — the MAXIMUM. Stacked on
    # voice_assistant's auto_gain: 31dBFS and volume_multiplier: 2.0 that
    # clips and pins the dBFS meter. Start conservative; this is tuning
    # knob #2 after the mic channel question.
    mic_gain: 36db
    # Deliberately NOT setting use_microphone: true.
    # In ESPHome's es8311 driver that flag enables a PDM *digital* mic.
    # This board's mic is an ANALOG MEMS part wired differentially into
    # MIC1P/MIC1N, so the default (false) is correct — it leaves
    # REG14 = 0x1A ("analog MIC + max PGA gain").

speaker:
  - platform: i2s_audio
    id: spk
    i2s_audio_id: i2s_bus
    i2s_dout_pin: GPIO8        # -> ES8311 DSDIN (schematic net I2S_DI)
    dac_type: external
    audio_dac: es8311_dac
    sample_rate: 16000
    bits_per_sample: 16bit
    channel: mono
    # 500ms is ESPHome's OWN DEFAULT. This was 100ms — copied from the
    # m5stack-atom-echo config, which has NO DISPLAY competing for the main
    # loop. Here a full display frame blocks the loop for up to 60ms and a
    # scroll-band repaint for 18-22ms, and the scroll band repaints on
    # on_tts_start — i.e. exactly when playback begins. 100ms of runway
    # against a 60ms blocking redraw is a coin flip, and JP heard it as
    # choppy audio. At 16kHz/16-bit mono this is 16000 bytes; PSRAM is free.
    # >>> Do not lower this to "save memory". The memory is not the scarce
    #     resource here; main-loop time is. <<<
    buffer_duration: 500ms

    # ⚠️ TWO DIFFERENT 500ms VALUES LIVE ON THIS COMPONENT. Do not conflate them.
    # buffer_duration (above) is the measured choppiness fix and STAYS at 500ms.
    # `timeout` is a different problem: how long the driver stays LOADED after the
    # last audio. While loaded, the speaker holds I2SAudioComponent's single shared
    # `Mutex lock_` (i2s_audio.h:64-71). The microphone acquires that lock with a
    # NON-BLOCKING try_lock() (i2s_audio_microphone.cpp:98) and on failure backs off
    # a FULL SECOND:
    #     "Driver failed to start; retrying in 1 second"
    #     status_momentary_error("driver_fail", 1000)    (:399-403)
    #
    # So at the 500ms default, ANY touch-to-talk within ~500ms of audio ending —
    # Ember finishing a reply, the done chime, an announcement — costs a 1.0s mic
    # stall with an error in the log that reads like a hardware fault. Pre-existing,
    # not new; 100ms shrinks the window it can happen in by 5x.
    #
    # This is only safe BECAUSE the DAC-mute manager below fixes the pop: a shorter
    # timeout means more driver load/unload cycles, and until now every one of those
    # was an audible transient. Fixing the pop is what makes this tunable at all.
    #
    # >>> Do NOT set `timeout: never`. It would remove the transient entirely and
    #     silently starve the microphone forever — try_lock() could never succeed,
    #     and the only symptom is "Ember can't hear me". <<<
    #
    # REVERTED 100ms -> 500ms (Revision 8), because 100ms made the pop WORSE and
    # did not fix what it was aimed at.
    #
    # It was lowered to shrink the window where the speaker holds the shared lock and
    # starves the mic. But the captured log shows the contention running the OTHER
    # way: the SPEAKER failing with "Parent bus is busy" because the MIC held the lock
    # for the length of an utterance. No `timeout` value affects that direction.
    #
    # Meanwhile it multiplied driver cycles: at 100ms, six volume taps in two seconds
    # are six full load/unload cycles (JP's log shows exactly that — six
    # Starting/Stopped pairs). At 500ms they COALESCE into one session, because the
    # driver stays loaded between taps. Since each cycle is a clock stop/start, cycle
    # count is what correlates with audible artifacts — so a longer timeout is the
    # cheap, certain reduction.
    #
    # The mic-starvation problem it was meant to solve is now handled precisely in the
    # `talk_begin` script, which WAITS for the speaker to release the lock instead of
    # letting the mic's blind 1-second backoff absorb it.
    timeout: 500ms

microphone:
  - platform: i2s_audio
    id: mic
    i2s_audio_id: i2s_bus
    i2s_din_pin: GPIO6         # -> ES8311 ASDOUT (schematic net I2S_DO)
    adc_type: external
    pdm: false                 # analog mic behind the codec, not PDM
    channel: left              # ES8311 is mono; ADC data sits in the LEFT slot
    sample_rate: 16000
    bits_per_sample: 16bit
    # NOTE: deliberately NO on_data lambda here.
    #
    # on_data fires at 62.5Hz (i2s_audio_microphone.cpp READ_DURATION_MS = 16)
    # and its automation runs SYNCHRONOUSLY inside mic_task — priority 23,
    # 4096-byte stack. Anything slow there directly starves the I2S read, and
    # writing globals from that task while the main loop reads them for drawing
    # is a cross-task race.
    #
    # sound_level (below) gives the same information at 20Hz through a proper
    # lock-free ring buffer and publishes from loop(), so its on_value runs in
    # the main loop. Since a visual waveform only needs ~16-20Hz anyway, the
    # hand-rolled path bought nothing and cost thread-safety. Everything that
    # touches the display now runs single-threaded in the main loop.
    #
    # (The one exception, added deliberately and kept to a single 32-bit add,
    # is the speaker frame counter registered in on_boot. See the note there.)

output:
  - platform: gpio
    id: amp_enable
    pin: GPIO1                 # amp SHUTDOWN — ACTIVE LOW
    inverted: true

  - platform: ledc
    id: backlight_pwm
    pin: GPIO45                # Also the VDD_SPI strapping pin, but SAFE here:
    frequency: 20000Hz         # the schematic has R32 = 10K gate-to-GND on the
                               # BSS138 that drives the backlight, which hard-
                               # wires the strap LOW in hardware. The strap is
                               # latched at reset while GPIO drivers are still
                               # inputs, so R32 always wins — no firmware
                               # setting can cause the 1.8V brownout.
                               # Active-HIGH, so no `inverted:`.
                               # Screen dark through boot is expected.

  # GPIO18 = CTP_RST is deliberately left UNCONFIGURED.
  #
  # The schematic shows no pull-up/pull-down on this net, so in principle it
  # floats and should be driven — Oracle flagged that, correctly in theory.
  # But empirically, BOTH attempts to touch this pin broke the touch driver:
  #   - `reset_pin: GPIO18` on the touchscreen  -> "touch driver failed to start"
  #   - a gpio `output:` held high at on_boot   -> "touch driver failed to start"
  # Left unconfigured, the FT6336 pulls RSTN high internally and reports
  # chipid 100. celer's config (the only other working one for this board)
  # also omits it. Tested beats derived.
  #
  # FOLLOW-UP: proper reset handling probably needs a timed low pulse BEFORE
  # i2c setup, not a static level. Tracked as hardening, not shipped blind.

light:
  - platform: monochromatic
    id: backlight
    name: Backlight
    output: backlight_pwm
    restore_mode: RESTORE_DEFAULT_ON

  - platform: esp32_rmt_led_strip
    id: status_led
    name: Status LED
    pin: GPIO42
    num_leds: 1
    chipset: ws2812
    rgb_order: GRB
    # `pulse` is registered via register_monochromatic_effect(), which also
    # appends it to ADDRESSABLE_EFFECTS (light/effects.py:126-139) — so it is
    # valid on a WS2812. Costs no LCD SPI at all.
    effects:
      - pulse:
          name: bank
          transition_length: 2s
          update_interval: 2s
          min_brightness: 8%
          max_brightness: 22%
      - pulse:
          name: crucible
          transition_length: 350ms
          update_interval: 350ms
          min_brightness: 45%
          max_brightness: 100%

########################  runtime controls  ########################
# Live-adjustable from HA so tuning doesn't need a reflash. The es8311 boots
# at set_volume(0.75) = 0dB (es8311.cpp:33), which JP reported as too loud.
number:
  - platform: template
    id: spk_volume
    name: Speaker Volume
    icon: mdi:volume-high
    optimistic: true
    restore_value: true
    initial_value: 45
    min_value: 0
    max_value: 100
    step: 5
    unit_of_measurement: "%"
    mode: slider
    set_action:
      - audio_dac.set_volume:
          id: es8311_dac
          volume: !lambda 'return x / 100.0f;'

  # MIC GAIN — the ES8311's analog ADC PGA, made live.
  #
  # It was a compile-time constant (`mic_gain: 36db` on the audio_dac). That is the wrong
  # shape for a knob whose correct value depends on the room, the speaker's distance and
  # how loudly they talk — every adjustment cost a reflash.
  #
  # ⚠️ THE STEP IS 6dB AND THAT IS NOT A STYLE CHOICE. REG16 takes a 3-bit field with
  # exactly eight legal values, 0/6/12/18/24/30/36/42 dB (ES8311MicGain in the driver's
  # header). Nothing between them is representable, so a continuous slider would report a
  # setting the hardware cannot hold. Quantise here rather than silently rounding later.
  #
  # WHY IT WRITES THE REGISTER DIRECTLY. `set_mic_gain()` only assigns a member — the
  # driver writes REG16 once, in setup() (es8311.cpp:200). Calling the setter alone changes
  # nothing until the next boot, which would look exactly like a control that does not work.
  # So both happen: the member is kept honest for any later re-init, and the register is
  # written for the change to take effect now.
  #
  # DEFAULT 36dB, DELIBERATELY BELOW THE MAXIMUM. ESPHome's own default is 42dB — the top of
  # the range — and stacked on voice_assistant's auto_gain and volume_multiplier it clips and
  # pins the dBFS meter. Higher is not better here: it is more sensitive AND more clipped.
  - platform: template
    id: mic_gain_num
    name: Mic Gain
    icon: mdi:microphone-settings
    optimistic: true
    restore_value: true
    initial_value: 36
    min_value: 0
    max_value: 42
    step: 6
    unit_of_measurement: "dB"
    mode: slider
    set_action:
      - lambda: |-
          // 0..42dB in 6dB steps -> the 3-bit REG16 field, 0..7.
          int g = (int) lroundf(x / 6.0f);
          if (g < 0) g = 0;
          if (g > 7) g = 7;
          id(es8311_dac)->set_mic_gain((es8311::ES8311MicGain) g);
          id(es8311_dac)->write_byte(0x16, (uint8_t) g);   // ES8311_REG16_ADC
          ESP_LOGI("mic", "gain -> %ddB (REG16=0x%02X)", g * 6, g);

  # THE OPEN EXPERIMENT, made turnable. Oracle's adjudication (2026-07-29) found the
  # decisive test had never actually been run: the "pop returned with blanking off"
  # result predates talk_begin's audio_dac.mute_on, so it shows blanking works
  # WITHOUT codec mute — not that codec mute is insufficient WITH it.
  #
  #   0   -> codec mute alone. If the pop returns, the transient is downstream of the
  #          digital mute and amp gating is the primary fix, not a redundant one.
  #   180 -> default. Clears the FM8002E's ~100ms typical wake (TD), the only hard
  #          number in the whole fix.
  #   300 -> headroom, if 180 proves marginal.
  #
  # Changing this cannot strand the amp — the PROPERTY is unchanged and the REASON is
  # not the one that used to be written here.
  #
  # It used to say "amp_blank sets a DEADLINE that the 10ms interval restores". That was
  # already false when written (amp_blank had no callers) and the machinery is now
  # deleted outright (#17). Retargeted rather than removed, because a live control whose
  # comment claims safety from a deleted mechanism is precisely the failure that let the
  # amp_switch bug (#1) hide for as long as it did.
  #
  # The property now holds for a simpler and stronger reason: the amp is a single DESIRE
  # recomputed from live hardware on every 10ms tick —
  #
  #     want = !snd_block && amp_switch.state && (amp_blank_ms_g == 0 || spk->is_running())
  #
  # so there is no pending state for a value change to strand. Set this to 0 and `want`
  # simply stops consulting `is_running()`; nothing has to be unwound, because nothing
  # was latched.
  - platform: template
    id: amp_blank_num
    name: Amp Blank Width
    icon: mdi:flash-off
    entity_category: diagnostic
    optimistic: true
    restore_value: false
    initial_value: ${amp_blank_ms}
    min_value: 0
    max_value: 400
    step: 20
    unit_of_measurement: "ms"
    mode: box
    set_action:
      - lambda: 'id(amp_blank_ms_g) = (uint32_t) x;'

########################  operating mode  ########################
# The HA-facing surface for op_mode. Same shape as the volume control: ONE authority
# (the global) with surfaces that are clients of it, rather than two stores that agree
# by convention. See the `on_volume` note on the media_player for the precedent.
#
# Options are listed quietest-last, so THE OPTION INDEX IS THE STORED VALUE and there
# is no mapping table at all. An earlier draft of this design needed one (and got to be
# clever about it being self-inverse); a monotonic control needs none, which is
# strictly better — a table that does not exist cannot drift.
select:
  - platform: template
    id: sel_mode
    name: Ember Mode
    icon: mdi:hexagon-multiple
    optimistic: true
    restore_value: false        # op_mode is the thing that persists, not this view
    options:
      - "Normal"
      - "No talking"
      - "Hush"
    initial_option: "Normal"
    set_action:
      # ⚠️ `i` IS NOT AVAILABLE HERE. A template select's set_action is a
      # `Trigger<StringRef>` (template/select/template_select.h:69), so the lambda gets
      # the chosen option as `x` and NOTHING ELSE — no index. An earlier draft of this
      # used `i` and `esphome config` reported "Configuration is valid!"; it failed at
      # `esphome compile` with "'i' was not declared in this scope". See the compile-vs-
      # config note in the header.
      #
      # Deriving the index with index_of() is better than a positional assumption
      # anyway: it reads the order off the select's OWN option list, so adding or
      # reordering an option cannot silently change which mode a row means.
      - lambda: |-
          const auto idx = id(sel_mode)->index_of(x.c_str(), x.size());
          if (!idx.has_value() || *idx > 2) return;
          id(op_mode) = (uint8_t) *idx;
          id(ui_gen)++;                  // the header names the mode, so repaint it
          id(force_full_repaint) = true; // one ~60ms frame; a mode change is rare

########################  announce path  ########################
# WHY THIS EXISTS: `assist_satellite.announce` returned HTTP 500 because
# FEATURE_ANNOUNCE is gated STRICTLY on voice_assistant's own media_player
# (voice_assistant.h:168-171). No media_player on voice_assistant => the satellite
# never advertises announce => HA cannot push speech at all: no timer chimes, no
# doorbell TTS, no notifications, only conversational replies.
#
# A standalone media_player NOT wired into voice_assistant does NOT fix it — the
# feature flag would still be unset and announce would still 500. It had to go on
# voice_assistant, which is `cv.Exclusive` with `speaker:` (:110-113).
#
# WHAT THAT COST, AND WHY IT ISN'T A LOSS:
#   Losing `speaker:` forbids on_tts_stream_start/on_tts_stream_end (:82-86), which
#   is what used to set SPEAKING and snapshot the frame counter. The display lambda
#   now DERIVES speaking from the speaker itself (spk->is_running() + frames
#   advancing). That is the same source of truth the animation already used, so the
#   grounding is intact — and it is strictly better, because it also lights up for
#   pushed announcements, which never fire a stream trigger at all.
#
# The frame counter is unaffected: the pipeline calls
# `decoder->add_sink(this_pipeline->speaker_)` — "Send audio directly to the
# speaker" (audio_pipeline.cpp:473-475) — so `spk` is still the direct sink and its
# add_audio_output_callback fires exactly as before. No mixer, no resampler.
media_player:
  - platform: speaker
    id: media_out
    name: Ember Speaker
    # YIELD THE MICROPHONE FOR PUSHED AUDIO. The touch path is covered in ui_dispatch;
    # this is the other way sound starts — an HA announcement, a finished timer — with
    # no tap to hang the yield off.
    #
    # ⚠️ READ THIS BEFORE REUSING on_announcement ANYWHERE ELSE. The unmute manager
    # below explicitly REJECTED this trigger, and that rejection is still correct:
    # on_announcement fires when the media_player enters its announcing state, which is
    # BEFORE the pipeline starts the speaker and before i2s_channel_enable(). Unmuting
    # there lands ahead of the clock transient, so the pop survives.
    #
    # That same early timing is exactly what this needs. "Too early to unmute" is "just
    # in time to hand over the I2S bus" — it fires before the speaker's first try_lock,
    # so the speaker wins the bus immediately instead of failing and retrying a second
    # later. Same trigger, opposite requirement. Do not "unify" the two.
    on_announcement:
      - micro_wake_word.stop:
    # Only the announcement pipeline is needed, and that is what removes the need
    # for a `mixer`: EVERY voice_assistant output path calls .set_announcement(true)
    # — conversational TTS (voice_assistant.cpp:817), streaming TTS (:886) and
    # on_announce (:1061,1067). A media_pipeline would only be for
    # media_player.play_media, and adding one WOULD force a mixer, because
    # announcement and media pipelines may not share a speaker
    # (speaker/media_player/__init__.py:91-100).
    announcement_pipeline:
      speaker: spk
      format: FLAC
      # These are inherited from `spk` if omitted (media_player/__init__.py:91-92),
      # but they are stated explicitly because they are what HA transcodes TO. Left
      # implicit, a future change to the speaker would silently retune the wire
      # format. 16k/mono also matches the es8311, so nothing has to resample and
      # `spk` never restarts mid-stream on a stream-info change.
      sample_rate: 16000
      num_channels: 1
    # Hearth chimes, embedded in flash as progmem (~250KB of the 16MB).
    #
    # `files:` is TOP-LEVEL on the media_player, not per-pipeline
    # (speaker/media_player/__init__.py:156), so these play through the existing
    # announcement_pipeline — no media_pipeline, therefore still no mixer and still
    # no resampler. All six are 16kHz/mono/16-bit, matching `spk` and the es8311
    # exactly, so nothing in the chime path can perturb what spk_frames means.
    #
    # Path is CORE.relative_config_path (audio_file/__init__.py:95). `scratch/sounds`
    # is a symlink to `../esphome/sounds` precisely so this line is IDENTICAL in the
    # scratch copy and the committed esphome/ copy — otherwise the path would have to
    # be edited on every sync, which is a silent breakage waiting to happen.
    files:
      - id: chime_done
        file: sounds/chime_done.wav
      - id: chime_error
        file: sounds/chime_error.wav
      - id: chime_announce
        file: sounds/chime_announce.wav
      - id: chime_thinking
        file: sounds/chime_thinking.wav
      - id: chime_timer
        file: sounds/chime_timer.wav
      # 145ms. Length is a SAFETY constraint, not taste — it is short enough that
      # the mic can be opened after it finishes without adding perceptible latency.
      # Do not lengthen it and do not point this id at chime_listening.wav.
      - id: chime_touch
        file: sounds/chime_touch.wav
      # HAPTIC — a felt tap rather than a heard note. 24ms, fundamental + octave,
      # NO inharmonic partials, because a bell rings and a tap must not. Fires on
      # every touch target so the glass acknowledges contact even when the result
      # isn't visible yet. Loud (peak 0.55) BECAUSE it's short: the ear integrates
      # energy over ~30ms, so a brief transient has to be hot to register at all.
      - id: chime_haptic
        file: sounds/chime_haptic.wav
      # GUTTERING — the mobile cell is low. Declared in the SHARED config even
      # though only the mobile plays it (case 7 is gated by ${has_battery}), because
      # a media file id referenced by a compiled-in play action must exist on both
      # boards. Costs the desk unit 58KB of flash it never plays; the alternative —
      # a wrapper-only media file — would fork the chime script per device, which is
      # the copy-drift shape this repo keeps paying for.
      - id: chime_guttering
        file: sounds/chime_guttering.wav
      # chime_listening.wav is deliberately NOT declared — see the chime script.
    volume_increment: 5%
    volume_initial: 45%
    # ⚠️ VOLUME IS NOT A SECOND AUTHORITY — and it very nearly was.
    # Speaker::set_volume() forwards straight to audio_dac_->set_volume()
    # (speaker/speaker.h:70-77): the SAME es8311 register number.spk_volume writes.
    # So the media_player's slider is not an independent software gain, it is a
    # second writer to one knob. Mirroring it back into spk_volume makes the
    # media_player a CLIENT of the number rather than a competitor: whichever
    # surface HA touches, spk_volume ends up authoritative and both stay in sync.
    # This terminates rather than ping-pongs — spk_volume's set_action calls
    # audio_dac.set_volume directly, which does not re-enter Speaker::set_volume.
    on_volume:
      - number.set:
          id: spk_volume
          value: !lambda 'return id(media_out).volume * 100.0f;'
      # ⚠️ SpeakerMediaPlayer::set_volume_ clears REG31 on its way through — twice, via
      # I2SAudioSpeakerBase::set_volume() and again directly. So adjusting volume from
      # HA while a muted reply is playing would UNMUTE IT. Re-assert here, at the
      # event, rather than waiting up to 250ms for the watchdog's cadence to notice.
      # The amp gate is what makes this defence-in-depth rather than the only thing
      # standing between a quiet mode and a leak.
      - if:
          condition: { lambda: 'return id(snd_block);' }
          then:
            - audio_dac.mute_on: es8311_dac
            - lambda: 'id(dac_muted) = true;'

    ####################################################################
    # POP SUPPRESSION — keep the DAC muted while idle.
    #
    # SYMPTOM: an audible pop before EVERY audio — chimes, TTS replies,
    # announcements alike.
    #
    # CAUSE: the ES8311's DAC output DC-steps when the I2S clocks start. The
    # speaker starts and stops per utterance (one `Created ring buffer` per
    # playback), and GPIO1 is ALWAYS_ON with nothing toggling it per-utterance,
    # so the amp is faithfully amplifying a step — it is NOT a class-D turn-on
    # click, and it is not the assets (all have a 4ms raised-cosine attack).
    #
    # FIX: mute the DAC while idle, so the next I2S start happens INTO a muted
    # DAC and is never amplified. Unmute once audio is actually flowing.
    #
    # ⚠️ CORRECTION (#3) — THIS USED TO CLAIM THE UNMUTE SLEWS. IT DOES NOT.
    # The old rationale was "REG37 is the DAC ramp rate, set to 0x08 by the driver,
    # so the unmute slews instead of stepping". Per the datasheet DAC_RAMPRATE is
    # bits 7:4, and 0x08 sets those to 0 = SOFT RAMP DISABLED; bit 3 is DAC_EQBYPASS,
    # which is exactly what the driver's own comment says it is setting.
    # THE MUTE AND UNMUTE ARE BOTH A HARD STEP.
    #
    # The fix still works, and for a better reason than the one stated: it works
    # because the DAC is ALREADY muted when the clocks start, so the transient is
    # never amplified — not because the unmute is gentle. Muting *across* the
    # transient would still not work, and that was never about ramping either: the
    # reply cold start popped with the DAC provably muted.
    #
    # This matters beyond tidiness. A hard step is what makes the silence gate sound:
    # asserting the mute cannot leak a slewing tail. Anyone reasoning from the old
    # comment would conclude the opposite.
    #
    # WHY NOT `timeout: never` ON THE SPEAKER — it is the obvious fix and it is
    # a trap on this board. It would keep the I2S driver loaded and remove the
    # transient outright, but `I2SAudioComponent` has ONE shared `Mutex lock_`
    # (i2s_audio.h:64-71); the speaker holds it while its driver is loaded, and
    # the microphone acquires it with NON-BLOCKING `try_lock()`
    # (i2s_audio_microphone.cpp:98). A permanently-loaded speaker means the mic
    # silently fails to start with nothing logged — i.e. "Ember can't hear me",
    # traded for a pop. Do not do it.
    #
    # FAILURE DIRECTION IS DELIBERATE: a mute that never clears is a SILENT
    # DEVICE, which is strictly worse than a pop. So unmuting is triggered from
    # three independent places and backed by a watchdog (see `interval:`), while
    # muting happens only from on_idle. If any single path fails, the worst case
    # is the pop coming back — never silence.
    # on_announcement / on_play REMOVED as unmute anchors — they fire when the
    # media_player enters its playing state, which is BEFORE the pipeline starts the
    # speaker and therefore before i2s_channel_enable(). Unmuting there is ahead of
    # the clock transient, so the pop survives and the fix looks like it did nothing.
    # The 10ms is_running() anchor in `interval:` replaces them; it is the only
    # signal that means "the clocks are already up". Do not add them back.
    on_idle:
      # Mute AFTER playback ends, so the DAC is already muted before the next
      # I2S start. This also absorbs the stop transient.
      - audio_dac.mute_on: es8311_dac
      - lambda: 'id(dac_muted) = true;'

switch:
  # ⚠️ WAS `platform: output` WITH `output: amp_enable`, AND THAT WAS THE BUG.
  #
  # It made the switch a SECOND WRITER to amp_enable, competing with the 10ms
  # watchdog. Two consequences, both of which this file's own comments claimed were
  # impossible:
  #
  #   1. Turning the switch OFF did not mute the device. The watchdog's amp-enable
  #      branch did not consult it, so the next audio re-enabled the amp.
  #   2. HA's reported state could disagree with the electrical state, because the
  #      watchdog wrote the GPIO directly and never went through the switch.
  #
  # HOW IT HID, which is the instructive part: the `amp_blank` script — whose deadline
  # branch DID check `switch.is_on: amp_switch` — was never executed. There was no
  # `script.execute: amp_blank` anywhere in this file. So the one branch that honoured
  # the switch was dead code, and the comment describing its behaviour ("the interval
  # only restores the amp if the switch is on") read as if it described the live
  # branch. The output also looked correct, because the amp being ON is normal.
  # (Past tense throughout: that script is deleted (#17). This paragraph is the
  # post-mortem of bug #1, kept because the shape is worth keeping, and it is NOT a
  # description of any code that exists today.)
  #
  # THE FIX IS TO DELETE THE COMPETITOR, not to reconcile two writers — the same move
  # that settled volume and the LED. This switch is now pure INTENT and the 10ms
  # watchdog is the sole writer of amp_enable.
  #
  # restore_mode stays ALWAYS_ON deliberately: a persisted OFF would be a silent
  # permanent mute weeks later, which is the landmine SpeakerMediaPlayer's persisted
  # is_muted already represents. Do not change this to RESTORE_DEFAULT_ON.
  - platform: template
    id: amp_switch
    name: Speaker Amplifier
    icon: mdi:speaker
    optimistic: true
    restore_mode: ALWAYS_ON

  # prefers-color-scheme has no meaning on a bare SPI panel, so JP's
  # dark/light rule is honoured by exposing the daylight ramp as a control
  # rather than pretending a media query applies.
  - platform: template
    id: hearth_daylight
    name: Daylight Hearth
    icon: mdi:white-balance-sunny
    optimistic: true
    restore_mode: RESTORE_DEFAULT_OFF
    turn_on_action:
      - lambda: |-
          id(theme_light) = true;
          id(force_full_repaint) = true;
    turn_off_action:
      - lambda: |-
          id(theme_light) = false;
          id(force_full_repaint) = true;

  # ⚠️⚠️ HUSH HAS CHANGED MEANING. THIS IS A BEHAVIOUR CHANGE TO AN EXISTING CONTROL,
  # NOT A NEW FEATURE ALONGSIDE ONE. Anyone who learned the old behaviour will be
  # surprised, so it is spelled out here rather than left to be inferred.
  #
  #   BEFORE: "do not listen to me." It wrapped the entire body of `talk_begin`, so
  #           with Hush on, TAPPING THE SCREEN DID NOTHING AT ALL.
  #   NOW:    "do not make noise." Ember listens and converses normally; the reply
  #           arrives on screen instead of out of the speaker, and chimes are silent
  #           too. It is the quietest of the three modes, not a mute button on the
  #           microphone.
  #
  # The old gate in `talk_begin` is DELETED. Do not restore it — it is the one line
  # whose meaning inverts, and restoring it would make the quietest mode also the
  # deafest, which is not what it says on the tin.
  #
  # The entity survives so existing dashboards and automations referencing
  # switch.ember_hush keep working, and it is a CLIENT in the shape this file already
  # uses for volume: its state is a `lambda:` over op_mode rather than a stored bool,
  # so there is no second bit to drift and it CANNOT disagree with the mode. That is
  # also why restore_mode must be DISABLED.
  #
  # The old comment's honesty about the hardware is preserved and can now be
  # strengthened: sound_level is `passive: true`, so it never STARTS the microphone —
  # with the pipeline stopped nothing is captured at all, in any mode.
  - platform: template
    id: sw_hush
    name: Hush
    icon: mdi:volume-off
    restore_mode: DISABLED
    lambda: 'return id(op_mode) == 2;'
    turn_on_action:
      - lambda: 'id(sel_mode)->make_call().set_index(2).perform();'
    turn_off_action:
      - lambda: 'id(sel_mode)->make_call().set_index(0).perform();'

button:
  - platform: restart
    id: btn_restart
    name: Restart
    entity_category: diagnostic

  # Touch-controller recovery. Recipe and datasheet timings from
  # scratch/hosyond-s3/nebula-touch-reset.md §4-B.
  #
  # Exposed as a button so it is reachable from HA *remotely* — the whole point is
  # that recovering the touchscreen must not require the touchscreen. It is also
  # wired to the power menu, which the BOOT button can drive without touch.
  #
  # SAFE with respect to the boot-path rule: GPIO18 stays UNCONFIGURED at boot.
  # This only ever drives it at runtime, on explicit request, and hands it back to
  # the FT6336G's internal 3K pull-up (datasheet Figure 3-2) when done. It cannot
  # regress boot because it never runs during boot.
  #
  # nebula flagged `attach_interrupt_` re-entry as unverified. VERIFIED since:
  # ft63x6::setup() calls attach_interrupt_ -> ESP32InternalGPIOPin::attach_interrupt
  # (esp32/gpio.cpp:68-98), which guards gpio_install_isr_service behind a static
  # bool and then calls gpio_isr_handler_add(). IDF's handler_add REPLACES the
  # per-pin handler rather than appending, and we re-register the identical
  # (func, arg) for the identical pin — so re-running setup() is idempotent here.
  # It does not leak an ISR or double-fire.
  #
  # The blocking delay()s total ~310ms. That WILL log "took a long time"; it is a
  # deliberate manual recovery action, not a loop-rate path.
  - platform: template
    id: btn_rouse_touch
    name: Rouse Touch Sensor
    icon: mdi:gesture-tap
    entity_category: diagnostic
    on_press:
      - lambda: |-
          ESP_LOGW("ember", "touch recovery: pulsing CTP_RST");
          gpio_set_direction(GPIO_NUM_18, GPIO_MODE_OUTPUT);
          gpio_set_level(GPIO_NUM_18, 0);
          delay(10);                    // Trst >= 5ms  (FT6336G datasheet Table 3-5)
          gpio_set_level(GPIO_NUM_18, 1);
          delay(300);                   // Tpon >= 300ms before the chip reports
          gpio_set_direction(GPIO_NUM_18, GPIO_MODE_INPUT);  // back to the 3K pull-up
          id(touch)->setup();           // re-reads chip id; no reset (reset_pin unset)

binary_sensor:
  # Published by mic_sync_check. `problem` so ON means "these disagree" — the state a
  # dashboard needs to contradict itself with, not a health badge to look green.
  - platform: template
    id: mic_gain_desync
    name: Mic Gain Desync
    device_class: problem
    entity_category: diagnostic

  # The ONLY usable button on this PCB.
  #
  # K1/K2 are RESET and BOOT. RESET is hardwired to CHIP_PU (it resets the MCU and
  # the LCD) and cannot be read. So GPIO0/BOOT is the entire hardware input budget,
  # and GPIO 2/14/21 are the only free broken-out pins — adding real buttons means
  # soldering, which is out of scope.
  #
  # GPIO0 is a strapping pin (esp32/gpio_esp32_s3.py:35). The warning is advisory
  # only (pins.py:271-279) and `ignore_strapping_warning` silences it; it is
  # justified here because we only ever READ the pin at runtime, and strapping is
  # sampled once at reset. We attach no external pull — the board already has one.
  #
  # ⚠️ ONE REAL HAZARD: holding BOOT low *across a reset* enters ROM download mode.
  # Both handlers below are `on_click`, which fires on RELEASE, so the button is
  # always up before any action (including restart) runs. Do not convert these to
  # `on_press` without re-thinking that.
  - platform: gpio
    id: btn_boot
    name: Boot Button
    entity_category: diagnostic
    pin:
      number: GPIO0
      mode:
        input: true
        pullup: true
      inverted: true
      ignore_strapping_warning: true
      allow_other_uses: true   # shared with deep_sleep's wakeup (douse)
    # ---- SHORT AND DOUBLE LIVE IN on_multi_click; LONG STAYS AN on_click ----
    #
    # 2026-08-09, the chronicle's doorway. GPIO0/BOOT is the entire hardware
    # input budget, single and long were both spoken for, and the power menu
    # CANNOT grow a fifth row (its own static_assert: 72 + 5*46 - 3 = 299 is
    # past the overlay's floor at 263 — the same wall the mode submenu's
    # fourth row hit, one screenful up). A double-click is the only gesture
    # left in the budget.
    #
    # WHY THE SINGLE MOVED: on_click filters by press LENGTH alone, so each
    # half of a double-click IS a valid single — the two handlers cannot
    # coexist for sub-800ms presses without the single firing twice per
    # double. on_multi_click disambiguates by the gap: a lone short press is
    # only confirmed single after 410ms of silence. That buys the double at
    # the price of +410ms latency on opening the volume overlay — felt, and
    # judged worth it; every OTHER single-press meaning (cursor moves, menu
    # steps) happens with an overlay already up, where two quick presses were
    # already two distinct actions and remain exactly that.
    # ⚠️ The LONG press (900-6000ms) stays a plain on_click below: no multi
    # pattern here matches a press ≥900ms, so recovery-by-button — the reason
    # this button carries menus at all — does not depend on multi-click
    # disambiguation working.
    on_multi_click:
      # DOUBLE — open the chronicle, newest page first. From ANY mode: the
      # gesture is rare enough that stealing it from overlay contexts costs
      # nothing (a double inside the volume overlay used to mean two volume
      # steps; it now means "show me the chronicle", which is at worst one
      # surprise, not a trap — the overlay it replaces auto-dismisses anyway).
      - timing:
          - ON for 30ms to 800ms
          - OFF for 40ms to 400ms
          - ON for 30ms to 800ms
        then:
          - lambda: |-
              id(ui_last_ms) = millis();
              id(chron_page) = 0;                 // page 0 = the newest entries
              id(chron_sel) = -1;
              id(ui_mode) = 4;
              id(ui_action) = 0;
              id(ui_gen)++;
      # SINGLE — byte-for-byte the old short-press semantics, plus the two
      # chronicle modes dismissing back to the hearth.
      - timing:
          - ON for 30ms to 800ms
          - OFF for at least 410ms
        then:
          - lambda: |-
              id(ui_last_ms) = millis();
              if (id(ui_mode) == 0) {
                id(ui_mode) = 1;              // summon the volume overlay
                id(ui_action) = 0;
              } else if (id(ui_mode) == 1) {
                id(ui_action) = 2;            // step up (wraps — see below)
              } else if (id(ui_mode) >= 4) {
                // chronicle list or detail: the button backs out. Detail steps
                // back to the list; the list closes to the hearth. Two presses
                // from anywhere in the chronicle to a clean screen, no touch
                // required — the recovery property the menus were built on.
                if (id(ui_mode) == 5) {
                  id(ui_mode) = 4;
                } else {
                  id(ui_mode) = 0;
                  id(force_full_repaint) = true;
                }
                id(ui_action) = 0;
              } else if (id(ui_mode) == 3) {
                // ---- FOUR CURSOR POSITIONS IN A THREE-ROW MENU: THE CANCEL ----
                //
                // -1 (nothing lit) is the fourth position and it is the CANCEL. It
                // already meant dismiss on a long press — the branch below reads
                // `(ui_sel >= 0 && ui_sel < 3) ? apply : dismiss` and always has. The
                // defect was that -1 was UNREACHABLE once the cursor moved: a plain
                // `% 3` walks 0,1,2,0,1,2 forever, so from any lit row the only button
                // exit was to APPLY a mode. Cycling back through -1 costs one branch
                // and needs no new drawn row.
                //
                // A FOURTH DRAWN ROW WAS THE OTHER OPTION AND IT DID NOT FIT when this
                // was written (rows then sat at 72/118/164 in an overlay treated as
                // 32..187). STALE SINCE 2026-08-24: rows now sit at 58/99/140 (41px
                // pitch, five power rows) and every overlay has been full-height since
                // #39 — a fourth row would fit today. The -1 cancel stays anyway: it
                // costs no row, and a cursor position that means "nothing" is still
                // the right shape for a menu that must never commit by accident.
                //
                // ⚠️ THE MENU EXISTS BECAUSE RECOVERY MUST NOT NEED THE TOUCHSCREEN.
                // GPIO0/BOOT is the entire hardware input budget, and `btn_rouse_touch`
                // is a row in the power menu for exactly that reason. A mode submenu
                // whose only button exit commits a mode change is a menu you cannot
                // back out of with a wedged touch controller. The 12s auto-dismiss is a
                // timeout, not an escape. Surfaced by check_navigability.py; JP's call.
                int s = id(ui_sel) + 1;
                id(ui_sel) = (s >= 3) ? -1 : s;
                id(ui_action) = 0;
              } else {
                // Advance the cursor. THE ROW COUNT DIFFERS PER MENU — the power menu
                // has ui_pm_n rows, the mode submenu has 3 (handled above) — so the
                // hardcoded modulus that used to be here walked the mode cursor onto a
                // fourth row that is never drawn. The tap hit-test would have refused to
                // apply it, so the symptom is a cursor that vanishes for one press
                // rather than an error: invisible in review, and only reachable from the
                // button path.
                id(ui_sel) = (id(ui_sel) + 1) % ${ui_pm_n};
                id(ui_action) = 0;
              }
              id(ui_gen)++;
          # cycle: TRUE only on this path. A single button cannot express two
          # directions, so it must wrap 100% -> 0% to be able to go down at all.
          # The on-screen -/+ below use cycle: false, where wrapping would be a bug.
          - if:
              condition:
                - lambda: 'return id(ui_action) == 2;'
              then:
                - number.increment:
                    id: spk_volume
                    cycle: true
                - lambda: 'id(ui_gen)++;'

    on_click:
      # ---- LONG: open the power menu, or activate the highlighted item ----
      - min_length: 900ms
        max_length: 6000ms
        then:
          - lambda: |-
              id(ui_last_ms) = millis();
              id(ui_action) = 0;
              if (id(ui_mode) >= 4) {
                // A long press inside the chronicle closes it outright — the
                // long press means "power menu" everywhere else, and opening a
                // menu ON TOP of the chronicle would need an overlay stack this
                // UI deliberately does not have. Close first, press again.
                id(ui_mode) = 0;
                id(force_full_repaint) = true;
              } else if (id(ui_mode) == 3) {
                // ⚠️ WITHOUT THIS BRANCH THE MODE SUBMENU IS UNREACHABLE FROM HARDWARE.
                // A long press with ui_mode == 3 fell through to the `else` below and
                // re-opened the POWER menu instead of picking a mode — so the mode
                // could only ever be changed by touch or from Home Assistant.
                //
                // That breaks the load-bearing reason these menus are on the button at
                // all: GPIO0/BOOT is the ENTIRE hardware input budget (K1/RESET is
                // hardwired to CHIP_PU and cannot be read), and the whole point is that
                // recovering the device must not require the touchscreen. A mode you
                // cannot leave without a working touch controller is precisely the trap
                // `btn_rouse_touch` exists to avoid.
                //
                // ui_sel == -1 still means dismiss, for the same reason as below: a
                // stray long press must not commit a choice nobody aimed at.
                id(ui_action) = (id(ui_sel) >= 0 && id(ui_sel) < 3) ? 10 : 4;
              } else if (id(ui_mode) == 2) {
                // Activate whatever the cursor is on. ui_sel == -1 (the initial
                // value) deliberately means "dismiss", so a stray long-press can
                // never fire a destructive item.
                switch (id(ui_sel)) {
                  case 0:  id(ui_action) = 5; break;   // mode submenu
                  case 1:  id(ui_action) = 6; break;   // bank
                  case 2:  id(ui_action) = 7; break;   // rouse
                  case 3:  id(ui_action) = 36; break;  // douse (deep sleep)
                  case 4:  id(ui_action) = 8; break;   // rekindle
                  default: id(ui_action) = 4; break;   // dismiss
                }
              } else {
                id(ui_mode) = 2;
                id(ui_sel) = -1;
              }
              id(ui_gen)++;
          - script.execute: ui_dispatch
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
