jphein/ember.realm.watch/enclosure/ember_case.py

"""
Ember voice-satellite enclosure  --  LCDWIKI/QDtech ES3C28P (Hosyond 2.8" ESP32-S3)
====================================================================================
Parametric source.  Run:  ../cadenv/bin/python ember_case.py
Outputs STLs + runs a boolean clearance check against the VENDOR STEP.

COORDINATE SYSTEM = the board's own frame, taken from ES3C28P_3D.step:
    X  0 .. 50      board width
    Y  0 .. 86      board length   (Y=0 is the USB-C / button end, Y=86 the mic end)
    Z               glass front face = +4.30 | PCB top = 0 | PCB bottom = -1.60
                    deepest back component = -6.30
Every board number below was MEASURED from the vendor STEP solid, not transcribed
from a datasheet table.  See VERIFIED{} for the provenance of each.
"""
from build123d import *
import os, sys, math

# PATH-INDEPENDENT IMPORTS. This file used a bare `import wyrm_spans`, which only resolved
# when cwd happened to be enclosure/tools/ — so `./cadenv/bin/python ember_case.py` from the
# enclosure directory died with ModuleNotFoundError, and the README's own build command did
# not work. "Buildable from a fresh clone" was a claim, not a fact. Resolve relative to THIS
# FILE instead of the working directory, so it runs from anywhere.
_HERE = os.path.dirname(os.path.abspath(__file__))
if os.path.join(_HERE, "tools") not in sys.path:
    sys.path.insert(0, os.path.join(_HERE, "tools"))
import wyrm_spans as _W

# ============================================================================
# 1. BOARD FACTS  -- all measured from ES3C28P_3D.step
# ============================================================================
BW, BL          = 50.00, 86.00      # PCB outline
PCB_TOP, PCB_BOT= 0.00, -1.60
GLASS_Z         = 4.30              # front face of the capacitive glass
BACK_MAX        = -6.30             # deepest back-side component
CORNER_R        = 3.50
HOLES           = [(4.0,4.0),(46.0,4.0),(4.0,82.0),(46.0,82.0)]   # d3.20, pad d5.60
GLASS_Y         = (8.40, 77.60)     # glass spans full 50mm width
VA              = (3.20, 46.80, 16.81, 74.86)   # visible area x0,x1,y0,y1
MIC             = (40.00, 81.50)    # mic package centre, in the top bare strip
MIC_HOLE_D      = 3.00              # back relief bore; the MIC label's keepout reads it
# ---- THE ONE ABSOLUTE BIT.  EVERYTHING ELSE ABOUT X IN THIS FILE IS RELATIVE. ----
#
# ⚠️ READ THIS BEFORE ADDING ANY "IS THE BOARD MIRRORED?" CHECK, because the obvious ones cannot
# work.  The alignment assert compares the board's bounding box to X 0..50 — and a mirrored
# board has the IDENTICAL bounding box, so that check is structurally incapable of failing.
# Less obviously, so is every RELATIVE claim: "BOOT shares its long edge with the microSD" is
# true in the mirrored world too, because mirroring moves both.  A relative predicate is
# mirror-invariant BY CONSTRUCTION.  You cannot detect a reflection from the model alone.
#
# So exactly one fact here is anchored to a PHYSICAL OBSERVATION and nothing else, and every
# relative assert in _check_geometry() hangs off it.  The relative ones then earn their place by
# catching a PARTIAL mirror — one feature moved without the others — which is the failure that
# actually happened (the switches were swapped relative to the socket).
#
# PROVENANCE: set from JP's physical board and the printed parts, 2026-07-30 — NOT from the
# vendor STEP and NOT from the outline drawing, both of which were read the wrong way round at
# least once each that day.  Corroborated afterwards by the STEP's own mic face at
# X 39.21..40.81, Y 80.15..82.85 -> centre (40.01, 81.50), which agrees to 0.01mm.
#
# ⚠️ Added after a mirror was SUSPECTED AND RULED OUT.  Nobody should later read this block as
# evidence that a reflection ever occurred — it did not.  It is here because the hole existed.
# If this constant is ever re-measured and comes back the other way, EVERY x in section 1
# mirrors, not just this line.
MIC_ON_HIGH_X   = True
USB_X           = (20.53, 29.47)    # USB-C body, centred on 25.00
USB_Z           = (-4.85, -1.60)
# ---- microSD SOCKET.  MEASURED FROM THE STEP'S *FACES*, NOT ITS SOLIDS. ----
#
# ⚠️ WHAT USED TO BE HERE WAS NOT THE SOCKET.  `SD_PLATE = (33.68,44.83,15.84,29.99)` was taken
# from the largest back-side SOLID in the vendor STEP: an 11.15 x 14.15mm plate standing 0.50mm
# off the PCB.  A microSD socket is 1.4-2.8mm tall, so 0.50mm was never a socket — it is a
# footprint placeholder, and JP, holding the board, identified it as the LCD driver flex.
#
# The real socket IS in the same STEP, authored as a stack of ZERO-THICKNESS FACES.  That is why
# a census of `.solids()` could not find it: it has no solid, no volume, and no height to filter
# on.  ⚠️ A SEARCH FOR THE WRONG KIND OF OBJECT RETURNS A CONFIDENT ABSENCE.  Searching
# `.faces()` instead gives four stacked rectangles:
#
#     X 2.53..17.53   Y 43.70..58.36   Z -1.60..-3.45      15.00 x 14.66 x 1.85mm
#
# 1.85mm tall — a real socket.  Corroborated independently by the vendor outline drawing, whose
# bottom dimension chain 11.82 + 15.97 + 35.03 closes exactly on Y=86 and puts the socket
# centreline at Y 50.955; the STEP faces give 51.03.  Two unrelated instruments, 0.3mm apart.
#
# The mouth faces the X=0 edge (the body stops 2.53mm short of it), so THE CARD TRAVELS
# PARALLEL TO THE PCB AND EXITS THROUGH THE SIDE.  The opening is therefore a side-wall slit,
# like the connector channels — not a hole in the back face.
#
# >>> THIS IS THE LANDMARK THE BUTTON ASSIGNMENT IS DERIVED FROM.  Do not edit it without
#     reading the block below. <<<
SD_SOCKET       = (2.53, 17.53, 43.70, 58.36)   # x0,x1,y0,y1
SD_SOCKET_Z     = (-3.45, -1.60)
SD_CARD_W       = 11.00              # microSD card width, across the direction of travel

# Rear-facing tact switches. WHICH IS WHICH — DERIVED FROM THE SOCKET, NOT TYPED, and the
# reason is the entire bug this block used to contain.  The vendor STEP carries designators for
# plenty of parts (C10, SD_CARD1, MOLEX1.25-…, the WS2812 library part) but contains NO K1/K2
# and no switch part at all — the same export suppression that hid the mic hole and the socket.
#
# JP's bench test, on the bare board: "volume button is on sd card side."  That observation was
# always correct.  ⚠️ WHAT WAS WRONG WAS THE LANDMARK IT WAS DECODED THROUGH.  The old comment
# reasoned "SD_PLATE spans x 33.68..44.83, i.e. high-x, so x = 36.58 -> BOOT" — and SD_PLATE was
# the LCD driver flex.  A correct physical fact, a correct inference, and a fictional anchor;
# the answer came out mirrored.  Read against the real socket at x 2.53..17.53 the same bench
# test gives the OPPOSITE assignment, which is what JP saw on the printed part.
#
# So it is COMPUTED now.  A comment has to be re-decoded by a human every time it is trusted,
# and this one was re-decoded wrongly.  Code is decoded once.
_SD_CX          = (SD_SOCKET[0] + SD_SOCKET[1]) / 2.0
_BTN_XS         = sorted(x for (x, _y) in [(13.45,3.26),(36.58,3.26)])
BTN             = [(13.45,3.26),(36.58,3.26)]
# the volume switch shares its long edge with the socket; the other switch is RESET.
BTN_BOOT_X      = _BTN_XS[0]  if _SD_CX < BW/2 else _BTN_XS[-1]   # big cap, the only readable switch
BTN_RESET_X     = _BTN_XS[-1] if _SD_CX < BW/2 else _BTN_XS[0]    # small cap
#
#   BOOT  = K2 / GPIO0  -- the ONLY readable input. Short press = volume overlay + step,
#           long press = power menu. Gets the BIG hex cap.
#   RESET = K1          -- hardwired to CHIP_PU, unreadable by firmware, reboots the MCU
#           *and* the LCD. Gets the SMALL hex cap.
#
# ⚠️ Holding BOOT low ACROSS a reset enters ROM download mode, which looks like a brick.
# With two pressable caps that is reachable by accident, so neither cap may be able to
# stick depressed, and one thumb must not span both.
#
# ⚠️ THE COST OF GETTING THIS BACKWARDS IS ASYMMETRIC, which is why it is derived and asserted
# rather than trusted: the generous thumb-sized cap over HARDWARE RESET is a device that reboots
# when you reach for the volume.  An easy RESET is an annoyance; a RESET you cannot avoid is not.
#
# >>> NEVER SPECIFY THESE AS "LEFT" OR "RIGHT". USE THE COORDINATES. <<<
#
# The apparent side flips between three figures of this same part:
#   case-back.svg          eye behind the part -> board +X appears on the viewer's LEFT
#                          (confirmed from the render: the mic at (40, 81.5) lands
#                          upper-left and the x=46 countersinks are the left-hand pair)
#   case-print-layout.svg  shell open-side-up -> mirrored back again, +X on the RIGHT
#   case-hero.png          a front view entirely
#   the VENDOR OUTLINE DRAWING (spec p.14) — the fourth figure, and the dangerous one,
#                          because it is the document someone checking this work will reach
#                          for first. It reads the OPPOSITE way to the bench test. An agent
#                          re-derived the assignment from it in good faith and got BOOT and
#                          RESET swapped, via a chain that was sound except for the handedness
#                          of a -90deg-rotated, 180deg-flipped figure — which cannot be
#                          established from the drawing itself. ⚠️ THE VENDOR DRAWING IS NOT
#                          USABLE TO RE-DERIVE THIS. The bench test wins because it anchors a
#                          physical observation to a model coordinate: JP pressed both, and
#                          the volume one is on the microSD side, and SD_PLATE is at x
#                          33.68..44.83 in the STEP. That is a landmark, not an orientation.
#
# So "big cap on the left" is true in one figure, false in another and meaningless in the
# third. Spec from the wrong one and the generous thumb-sized cap lands over the HARDWARE
# RESET — a device that reboots when you reach for the volume. Same discipline as the
# hostname rule in CLAUDE.md: the literal is the thing that silently goes stale, and a
# coordinate cannot be mirrored by a camera.
BTN_TIP_Z       = -4.10             # plunger tip (2.50mm below PCB back face)
PIP_D           = 3.00              # pip that reaches the plunger. WAS 4.00, and shrinking it
                                    # is what makes the offset island placeable: the island hex
                                    # narrows toward its bottom flat, exactly where the pip
                                    # sits, so a 4.00mm pip left only a 0.40mm window of legal
                                    # island X. 3.00mm more than doubles it to 0.98mm, and a
                                    # tact switch plunger is 1.5-3.5mm so 3.00 still covers it.
                                    # A 0.40mm placement window on a printed part with a 3.5mm
                                    # pip offset is not a tolerance, it is a hope.
LED             = (29.00, 45.60)    # WS2812B 5x5, on the BACK, fires rearward
ANT             = (17.57, 32.21, 80.04, 85.70)  # PCB antenna -- KEEPOUT, no metal
CONN_R         = [(32.54,40.19),(44.84,54.99),(62.69,72.84)]  # X=50 edge connectors
# X extent of the X=50 edge connectors, MEASURED off the STEP solids. Stored because the
# speaker relief (#33) needs it and nothing else in this file knew how far inboard they reach.
CONN_R_X       = (45.29, 49.49)
# >>> THE SPEAKER CONNECTOR IS TOP-ENTRY, AND IT IS THE ONLY ONE. <<<  (issue #33)
#
# JP, board and shell in hand: the speaker plug and its wires leave the board UPWARD into the
# shell, not sideways like every other connector, so the side-channel treatment is the wrong
# shape for it and the shell bears on the plug instead of closing.
#
# ⚠️ THAT OBSERVATION INDEPENDENTLY CONFIRMS THE #27 MAPPING, which is worth more than the
# relief it asks for. Measured out of the STEP, the five connectors are:
#
#     CONN_R[0]  z -6.30..-1.60  H 4.70   0.80mm to CAV_FLOOR   <- SPK, per the silkscreen
#     CONN_R[1]  z -5.00..-1.60  H 3.40   2.10mm
#     CONN_R[2]  z -5.00..-1.60  H 3.40   2.10mm
#     CONN_L[0]  z -5.00..-1.60  H 3.40   2.10mm
#     CONN_L[1]  z -5.00..-1.60  H 3.40   2.10mm
#
# EXACTLY ONE connector is taller than the others, it is 1.30mm taller, it reaches the board's
# own minimum Z, and it is the one the vendor silkscreen chain names SPEAKER. A physical
# observation ("the speaker one is different") and a documentary one (the drawing) agreeing on
# the same solid is the standard this file holds for handedness — see BTN_TIP_Z, where the
# bench test beat the drawing. There is an assert in __main__ that keeps them agreeing.
SPK_CONN_I     = 0                 # index into CONN_R. Derived-and-asserted, not chosen.
# ---- and the relief it needs. A THROUGH-OPENING, and the reasoning is a bound, not a guess ----
#
# The plug's height is the one number nobody has: it is JP's speaker's own pigtail and it is
# not in the STEP. So the choice was made on which failure is available rather than on a
# dimension I would have had to invent.
#
#   headroom today                                    0.80mm
#   a blind pocket, leaving 0.40mm of printable floor 0.80 + 2.20 = 3.00mm    <- BOUNDED
#   a through-opening                                 unbounded              <- cannot be short
#
# A 2-pin 1.25mm plug protrudes ~1.5-2.5mm past its header and its wires then need to turn.
# 3.00mm might do and might not, and "might" fails an acceptance test that reads "the shell
# closes fully". A through-opening cannot be too shallow, which is the whole argument.
#
# ⚠️ IT MUST REACH THE SIDE WALL, and that is the part a footprint-shaped hole would miss. The
# connector already fills the cavity to within 0.80mm, so the lead cannot travel over the top
# of it to the side channel — a 1mm wire in 0.80mm of gap is the pinched-wire hazard the stand's
# wire saddle exists to prevent, reintroduced 40mm away. Taking the opening outboard to OX1
# merges it with the existing side channel over the same Y span, so the plug drops in and the
# lead leaves sideways through a route that already exists.
SPK_RELIEF_CLR = 0.75              # per side, plug housing vs connector body
SPK_RELIEF_Y   = (CONN_R[SPK_CONN_I][0] - SPK_RELIEF_CLR,
                  CONN_R[SPK_CONN_I][1] + SPK_RELIEF_CLR)
SPK_RELIEF_X0  = CONN_R_X[0] - SPK_RELIEF_CLR
CONN_L         = [(21.07,25.32),(29.91,40.06)]                # X=0  edge connectors
CONN_R_EDGE_X  = BW      # the long edge CONN_R sits on
CONN_L_EDGE_X  = 0.0     # the long edge CONN_L sits on
# ⚠️ NOT THE MICROSD.  This is the 0.50mm-tall placeholder the old `SD_PLATE` name was attached
# to — the LCD driver flex, per JP.  It is kept ONLY as a keepout: it is the thing the phantom
# opening was exposing, so anything that cuts the X=BW wall must be checked against it.  The
# real socket is `SD_SOCKET`, 30mm away across the board and 28mm along it.
LCD_FLEX       = (33.68,44.83,15.84,29.99)

# ============================================================================
# 2. CASE PARAMETERS  -- tune these
# ============================================================================
FIT        = 0.35    # clearance per side, board edge -> pocket wall
WALL       = 2.60    # shell wall thickness
BEZEL_T    = 3.00    # bezel thickness over the glass
CAV_CLR    = 0.80    # clearance under the deepest back component
# ---- r5: THE TAP RAMP (2026-08-25, JP: "bezel need to be MUCH thinner/
# shorter so it's easier to tap the edges of the screen") ----
# The obstruction was never the face thickness alone — it was the CLIFF: a
# 0.40 GLASS_GAP + 3.00 face = 3.40mm wall standing 0.40mm from the active
# pixels, so a fingertip's contact centroid lands short of edge targets (the
# same physics that killed the tome button in firmware, 2026-08-09). BEZEL_T
# itself is load-bearing for the r4 deep deboss (>=2.00 must remain over the
# glass), so r5 keeps the face and kills the cliff two ways:
#   * WIN_MARGIN 0.40 -> 1.40: the window retreats 1.0mm from the pixels on
#     every edge, exposing inactive glass border instead of plastic. Bounded
#     by the glass's own top border (77.60 - 76.26 = 1.34mm coverage remains,
#     the thinnest edge) and policed by the boss-flare window asserts.
#   * A 45-degree TAP RAMP chamfered from the front face down to a
#     BEZEL_LIP_T rim at the window (see front_bezel), so the finger descends
#     a slope, not a wall: the cliff at the rim is 0.40 + 0.90 = 1.30mm
#     (was 3.40).
# The deboss field and the wyrm mark stay on full-thickness face only — the
# cell/mark keepouts grow by BEZEL_RAMP_W, so the >=2.00-over-glass assert
# keeps meaning what it says everywhere a deboss exists.
WIN_MARGIN = 1.40    # window oversize, ALL FOUR edges (r6; r5 was 3-edge, r4 was 0.40)
# r6 (2026-08-26): THE TOP-EDGE EXCEPTION IS RETIRED. r5 kept the top at r4
# geometry for two reasons; here is what retired each. (1) "The brow hosts the
# wyrm frieze, which cannot shrink" — still arithmetically true (min printable
# ink 11.25mm vs ~9.6mm of post-ramp brow), but JP's verdict on the printed r5
# (2026-08-25: "the top didn't get chamfered like the others. I need access to
# the top of the screen with my thumb too — you can move or resize the ember
# spirit") resolved the conflict the other way: the FRIEZE leaves, the ramp
# stays. The creature is not lost — it remains a solid island in the stand's
# grille and in the on-screen art ("one creature, three renderings" — now two
# on hardware). (2) "Firmware compensates the top targets" — compensation for
# a cliff is not access; a thumb still could not land there. The brow now
# carries the same honeycomb as the chin instead of a calm field for a mark
# that is no longer on it.
WIN_MARGIN_TOP = WIN_MARGIN   # r6: the top is no longer special (was 0.40)
BEZEL_LIP_T  = 0.90  # face thickness AT the window rim — the min-feature floor
BEZEL_RAMP_W = BEZEL_T - BEZEL_LIP_T   # 2.10; drop == width -> exactly 45 deg
BOSS_D     = 5.40    # <= 5.60 pad diameter, per the vendor keepout
PILOT_D    = 2.50    # M3 self-tapper pilot
SCREW_D    = 3.30    # M3 shank clearance through the shell
# ---- COUNTERBORE, SIZED TO A MEASURED HEAD ----
#
# JP's screws are SOCKET CAP with a hex recess, so the head is a CYLINDER. This is a
# flat-bottomed counterbore, not a cone.
#
# HISTORY, in one line, because it explains why this used to be forty: it was a 90deg conical
# countersink with a long derivation about included angles, DIN 965 versus ISO 10642 heads, and
# why fixing the angle without also fixing the mouth diameter still leaves the head bearing on
# its rim. All of it solved for a conical seat this fastener does not have. It is DELETED rather
# than adapted — a comment explaining a 90deg cone sitting next to a counterbore is precisely the
# stale-rationale failure this repo keeps logging.
#
# A counterbore is also the more forgiving feature, which is worth knowing before anyone
# "improves" it back: a flat floor seats a cylindrical head on its FULL ANNULAR UNDERSIDE
# regardless of small diameter errors, where a cone punishes any angle mismatch by concentrating
# the load on a line. And a flat floor at a layer boundary is exactly what an FDM printer makes
# well, so the staircase-of-annular-steps problem the cone had disappears.
#
# ⚠️ EVERY NUMBER IN THE FASTENER CHAIN IS MEASURED. Calipered by JP on the actual screws,
# 2026-07-30. The ISO 4762 table agrees with both figures, but the table is not the source — this
# is the only part of this design where no input is nominal, and that is worth preserving. If a
# screw ever does not fit, no assumption is hiding in here.
SCREW_SPEC      = "M3 x 0.5 x 12 ISO 4762 socket cap, hex recess"
SCREW_HEAD_D    = 5.50   # MEASURED, JP, 2026-07-30
SCREW_HEAD_H    = 3.00   # MEASURED, JP, 2026-07-30
SCREW_LEN       = 12.00  # UNDER-HEAD length, which is how ISO 4762 is dimensioned. ⚠️ A
                         # countersunk screw's stated length INCLUDES its head; a socket cap's
                         # does not. That difference is why a 12mm cap out-performs the 14mm
                         # countersunk this used to specify.
# ============================================================================
# LAYER HEIGHT IS PER-PART.  IT IS NOT ONE NUMBER, AND TREATING IT AS ONE WAS ISSUE #26.
# ============================================================================
#
# ⚠️ THIS WAS A SINGLE `LAYER_H = 0.16` COMMENTED "PRINT-SHEET's layer height for the shell
# parts", AND THAT COMMENT WAS FALSE. PRINT-SHEET's settings table is FOUR COLUMNS —
# bezel / shell / stand / base — and reads 0.16 for the BEZEL and 0.20 for the other three. The
# 0.16 was the bezel's value, borrowed by the shell and relabelled as the shell's on the way.
#
# It was load-bearing in both directions at once, which is why it survived: `BEZEL_DEBOSS`
# consumed it and was CORRECT, while `CBORE_DEPTH` and `LABEL_DEBOSS` consumed the same constant
# and were wrong for a shell sliced at 0.20 — 15.2 and 2.4 layers, both mid-layer floors. The
# claims "19 layers exactly" and "3 layers at 0.16" were true of the number and false of the part.
#
# ⚠️ AND THE ISSUE UNDERSTATED IT. Auditing every Z depth against BOTH candidates found three more
# mid-layer floors, and unlike the two above these are misaligned at EVERY layer height in play:
#
#     DEBOSS_BIG    0.90   5.625 layers @0.16   4.5 layers @0.20
#     DEBOSS_SMALL  0.50   3.125               2.5
#     HINGE_T       0.90   5.625               4.5
#
# So the real defect was never "one constant borrowed the wrong value". It was that Z depths were
# never checked against ANY layer height, and two of them happened to divide 0.16 — which is what
# made the other three invisible. `HINGE_T` is the serious one: it is the strain-critical
# dimension (`strain = (t/2)*theta/L`), computed to three significant figures throughout this
# file, and the slicer was picking its actual value.
LAYER_H_BEZEL   = 0.16   # PRINT-SHEET: the bezel alone. Its front face is the one you look at and
                         # its mic bore is only d2.40, which starts to close up at 0.20.
LAYER_H_SHELL   = 0.20   # PRINT-SHEET: shell, stand and base. ⚠️ The bezel's reasons DO NOT apply
                         # here — the shell's fine features (the 0.60 button moat, the 0.80 hex
                         # webs, the 0.90 label grooves) are all VERTICAL walls, and layer height
                         # does not govern the width of a vertical wall.
CBORE_CLR       = 0.30   # diametral clearance, 0.15 a side
CBORE_D         = SCREW_HEAD_D + CBORE_CLR              # 5.80
# DEPTH IS A WHOLE NUMBER OF LAYERS, AND AT 0.20 IT IS EXACTLY FLUSH.
# The measured head is 3.00 and 3.00 / 0.20 = 15 exactly, so the head sits DEAD FLUSH with no
# rounding at all. ⚠️ This retires a compromise rather than adding one: at the borrowed 0.16 the
# head was 18.75 layers, 18 left it 0.12 PROUD (which stops the part sitting flat and stops the
# screw clamping) and 19 sank it 0.04 to avoid that. The fudge existed only because the shell was
# being sliced at the bezel's layer height. Correcting #26 deletes it.
CBORE_DEPTH     = 15 * LAYER_H_SHELL                    # 3.00 — exactly the head height
# ---- BOSS FLARE.  THIS EXISTS BECAUSE THE HEAD IS 3.00mm TALL.  DO NOT REMOVE IT. ----
#
# A flush 3.04mm pocket floors at z -6.66, which is 0.44mm PAST CAV_FLOOR — out of the solid back
# slab and into the cavity, where the only material is the screw boss. At BOSS_D = 5.40 the
# CBORE_D = 5.80 bore is WIDER THAN THE THING IT IS CUTTING, so it removes the boss root and
# leaves the head nothing to bear on. ⚠️ A POCKET DEEPER THAN THE SLAB IT IS CUT INTO STOPS BEING
# A POCKET. Nothing else in this file could have caught that: every other check compares the PART
# to the BOARD, and this is the part disagreeing with itself.
#
# ⚠️ THE PERMISSION FOR THE FLARE IS A DISTINCTION, NOT A LICENCE: the vendor's d5.60 pad keepout
# applies AT THE PCB FACE, not below it. So the boss stays 5.40 where it touches the board and
# widens only underneath, in free space. Anyone "restoring" it to a uniform 5.40 to match the
# keepout comment will silently delete the head's seat.
#
# Bounded above by the button slots, not by taste. The slots pass within 9.49mm (RESET) and
# 12.38mm (BOOT) of a boss centre — the hex has NARROWED by the time it reaches the boss's y, so
# the naive x-extent overstates the conflict. 8.40 clears the tighter one by 1.09mm.
BOSS_FLARE_D    = 8.40   # boss diameter at CAV_FLOOR, tapering to BOSS_D at the PCB face
BOSS_MIN_ANN    = 1.00   # minimum annular bearing width under the head, at the bore floor

# ---- BEZEL BOSS FLARE. THE SHIPPED BOSSES SNAP OFF. (JP, bench, 2026-08-06) ----
#
# The bezel's four mounting bosses were a STRAIGHT d5.40 tube, 4.70mm tall
# (PCB_TOP 0.00 -> SEAM_Z 4.70) with a d2.50 pilot through it — a 1.45mm annular
# wall, which is 3.6 extrusions at a 0.40 nozzle — meeting the bezel slab at a
# sharp 90 degree corner. Three things compound there and all three point the
# same way:
#
#   * A cylinder into a plane is a stress riser with no radius to spread load.
#   * The bezel prints FRONT FACE DOWN, so the boss axis is the BUILD axis and
#     every layer line runs perpendicular to it. Prying a boss loads the root in
#     pure layer adhesion, which is the weakest direction FDM has.
#   * It is a cantilever whose whole job is to be torqued by an M3 self-tapper.
#
# The shell's bosses have had a flare since the head-height work and the note
# above says DO NOT REMOVE IT. The bezel simply never got the equivalent. This is
# that, mirrored: widest where it joins the slab, tapering to BOSS_D exactly at
# the PCB face so the d5.60 vendor pad keepout still governs the contact end.
#
# 8.40 IS NOT A NEW MAGIC NUMBER — it is BOSS_FLARE_D, reused deliberately so the
# two halves of the same joint flare to the same diameter. Clearances at all four
# holes, derived not eyeballed: 2.75mm of wall to the outer silhouette
# (OX0/OY0 -2.95, OX1 52.95, OY1 88.95) and 2.54mm to the screen window at the
# brow pair, whose y-gap of 6.74mm (82.00 -> win y1 75.26) is the tightest of the
# four. The chin pair has 8.21mm.
#
# ⚠️ IT IS A SEPARATE CONSTANT FROM BOSS_D ON PURPOSE, AND THAT IS LOAD-BEARING.
# The front-face hex keepout tests `hypot(...) < BOSS_D/2 + BEZ_MARGIN + R`
# (_bezel_cells), so widening BOSS_D would shrink the cell field and could trip
# the chin>=50 / rails>=20 asserts — which this file warns must never be lowered
# to make a build pass. The flare lives entirely on the CAVITY side, below the
# slab, so it adds material under the debossed face and changes no cell count.
#
# It is also strictly BETTER to print than what it replaces: front-face-down puts
# the root at 3.00mm of build height and the tip at 7.70mm, so the cone is wide at
# the bottom and narrows going up — a tapering tower, 17.7 degrees off vertical,
# no overhang anywhere.
BEZEL_BOSS_FLARE_D = BOSS_FLARE_D   # 8.40 at SEAM_Z, tapering to BOSS_D at PCB_TOP
# ⚠️ AND THE BINDING CONSTRAINT IS NO LONGER THE ONE EVERYONE REACHES FOR. The wall from a screw
# hole to the outer corner arc was 2.533mm with the old d6.42 cone mouth and is 2.843mm with this
# d5.80 bore — the counterbore is LESS binding there, because a socket cap head (5.50) is smaller
# than the countersunk head (6.00) whose 90deg cone needed a 6.42 mouth. The arc was the right
# worry for the cone and is the wrong worry for this. Depth against the 2.60mm wall is what bites.
# ---- HEXAGONAL BUTTON CAPS ----
# The pads were rectangles. JP: "i wanted the buttons to be hexagons not squares" — and
# they should be, since every other aperture on this case is a hex cell.
#
# FLAT-TOP, NOT POINTY-TOP, AND THIS IS STRUCTURAL RATHER THAN AESTHETIC. The rest of the
# case uses `RegularPolygon(R, 6, rotation=30)` (pointy-top) because that is the honeycomb
# pitch. A button cannot: the pad is a living hinge, so it must stay attached along its +Y
# edge, and a pointy-top hex has a VERTEX at +Y. Hinging on a point gives a hinge of zero
# width, which is not a hinge — it is a tear. Flat-top puts a full edge of length R at +Y.
# So the caps are the one place in the case where the hexes are rotated 30 degrees from the
# lattice, and the reason is that a hinge needs a hem.
#
# The envelope is not free: the island's bottom edge cannot go below y=0.80 (the shell's
# bottom wall is just outside the board edge and the switches sit only 3.26mm in), and the
# slot's OUTER boundary must clear the fine hex field at HEX_FIELD_Y0 (19.00; this comment
# said 11.0, the value before the field yielded to the thumb-sized caps). A flat-top hex of
# circumradius R spans R*sqrt(3) in Y, so R is pinned by those two facts, not chosen.
# THUMB-SIZED, AND IT IS A STRENGTH FIX AS WELL AS JP'S REQUEST. JP asked for "big
# thumbsized hexagons" and 9.01mm across flats is not one — a thumb pad is 15-20mm. But the
# decisive argument is strain: at the old 9.01mm cap the hinge sat 6.55mm from the pip, giving
# 3.50deg and 2.29% at L=1.20 — over PLA's ~2% YIELD, safe only against fracture. A bigger hex
# puts the hinge further from the pip, so theta falls and strain falls with it. At 15mm the pip
# arm is 12.54mm, theta 1.83deg, strain 1.20%. The cap that JP wanted is also the cap that
# stops the hinge creeping, which is the rare case where the ergonomic and the mechanical
# answer are the same number.
BTN_R_BIG   = 8.6603  # BOOT/volume. 17.32 across corners, 15.00 across flats.
BTN_R_SMALL = 5.7735  # RESET. "it can be smaller hexagon" — 11.55 corners, 10.00 flats.
# ISLAND CENTRES ARE OFFSET FROM THE SWITCHES, and the screw heads force it. The M3 heads at
# (4,4) and (46,4) open to HEAD_MOUTH_D at the outer face. A 17.32mm-wide island centred on the
# switch at 36.58 would span 27.92..45.24 and eat into the high-x one. Shifting the ISLAND
# inboard is free because the hinge line runs across X and the PIP stays on the switch — only
# the decorative hex moves.
#
# ⚠️ THESE WERE TWO HAND-TYPED NUMBERS WHOSE JUSTIFICATION THE FILE DID NOT COMPUTE, and that
# made them a trap in two directions at once. The switches swapped sides (see the BTN block) and
# the screw recess changed shape — either alone silently invalidates a literal, and nothing here
# would have objected. So they are SOLVED from the clearance that motivated them:
#
#   * the binding dimension is the SLOT's outer edge, not the island's: the ring cut reaches
#     R + SLOT_W, and that is what can break into the head recess.
#   * ISLAND_SLOT_CLR reproduces the shipped BOOT island to 0.01mm (33.04 solved vs 33.05
#     typed), which is the case the original comment names as the forcing one. The shipped RESET
#     island was 0.44mm more generous than the rule; it was never the binding side.
SLOT_W          = 0.60   # printed-in-place slot around the button pads. Declared HERE because
                         # the island solve below needs it — it used to sit 70 lines further on.
PAD_Y0          = 0.80   # island bottom edge. Any lower cuts the shell's bottom wall. Declared
                         # HERE because _island_cx() needs it — it used to sit below the islands.
def _cap_cy(R):
    """Island/cap centre y for a cap of circumradius R. THE single derivation.

    ⚠️ Extracted because two places now need it and this file has already been bitten once by
    exactly that: HEX_FIELD_Y0 exists because _hex_panel() moved to 19.00 while the assert
    checking it still read a hardcoded 11.0, so the assert fired against a boundary the part no
    longer had. cap_geometry() and _island_cx() must not each carry their own copy of this."""
    return PAD_Y0 + R*math.sqrt(3)/2
ISLAND_SLOT_CLR = 0.49   # wall between the slot and the d5.80 counterbore bore
FLARE_SLOT_CLR  = 0.80   # wall between the slot and the d8.40 boss flare. Larger because this
                         # one is a load path — the boss carries the screw — where the bore wall
                         # is only cosmetic. Two extrusions at a 0.4 nozzle.
def _island_cx(cx, R):
    """Island centre for a cap of circumradius R whose switch is at x=cx.

    Returns cx unchanged when nothing is in the way, otherwise the nearest position that clears
    BOTH obstructions near each screw hole. Leaving it concentric is always preferred: the pip
    stays on the switch while only the decorative hex moves, and the hex narrows toward its bottom
    flat exactly where the pip sits, so the legal offset window is under 1mm wide.

    ⚠️ THE TWO OBSTRUCTIONS ARE DIFFERENT SHAPES AT DIFFERENT DEPTHS AND A SINGLE max() IS WRONG.
    The slot is cut from BACK_Z-1 up to CAV_FLOOR+1, so it passes BOTH:

      * the d5.80 counterbore bore, deep in the back slab, at the slot's full circumradius;
      * the d8.40 boss flare, up in the cavity — WIDER, but the slot has NARROWED by the time it
        reaches the boss's y, because a flat-top hex loses 1/sqrt(3) of half-width per unit of y
        away from its own centre. The boss sits at y=4.0 and the big cap's hex centres at y=8.30,
        so 4.30mm of narrowing turns a 9.26 half-width into 6.78.

    Taking max(bore, flare) against the naive x-extent — my first attempt — pushed the big island
    to 17.95, an offset of 4.50 from its switch, which is outside that sub-millimetre pip window:
    it would have moved the pip off the island entirely to dodge a collision that the narrowing
    means does not happen. AN OVER-CONSERVATIVE CONSTRAINT IS STILL A WRONG ONE."""
    reach = R + SLOT_W                                    # slot circumradius (its widest)
    cyh   = _cap_cy(R)
    narrow = max(0.0, reach - abs(HOLES[0][1] - cyh)/math.sqrt(3))   # half-width at the boss's y
    _b = []
    for hx in (HOLES[0][0], HOLES[1][0]):
        _b.append((hx, CBORE_D/2      + ISLAND_SLOT_CLR + reach))
        _b.append((hx, BOSS_FLARE_D/2 + FLARE_SLOT_CLR  + narrow))
    lo = max(hx + k for (hx, k) in _b if hx < BW/2)
    hi = min(hx - k for (hx, k) in _b if hx > BW/2)
    # ⚠️ ROUND AWAY FROM THE RECESS, NOT TO NEAREST. This line was `round(..., 2)` and the
    # assert in _check_geometry() 0g caught it on the first build: the solve wanted 16.9603 and
    # round-to-nearest tidied it to 16.96, SPENDING 0.0003mm of the clearance it had just
    # computed. The number was wrong by three ten-thousandths of a millimetre and it was still a
    # real violation, because a value sitting ON a constraint boundary has no slack to round
    # into. Whenever a rounded number IS a clearance, the direction of the rounding is part of
    # the constraint. Kept at 2dp because these are read by humans in renders and sheets.
    if cx < lo: return math.ceil(lo * 100) / 100
    if cx > hi: return math.floor(hi * 100) / 100
    return cx
CAP_CX_BOOT  = _island_cx(BTN_BOOT_X,  BTN_R_BIG)    # island centre; switch at BTN_BOOT_X
CAP_CX_RESET = _island_cx(BTN_RESET_X, BTN_R_SMALL)  # island centre; switch at BTN_RESET_X
# PAD_Y0 moved UP to the island-solve block -- _island_cx() needs it. A second
# definition here would shadow it and the two cy derivations would silently diverge.
# The back hex field's lower boundary, NAMED because two places need it and they disagreed:
# _hex_panel() was moved to 19.00 for the thumb-sized caps while the assert that checks the
# caps clear the field still read a hardcoded 11.0 — so the assert fired against a boundary
# the part no longer had. Exactly the dead-GRILLE_SLOT_W hazard one screenful up, and the
# reason a shared number gets a name.
HEX_FIELD_Y0 = 19.00
# X0/X1/Y1 hoisted out of the _hex_panel() call below at the same time the back-face labels
# went in. They were literals with ONE consumer, which was fine; the labels make them literals
# with TWO, which is exactly the shape that produced the dead SD_PLATE and the dead
# GRILLE_SLOT_W. Naming them is cheaper than re-learning it a third time.
HEX_FIELD_X0 = 9.00
HEX_FIELD_X1 = 41.00
HEX_FIELD_Y1 = 75.00
# DEBOSSED, NOT RAISED — and the print orientation decides this, not taste.
#
# The first version of these caps stood 1.20mm PROUD of the back face, because JP asked for
# "big beautiful tactile buttons you can feel" and a boss is the obvious reading of that.
# It cannot work: PRINT-SHEET.md prints this part BACK FACE DOWN with no supports, so a
# proud cap is the LOWEST feature on the part. A 55 x 92mm shell would balance on two
# hexagons totalling ~74mm2 with the whole back face 1.20mm in the air. The bbox even
# confirmed it — the part grew from 14.40 to 15.60mm deep, exactly the cap height, which is
# how the boss was caught. Raised features on a bed face are self-defeating; recessed ones
# are free, because a few layers bridge over an 8mm void and nothing else changes. It is the
# same reason the front bezel's debossed hexes print in ITS bed-face orientation.
#
# A debossed hexagon with a crisp rim, plus the 0.60mm slot moat around the island, is
# genuinely findable — a fingertip resolves steps two orders of magnitude smaller than this.
# It also matches the debossed hexagons JP asked for on the bezel, so the two faces speak
# the same language rather than one embossing and the other engraving.
#
# AND IT REMOVES A HAZARD RATHER THAN MITIGATING ONE. Holding BOOT low across a reset enters
# ROM download mode, which presents as a brick. Proud caps make that reachable by anything
# resting on the case; recessed ones cannot be pressed by a flat object at all. The unequal
# DEPTHS still give a thumb two independent discriminators in the dark — size and depth — on
# a case that carries no lettering.
# ⚠️ WERE 0.90 / 0.50, AND NEITHER WAS A WHOLE NUMBER OF LAYERS AT ANY LAYER HEIGHT THIS PROJECT
# USES — 5.625 / 3.125 at 0.16 and 4.5 / 2.5 at 0.20. Both recess floors landed mid-layer, on the
# visible back face, and issue #26 did not name either of them: it named the two constants that
# happened to divide 0.16. These are now 4 and 2 layers of the SHELL's own height.
# THE DIFFERENTIAL IS WHAT MATTERS AND IT IS PRESERVED EXACTLY. 0.90-0.50 and 0.80-0.40 are both
# 0.40mm, so the "two independent discriminators in the dark — size and depth" property is
# untouched; only the absolute depths moved, and both got shallower by the same amount.
#
# ⚠️ THE CAP FACE IS FLAT SINCE r11 — THESE NO LONGER CUT A FACE RECESS. The printed r10
# killed it (JP, 2026-08-02: "don't indent the buttons. it doesn't work it's taoo far to
# span"): face-down on the bed, the recess floor is a 13.3mm-wide bed-side bridge across the
# big cap, and it sagged. The constants survive because they were always doing a second job:
# each cap's LABEL cuts DEBOSS_* + LABEL_DEBOSS deep, so the big cap keeps its 1.20mm VOL —
# "the deep deboss of the button lables is a good tactile hint" (same bench) — with no bridge
# anywhere. The 0.40 depth differential between the caps now lives entirely in the labels.
DEBOSS_BIG   = 4 * LAYER_H_SHELL   # 0.80  extra label depth, BOOT/volume — the one you reach for
DEBOSS_SMALL = 2 * LAYER_H_SHELL   # 0.40  extra label depth, RESET, deliberately shyer
CAP_INSET  = 1.00    # the label-safe zone is a hex of R - this. It was also the face-recess
                     # inset; the labels' fit asserts still key on it, so it stays.
# ⚠️ WAS 0.90, WHICH IS 5.625 LAYERS AT 0.16 AND 4.5 AT 0.20 — MID-LAYER AT BOTH. This is the
# STRAIN-CRITICAL dimension: `strain = (t/2)*theta/L` is computed to three significant figures
# throughout this file and asserted at <=2.0%, and t was whatever the slicer rounded 0.90 to. A
# precise calculation on a dimension nobody controlled. 0.90 -> 1.00 would have raised strain 11%
# against an assert that never knew.
# 0.80 IS CHOSEN OVER 1.00 FOR TWO REASONS. It is 4 layers at 0.20 AND 5 layers at 0.16, so it
# stays aligned whichever way the PRINT-SHEET table lands — the only value in this block that is
# robust to that decision. And it moves strain DOWN ~11% (t scales it linearly), which is the safe
# direction on a flexure whose failure mode is cracking. ⚠️ It also softens the press slightly;
# 1.00 would firm it up at +11% strain, still inside the 2.0% limit. That is a FEEL choice and
# therefore JP's — see the report on issue #26.
HINGE_T    = 4 * LAYER_H_SHELL   # 0.80  living-hinge thickness
# FLEXURE LENGTH IS PER-BUTTON, AND IT IS A STRENGTH FIX, NOT A FEEL ONE.
#
# The hinge rotation is not a free variable: theta = pip travel / the pip's distance from the
# hinge. The SMALLER cap has the LARGER angle, because its pip sits on a shorter arm — 5.6deg
# on RESET against 3.5deg on BOOT. Bending strain is (t/2)*theta/L, so at a shared 1.0mm
# flexure the small button was the one being over-strained:
#
#   BOOT   t=0.90  L=1.0  ->  2.75%
#   RESET  t=0.90  L=1.0  ->  4.37%   past PLA's ~2% yield, into its 4-6% break band
#
# A teammate, reasoning about FEEL rather than strength, proposed thickening RESET's hinge to
# 1.40mm — correctly observing that with equal thickness the smaller hex always presses
# lighter, which is backwards from "deliberately shyer under the finger". But strain scales
# with t, so that fix takes RESET to 6.79% and cracks the hinge on the bench. The feel defect
# is real and the proposed cure destroys the part.
#
# Lengthening the flexure fixes what actually breaks and costs nothing. ⚠️ THE SHIPPED PAIR IS
# 2.29% (BOOT) AND 2.18% (RESET) — an earlier version of this comment said "2.18% and 1.37%",
# and 1.37% is BOOT at L = 2.00, a flexure length BOOT does not have. Both figures were real
# and one of them described a configuration that was never built. Same discipline the firmware
# side arrived at independently: state which configuration you RAN, not which conclusion you
# reached. Both pass the 2.0% assert (`_strain <= 0.020`; this line said 2.5%), so nothing was
# broken — which is exactly why it survived.
# The
# force ordering stays mildly inverted, and that is the right trade — an easy RESET is an
# annoyance, a cracked RESET hinge is a dead part, and RESET is the recoverable button anyway.
# Findability is already differentiated by size and deboss depth, which cost no strain at all.
HINGE_L_BOOT  = 1.20
HINGE_L_RESET = 2.00
# SLOT_W moved UP to the island-solve block — `_island_cx()` needs it. A second definition here
# would shadow it and the islands would silently solve against a stale width.
# LED_WIN_D / DIFF_D deleted with the rear glow window and the diffuser disc. The fine
# hex field on the back now carries the WS2812's light, and JP is printing in WHITE — a
# translucent shell, so the glow leaves through the wall as well as the holes. Many small
# apertures in a translucent panel scatter; one 12mm bore behind a printed disc just shows
# you the die.

GLASS_GAP  = 0.40    # bezel NEVER touches the glass: LCD 2.3+/-0.1 & TP 1.0+/-0.1
                     # stack up to +0.2, so 0.40 keeps 0.2 clear worst-case.
SEAM_Z     = GLASS_Z + GLASS_GAP             # +4.70  shell wall top = bezel underside
CAV_FLOOR  = BACK_MAX - CAV_CLR              # -7.10
FRONT_Z    = SEAM_Z + BEZEL_T                # +7.70
BACK_Z     = CAV_FLOOR - WALL                # -9.70
OX0, OX1   = -(FIT+WALL), BW+FIT+WALL        # -2.95 .. 52.95   (55.90 wide)
OY0, OY1   = -(FIT+WALL), BL+FIT+WALL        # -2.95 .. 88.95   (91.90 tall)
OUT_R      = CORNER_R + FIT + WALL           # 6.45
PK0, PK1   = -FIT, BW+FIT
PY0, PY1   = -FIT, BL+FIT
POCK_R     = CORNER_R + FIT

# ============================================================================
# 3. helpers
# ============================================================================
def bx(x0,x1,y0,y1,z0,z1):
    return Pos(x0,y0,z0) * Box(x1-x0, y1-y0, z1-z0,
                               align=(Align.MIN,Align.MIN,Align.MIN))

def rbox(x0,x1,y0,y1,z0,z1,r):
    sk = RectangleRounded(x1-x0, y1-y0, r)
    return Pos((x0+x1)/2,(y0+y1)/2,z0) * extrude(sk, z1-z0)

def rrect_y(cx, cz, w, h, r, y0, depth):
    """Rounded rectangle in the XZ plane, extruded along +Y.

    Same trick as the Cylinder seat it replaces: build the profile in XY, extrude in
    +Z, then Rot(-90,0,0) maps +Z onto +Y so the prism drives through the front wall.
    """
    sk = RectangleRounded(w, h, r)
    return Pos(cx, y0, cz) * (Rot(-90,0,0) * extrude(sk, depth))

def cyl_y(cx, cz, d, y0, depth):
    """Cylinder along +Y — rrect_y's round sibling, same Rot(-90,0,0) mapping. Exists for
    the braille dots: RectangleRounded rejects r == w/2, so a true circle needs its own."""
    return Pos(cx, y0, cz) * (Rot(-90,0,0) * extrude(Circle(d/2), depth))


def chamfer_outline(part, z, size, what):
    """45deg chamfer on the EXTERIOR PERIMETER edges lying in the plane z.  Issue #35.

    Generic on purpose: the bezel is owned by another agent right now, and when its front
    perimeter wants the same treatment it should be one call with the same constant rather
    than a second implementation that drifts from this one.

    >>> THE SELECTOR IS "IN THE PLANE **AND** TOUCHING THE PART'S OWN SILHOUETTE". <<<
    The back face at z=BACK_Z also carries nine label grooves, 113 hex apertures, four
    counterbores, the SD slit and the speaker relief — every one of them has edges in that
    plane, and chamfering the lot would be a catastrophe dressed as a one-liner. An edge
    qualifies only if it ALSO reaches an extreme of the part's own bounding box, which the
    outline does by definition and no interior feature does.

    45deg chamfer, not a roundover, and that is an FDM decision rather than a style one: a
    roundover's lower quadrant is an overhang into the bed and prints ragged on a face-down
    part, while a chamfer is self-supporting in every orientation this project uses.
    """
    bb = part.bounding_box()
    sel = []
    for e in part.edges():
        eb = e.bounding_box()
        if abs(eb.min.Z - z) > 1e-6 or abs(eb.max.Z - z) > 1e-6:
            continue
        if (eb.max.X > bb.max.X - 1e-6 or eb.min.X < bb.min.X + 1e-6
                or eb.max.Y > bb.max.Y - 1e-6 or eb.min.Y < bb.min.Y + 1e-6):
            sel.append(e)
    assert sel, (
        f"{what}: no perimeter edge found in the plane z={z:.3f}. The selector has drifted, "
        f"and a chamfer that selects nothing is SILENTLY ABSENT — which is exactly how #38's "
        f"gable hid through three builds")
    return chamfer(sel, length=size)


def cyl(x,y,z0,z1,d):
    return Pos(x,y,z0) * Cylinder(d/2, z1-z0,
                                  align=(Align.CENTER,Align.CENTER,Align.MIN))

# ---- BEZEL FACE: debossed honeycomb + the hearth-wyrm mark ----
# JP: "we should debossed hexagons on the front of the front bezel with the ember logo on the
# top left", then, on seeing the hero render: "the case hero i just was shown doesn't have the
# debossed hexagons on the front bezel — or the logo". Correct, and the figure was being
# honest: this was designed, discussed at length, and never wired into front_bezel(). A
# decision recorded only in conversation is not in the part.
#
# EVERYTHING HERE IS A RECESS, AND THAT IS FORCED. The bezel prints FRONT FACE DOWN on the
# bed, so any raised feature on this face becomes the lowest point of the part and the bezel
# lands on its own logo. Same trap that killed the raised button caps on the back shell, in
# the same session, on the opposite face — which is the tell that it is a property of the
# process rather than a one-off mistake: on a bed face, relief only goes inward.
BEZEL_DEBOSS = 6 * LAYER_H_BEZEL  # every debossed feature on the front face. EXACTLY 6 layers at
                      # 0.16mm PRINT-SHEET specifies for this part. It was 0.45, which is
                      # 2.8125 layers — the recess floor landed mid-layer and the comment
                      # claimed "3 layers at 0.15", a layer height this part does not use. Two
                      # reviewers flagged it independently. The slicer would have rounded it
                      # harmlessly, but a depth that is an exact multiple means the floor is a
                      # real layer boundary rather than wherever the rounding fell.
                      # ⚠️ 3 LAYERS (0.48) DID NOT READ. JP printed that bezel and asked for the
                      # wyrm, the side hexes and the bottom hex field all deeper (#34) — size
                      # unchanged, `BEZ_AFLAT` 2.60 stays, and the issue's own title said
                      # "bigger bottom hexes" before the body retracted it. Depth only, and
                      # global, because every region moved together.
                      # ⚠️ 5 LAYERS (0.80) READ, AND JP STILL WANTED MORE. Verdict on the
                      # printed r2 (2026-08-01, #48): "it's good but go even deeper next time
                      # pls." So 6 layers, and 6 IS TERMINAL: it leaves 2.04mm over the glass
                      # against the >=2.00 assert below, so there is no 7th step — going deeper
                      # than 0.96 means revisiting the glass floor itself, which is a design
                      # conversation and not an edit to this constant (#48's own framing).
                      # THE FLOOR THIS LEAVES IS MEASURED, NOT ASSUMED. Ray-cast on a 0.4mm grid
                      # over the exported bezel (first done at 0.48 — 3899 of 3901 debossed
                      # sample points on exactly 2.520mm of web; re-run at 0.96 for #48,
                      # 2026-08-25 — 3880 of 3880 on exactly 2.040mm), with NO back-side
                      # thinning anywhere. The four screw pilots DO reach up into the slab (to
                      # SEAM_Z+1.5, leaving only 1.50mm there) but every debossed region is held
                      # off them — the hex field by a BOSS_D/2 + BEZ_MARGIN + R keepout (the
                      # wyrm frieze, r6-deleted, kept its own margin). So the binding
                      # number really is the nominal one: 6 layers leaves 2.04mm, clearing the
                      # 2.00 assert below by 0.04. The shell already runs DEBOSS_BIG = 0.80 on
                      # a 2.60 wall and keeps far less than this.
BEZ_AFLAT    = 2.60   # hex across flats. Finer than the back's 3.20 — this face is read
                      # from arm's length, and the brow is only 13.69mm tall.
BEZ_WEB      = 0.70   # material between cells. ⚠️ NOT "two extrusion widths at a 0.4mm
                      # nozzle", which this comment claimed: two 0.40mm extrusions is 0.80, so
                      # 0.70 is 1.75 of them. It prints as ONE wide extrusion rather than two
                      # lines — solid, but the edges round over and the cells read slightly
                      # larger than drawn. Kept at 0.70 because that is acceptable on a
                      # decorative face and raising it would shrink the cell counts the region
                      # asserts are calibrated against; 0.85-0.90 if you ever want two genuine
                      # lines. The comment is fixed rather than the number precisely because a
                      # stated-as-fact justification is what licenses a wrong edit later.
                      # (HEX_WEB = 0.90 on the back face IS 2.25 widths, so that one is two
                      # lines and its comment is right.)
# r6 (2026-08-26): MARK_MARGIN deleted with the frieze it margined (see WIN_MARGIN_TOP
# and the note where _bezel_mark() used to be). This file's own SIDE-CHANNEL lesson:
# a constant with no consumer cannot be wrong in a way anything detects — so it goes
# rather than lingers. Its reasoning (straight-edge outer bound, 11.25-in-11.29 near-
# coincidence that forced an honest margin) is in git history at this line.
BEZ_MARGIN   = 1.20   # keepout from the outer edge, the screen window, the mic flare AND the
                      # four screw bosses. ⚠️ An earlier version of this comment named three
                      # keepouts and the code implemented one and a half: the window was tested
                      # only on its BOTTOM edge and only in the chin, the mic flare was never
                      # tested anywhere (it held solely because the brow was then excluded), and the
                      # screw bosses were not considered at all — so 4 chin cells overlapped a
                      # 2.50mm pilot and 5 more the 5.40mm pad, thinning the roof over a
                      # fastener from 1.50 to 1.05mm, and the mark overlapped the (4,82) boss
                      # pad by 1.18mm. The rails' clearance from the window's vertical edges
                      # was 1.575mm BY LUCK. A comment that lists the keepouts is not a test
                      # that applies them, and this one was read as if it were for hours.

def _inside_rrect(px, py, x0, x1, y0, y1, r, m=0.0):
    """Is (px,py) inside a rounded rectangle, inset by m? Standard rounded-rect distance.

    This exists because the bezel's outline is a RectangleRounded with a 6.45mm corner, and a
    naive x/y range test lets cells sit in the corner voids where there is no material — a
    hex tiling that pokes out of the part's own silhouette. At x=1.0 the top edge is at 88.45,
    not 88.95, purely because of the corner arc.
    """
    dx = max(x0 + r - px, px - (x1 - r), 0.0)
    dy = max(y0 + r - py, py - (y1 - r), 0.0)
    return math.hypot(dx, dy) <= r - m

def _bezel_cells():
    """Pointy-top hex cells on the bezel face. Returns (solid, {region: count}).

    TWO REGIONS, GENERATED SEPARATELY, AND COUNTED SEPARATELY. The first version filtered one
    global staggered grid and produced 75 cells — all of them in the CHIN, none on the rails,
    because the nearest grid column missed the rail's 0.75mm-wide usable band by 0.05mm. That
    is the worst possible outcome: the stand covers 86% of the chin and 0% of the rails, so
    the entire motif landed on the one surface you cannot see while docked.
    ⚠️ AND THE ASSERT PASSED. It read `_n >= 60`, and 75 >= 60 is true. A TOTAL ABSORBED A
    COMPLETE REGIONAL ABSENCE — the same shape as every other proxy failure recorded in
    docs/verification.md: the number was real, it just wasn't the property. Hence a dict of
    per-region counts and a non-empty assert on each, which no single total can satisfy
    vacuously. If you add a region, add its count and its assert.

    The rails get an explicit CHAIN rather than a filtered tiling, because a 3.35mm usable
    width admits exactly one column and whether that column exists should not depend on where
    a global grid's phase happens to fall.

    POINTY-TOP here (rotation=30), unlike the button caps: this is decorative lattice with no
    hinge to hem, so it follows the honeycomb pitch the rest of the case uses.

    The brow WAS deliberately excluded while it carried the wyrm mark ("a mark reads
    better against a calm field than against texture"). r6 (2026-08-26) removed the mark
    — JP's thumb-access verdict, see WIN_MARGIN_TOP — so the brow now takes the same
    staggered honeycomb as the chin: same generator, mirrored bounds, its own count and
    its own floor, per this docstring's own rule about adding regions. The mic flare and
    boss keepouts do the fragmenting they always did; _fits() already knows them.
    """
    R = BEZ_AFLAT / math.sqrt(3)          # circumradius: pointy-top spans R*sqrt(3) across
    px, py = BEZ_AFLAT + BEZ_WEB, 1.5 * R + BEZ_WEB * math.sqrt(3) / 2
    win = (VA[0]-WIN_MARGIN, VA[1]+WIN_MARGIN, VA[2]-WIN_MARGIN, VA[3]+WIN_MARGIN_TOP)
    out = None
    cnt = {"chin": 0, "rails": 0, "brow": 0}

    def _fits(x, y):
        # inside the part's rounded outline...
        if not all(_inside_rrect(x + R*math.cos(math.radians(a+30)),
                                 y + R*math.sin(math.radians(a+30)),
                                 OX0, OX1, OY0, OY1, OUT_R, BEZ_MARGIN)
                   for a in range(0, 360, 60)):
            return False
        # ...clear of the mic flare (2.30 radius)...
        if math.hypot(x-MIC[0], y-MIC[1]) < 2.30 + BEZ_MARGIN + R:
            return False
        # ...clear of all four screw bosses, on the PAD diameter not the pilot. The pad is
        # what must stay solid: a cell over the 2.50 pilot is a hole into a fastener, and a
        # cell over the 5.40 pad thins the roof over it to 1.05mm.
        for (hx, hy) in HOLES:
            if math.hypot(x-hx, y-hy) < BOSS_D/2 + BEZ_MARGIN + R:
                return False
        # ...and clear of the screen window on ALL FOUR edges, not just the
        # bottom one — INCLUDING the r5 tap ramp: a deboss cut into the ramp's
        # thinning face would locally break the 2.00-over-glass rule that the
        # global assert can only check against full BEZEL_T.
        if not (x + R < win[0]-BEZ_MARGIN-BEZEL_RAMP_W or x - R > win[1]+BEZ_MARGIN+BEZEL_RAMP_W
                or y + R < win[2]-BEZ_MARGIN-BEZEL_RAMP_W or y - R > win[3]+BEZ_MARGIN+BEZEL_RAMP_W):
            return False
        return True

    def _cell(x, y):
        return Pos(x, y, FRONT_Z - BEZEL_DEBOSS) * extrude(
                   RegularPolygon(R, 6, rotation=30), BEZEL_DEBOSS + 1)

    # --- CHIN: a proper staggered honeycomb, full width, below the window ---
    j, y = 0, OY0
    while y <= win[2]:
        x = OX0 + (px/2 if j % 2 else 0.0)
        while x <= OX1:
            if _fits(x, y):
                out = _cell(x, y) if out is None else out + _cell(x, y)
                cnt["chin"] += 1
            x += px
        y += py
        j += 1

    # --- BROW: the chin's mirror, above the window (r6 — the wyrm's old ground) ---
    # Same staggered grid walked upward from the window's top edge. Rows are phased
    # from win[3] rather than continuing the chin's phase: the two fields are separated
    # by the full screen window, so phase continuity across it is invisible, and phasing
    # from the nearer edge is what makes the first row land tight to the ramp the way
    # the chin's first row lands tight to the bottom edge.
    j, y = 0, win[3] + BEZEL_RAMP_W + BEZ_MARGIN + R
    while y <= OY1:
        x = OX0 + (px/2 if j % 2 else 0.0)
        while x <= OX1:
            if _fits(x, y):
                out = _cell(x, y) if out is None else out + _cell(x, y)
                cnt["brow"] += 1
            x += px
        y += py
        j += 1

    # --- RAILS: one explicit chain up each side of the window ---
    # Pitch is 2R + BEZ_WEB, so the vertical gap between cells matches the web thickness used
    # everywhere else. That consistency reads more strongly at arm's length than sharing the
    # chin's row rhythm would, and a lone column of a staggered tiling (pitch 3R) would look
    # like a dotted line rather than a chain.
    for rc in ((OX0 + win[0]) / 2.0, (win[1] + OX1) / 2.0):
        y = win[2] + R
        while y <= win[3] - R:
            if _fits(rc, y):
                out = _cell(rc, y) if out is None else out + _cell(rc, y)
                cnt["rails"] += 1
            y += 2*R + BEZ_WEB
    return out, cnt

# r6 (2026-08-26): _bezel_mark() deleted with the frieze it cut — the four-edge tap
# ramp evicted the wyrm from the brow (JP's thumb-access verdict; see WIN_MARGIN_TOP).
# The creature still renders on the stand grille (WYRM_ON island) and on the screen;
# the mark's placement math, its EPS non-manifold lesson, and the two-component head
# bug are preserved in git history and in the notes at the stand's cut site.
def cap_hex_pts(cx, cy, R):
    """The six corners of a FLAT-top hexagon, in mm, counter-clockwise from +X.

    ONE SOURCE FOR THE CAP OUTLINE. This exists because the outline was previously typed
    twice — once as a solid here and once as a hand-written polygon in
    `tools/make_renders.py` — and the two copies were free to disagree forever with nothing
    to notice. They did: the solid and the figure were both rectangles, JP asked for
    hexagons, and only the figure was ever looked at. A second hand-drawn copy of geometry
    is not documentation of the geometry, it is a rumour about it.

    Flat-top means a vertex at +/-X and a flat edge at +/-Y: 2R across corners, R*sqrt(3)
    across flats. The +Y flat is the hinge, which is the whole reason for this orientation.
    """
    return [(cx + R*math.cos(math.radians(a)), cy + R*math.sin(math.radians(a)))
            for a in range(0, 360, 60)]

def cap_hex_top_y(cy, R):
    """Y of the flat-top hexagon's +Y edge — where the hinge lives."""
    return cy + R*math.sqrt(3)/2

def cap_hinge_len(cx):
    """Thinned-flexure length for the cap at board x=cx. Keyed on the coordinate, like
    cap_geometry, and for the same reason: sides flip between figures, coordinates do not."""
    return HINGE_L_BOOT if cx == BTN_BOOT_X else HINGE_L_RESET

def cap_center_x(cx):
    """Island centre X for the cap actuating the switch at board x=cx — NOT the switch's x.

    Added as a separate function rather than a fourth element of cap_geometry()'s tuple
    deliberately: that tuple has six call sites and two of them are inside a block another
    agent is editing right now. Widening a shared signature mid-flight breaks their work with a
    stack trace that looks like their bug. A new function breaks nothing.
    """
    return CAP_CX_BOOT if cx == BTN_BOOT_X else CAP_CX_RESET

def cap_geometry(cx):
    """(cy, R, extra_label_depth) for the cap at board x=cx. THE single derivation.

    The third element cut a face recess until r11; the bench rejected that recess (bed-side
    bridge, sagged) and it now only deepens the cap's label — see DEBOSS_BIG/DEBOSS_SMALL.

    Keyed on the coordinate rather than an index or a side, per the never-say-left-or-right
    rule above: the apparent side flips between three figures of this same part, so a caller
    that asks for "the big one" by position is correct in one figure and silently wrong in
    the others. Asking by x cannot be mirrored by a camera.
    """
    big = (cx == BTN_BOOT_X)
    R = BTN_R_BIG if big else BTN_R_SMALL
    return (_cap_cy(R), R,
            DEBOSS_BIG if big else DEBOSS_SMALL)

def hexp(cx, cy, R, z0, z1):
    """Flat-top hexagonal prism. Deliberately NOT rotation=30 — see BTN_R_BIG."""
    return Pos(cx, cy, z0) * extrude(RegularPolygon(R, 6), z1 - z0)

def cone(x,y,z0,z1,d0,d1):
    return Pos(x,y,z0) * Cone(d0/2, d1/2, z1-z0,
                              align=(Align.CENTER,Align.CENTER,Align.MIN))

# ============================================================================
# 4. FRONT BEZEL   -- the part that unblocks printing
# ============================================================================
def front_bezel():
    p  = rbox(OX0,OX1,OY0,OY1, SEAM_Z, FRONT_Z, OUT_R)
    # screen window
    w  = (VA[0]-WIN_MARGIN, VA[1]+WIN_MARGIN, VA[2]-WIN_MARGIN, VA[3]+WIN_MARGIN_TOP)
    sk = RectangleRounded(w[1]-w[0], w[3]-w[2], 1.5)
    p -= Pos((w[0]+w[1])/2,(w[2]+w[3])/2, SEAM_Z-1) * extrude(sk, BEZEL_T+2)
    # ---- r5 tap ramp: 45deg from the face down to a BEZEL_LIP_T rim ----
    # A loft cut rather than an edge-chamfer op: explicit geometry, no edge
    # selection to silently miss. Printed front-face-down the ramp is a 45deg
    # rising ceiling — exactly the printability doctrine's limit, same as the
    # mushroom cap that proved it. The +0.01 top keeps the loft's upper face
    # proud of FRONT_Z so the boolean can't leave a zero-thickness skin.
    _cx, _cy = (w[0]+w[1])/2, (w[2]+w[3])/2
    # FOUR-EDGE RAMP (r6, 2026-08-26 — the top-edge exception is retired, see
    # WIN_MARGIN_TOP; JP's thumb needs the top of the screen too). Every sketch
    # edge that would coincide with the window cut's wall is pushed 0.02 PAST
    # it instead: coincident cut faces are non-manifold by definition, not by
    # rounding (the wyrm mark's EPS lesson; measured here too — exactly 3
    # non-manifold edges when the lower sketch kissed the window wall).
    def _rr(x0, x1, y0, y1, r):
        return Pos((x0+x1)/2, (y0+y1)/2, 0) * RectangleRounded(x1-x0, y1-y0, r)
    _lo = _rr(w[0]-0.02, w[1]+0.02, w[2]-0.02, w[3]+0.02, 1.5)
    _hi = _rr(w[0]-BEZEL_RAMP_W, w[1]+BEZEL_RAMP_W,
              w[2]-BEZEL_RAMP_W, w[3]+BEZEL_RAMP_W, 1.5)
    _ramp = loft([Pos(0, 0, FRONT_Z - BEZEL_RAMP_W) * _lo,
                  Pos(0, 0, FRONT_Z + 0.01) * _hi])
    p -= _ramp
    # The rim is the thinnest place a finger can press: assert it holds the
    # min-feature floor, and that the ramp's arithmetic still means 45deg.
    assert BEZEL_LIP_T >= 0.90, f"bezel rim {BEZEL_LIP_T}mm is under the 0.90 floor"
    assert abs(BEZEL_RAMP_W - (BEZEL_T - BEZEL_LIP_T)) < 1e-9, "ramp is not 45deg"
    # mounting bosses: PCB top face up into the bezel body.
    # FLARED, not straight — the straight ones snapped off. See BEZEL_BOSS_FLARE_D
    # for why the root is the failure plane and why this taper is also the easier
    # thing to print. BOSS_D still governs the PCB-face end, so the d5.60 vendor
    # pad keepout is unchanged and so is the front-face hex keepout.
    for (hx,hy) in HOLES:
        p += cone(hx,hy, PCB_TOP, SEAM_Z, BOSS_D, BEZEL_BOSS_FLARE_D)
        p -= cyl(hx,hy, PCB_TOP-0.01, SEAM_Z+1.5, PILOT_D)
    # The flare is only safe because it fits; assert that rather than trusting the
    # derivation above to stay true if a hole, the window or the silhouette moves.
    # A boss that quietly breaches the window is a hole over the LCD.
    _fr = BEZEL_BOSS_FLARE_D / 2.0
    _win = (VA[0]-WIN_MARGIN, VA[1]+WIN_MARGIN, VA[2]-WIN_MARGIN, VA[3]+WIN_MARGIN_TOP)
    for (hx, hy) in HOLES:
        _edge = min(hx - OX0, OX1 - hx, hy - OY0, OY1 - hy) - _fr
        assert _edge >= 1.20, (
            f"bezel boss flare at ({hx},{hy}) leaves {_edge:.2f}mm to the outer "
            f"silhouette — under one 1.20mm wall")
        # The bosses sit outside the window in y; the gap that matters is to the
        # nearer y edge. If a boss ever lands inside the window's x-span AND its
        # y-span this goes negative, which is the breach worth failing on.
        _wy = min(abs(hy - _win[2]), abs(hy - _win[3])) - _fr
        assert _wy >= 1.20, (
            f"bezel boss flare at ({hx},{hy}) comes within {_wy:.2f}mm of the "
            f"screen window — it would open a hole over the glass")
    # ---- MIC: defined acoustic port + collar down to just above the PCB ----
    mx,my = MIC
    p += cyl(mx,my, PCB_TOP+0.30, SEAM_Z, 5.0)          # collar (tube wall)
    p -= cyl(mx,my, PCB_TOP+0.20, FRONT_Z+1, 2.40)       # the port bore
    p -= cone(mx,my, FRONT_Z-0.90, FRONT_Z+0.01, 2.40, 4.60)  # outside flare
    # ---- debossed honeycomb, cut INTO the front face ----
    # r6 (2026-08-26): the hearth-wyrm frieze no longer lives here — the four-edge
    # tap ramp evicted it (JP's verdict; see WIN_MARGIN_TOP). The creature remains
    # on the stand's grille and the screen. Its old ground, the brow, now carries
    # honeycomb like the chin.
    _cells, _cnt = _bezel_cells()
    if _cells is not None:
        p -= _cells
    # A DEBOSS THAT BREAKS THROUGH IS A HOLE. The bezel is BEZEL_T over the glass and this
    # face is the only thing between a finger and the LCD, so assert the remaining thickness
    # rather than trusting that 0.45 "looks shallow".
    assert BEZEL_T - BEZEL_DEBOSS >= 2.00, (
        f"a {BEZEL_DEBOSS}mm deboss leaves only {BEZEL_T-BEZEL_DEBOSS:.2f}mm of bezel over "
        f"the glass")
    # PER-REGION, never a total: see _bezel_cells() for the run where 75 >= 60 passed with
    # the rails completely empty.
    # THRESHOLDS, AND WHY THEY MOVED. The chin was 75 cells and is now 57: adding the screw
    # boss keepout removed 9 cells per boss and two of the four bosses are in the chin, so the
    # 18-cell drop is accounted for rather than tolerated. The floors below are set to catch a
    # region COLLAPSING — which is the failure this assert exists for, after 75 cells all
    # landed in the chin and the rails got none — not to track the exact count. Do not simply
    # lower a floor to make a build pass; work out where the cells went first.
    # FLOORS MOVED r5 (2026-08-25), with the accounting the rule demands:
    #   chin 50 -> 35: the window's 1.00mm bottom retreat plus the 2.10mm ramp
    #   keepout removed the chin's top ~3 cell rows — 57 cells became 42, each
    #   loss attributable to the tap-ramp geometry, none to a grid failure.
    #   rails 20 -> RETIRED: the side strips (4.75mm outer-edge-to-window) are
    #   now 2.10mm of ramp plus margins — no full-thickness face wide enough
    #   for a single cell remains. The rails REGION is the ramp now: a smooth
    #   45-degree grip slope instead of texture, which is the feature, not a
    #   collapse. The count stays printed so a future geometry change that
    #   resurrects the region is visible.
    #   brow floor ADDED r6 (2026-08-26): the wyrm left (see WIN_MARGIN_TOP) and the
    #   brow now hexes like the chin. OBSERVED 8, and the 8 is accounted for, not
    #   tolerated: the 10.59mm band (window top 76.26 + 2.10 ramp .. OY1 88.95) admits
    #   exactly TWO rows at the 2.86 row pitch under the 1.20 outline margin, and the
    #   two top screw bosses (keepout r≈5.4 at y=82) plus the mic flare (r≈5.0) eat the
    #   row ends and middle. A provisional floor of 10 failed the first build — that
    #   was the floor being wrong, worked out above, not the region collapsing. Floor 6
    #   catches a row vanishing (8→≤4 if either row dies) without tripping on keepout
    #   arithmetic.
    for _rg, _min in (("chin", 35), ("brow", 6)):
        assert _cnt[_rg] >= _min, (
            f"only {_cnt[_rg]} hex cells landed on the bezel {_rg} (need >={_min}) — "
            f"a keepout or the grid phase has eaten the region. Counts: {_cnt}")
    assert _cnt["rails"] == 0, (
        f"the r5 ramp was expected to consume the rails entirely, but {_cnt['rails']} "
        f"cell(s) landed there — the ramp keepout has a gap; find it before trusting the face")

    # r6: the wyrm-mark asserts (one-piece, min-feature, mic-flare gap, group centring,
    # brow fit) left with the mark itself — 2026-08-26, JP's thumb-access verdict. They
    # guarded a frieze that is no longer cut here; the stand's grille island keeps its own
    # WYRM_COMPONENTS == 1 protection at its own cut site.
    front_bezel.report = _cnt
    return p

# ============================================================================
# 5. BACK SHELL
# ============================================================================
# ============================================================================
# SIDE-WALL OPENINGS — DERIVED FROM THE COMPONENTS THEY EXIST TO CLEAR
# ============================================================================
#
# ⚠️ THIS IS THE FIX FOR THE FAILURE THAT CAUSED THE REPRINT, and it is structural rather than
# numeric. The channels used to be two hand-typed literals:
#
#     [(14.0,40.5),(44.0,56.0),(62.0,75.0)]     and     [(14.0,26.0),(29.0,42.0)]
#
# and the constant that NAMED the feature they served — the old `SD_PLATE` — had NO CONSUMERS.
# `grep` found it in its own definition and two comments, nothing else. So the coordinate and
# the opening were never connected by anything except a human reading both.
#
# ⚠️ A CONSTANT WITH NO CONSUMER CANNOT BE WRONG IN A WAY ANYTHING DETECTS. Nothing recomputes
# when it changes, no assert compares it to the geometry, and its only reader is a person who
# has to re-derive the link every time. That is why a 26.50mm opening with 18.54mm of nothing
# behind it survived every check in this file: the checks all compare the PART to the BOARD, and
# an opening over a component that isn't there is agreement, not conflict.
#
# Now the spans are computed from CONN_R / CONN_L / SD_SOCKET. A wrong coordinate MOVES an
# opening, and `_check_geometry()` asserts the converse — every span must have a component
# behind it. The dead-`GRILLE_SLOT_W` hazard this file already logs, one screenful above
# CAP_CX_BOOT, is the same shape; it recurred anyway, so this time the link is code.
CHAN_PAD      = 1.00   # lead-in each side of a connector footprint. The shipped non-phantom
                       # channels had 0.84 / 0.69 / 0.91, so 1.00 is not a tightening.
CHAN_RIB      = 1.20   # thinnest wall allowed between two openings; under this they MERGE
                       # rather than leaving a stringy fin. Three extrusions at a 0.4 nozzle.
SD_SLIT_INSET = 0.50   # slit is the socket span less this, so it cannot undercut the socket's
                       # own side walls while still clearing SD_CARD_W plus a finger.

def _merge_spans(spans, min_rib):
    """Sort, then merge any pair separated by less than min_rib.

    A rib thinner than a few extrusion widths is not a wall, it is a defect that happens to
    have a dimension — the same reasoning desk_stand() applies to its finger pockets."""
    out = []
    for a, b in sorted(spans):
        if out and a - out[-1][1] < min_rib:
            out[-1] = (out[-1][0], max(out[-1][1], b))
        else:
            out.append([a, b])
    return [(a, b) for a, b in out]

# ============================================================================
# 5a-ter. WHICH FLANK OPENINGS ARE SUPPRESSED, AND ON WHICH VARIANT.  JP, 2026-08-01.
# ============================================================================
#
# >>> JP: "block the speaker and the battery holes out the side." <<<
#
# It lands FULLY on the mobile and PARTLY on the desk, and the difference is not a preference —
# it is a route that exists on one variant and not the other. Stated per connector, because
# "close the flanks" is the kind of instruction that is right about the goal and wrong about
# the geometry, and this file has already paid for one walled-in connector (the microSD).
#
#   BAT   — blocked on BOTH. On the mobile the pigtail never used a side channel: it runs
#           cover compartment -> the midframe's own floor pass (outside the seal rim) -> board
#           cavity -> CONN_L[0], entirely internal. On the desk the connector has no consumer
#           at all; there is no cell in the stand.
#   SPK   — blocked on the MOBILE ONLY, where the driver lives inside the cover's sealed cavity
#           and its pigtail leaves through the SPK relief, never through the flank.
#
#           ⚠️ AND NOT ON THE DESK, WHERE IT IS LOad-BEARING. Two witnesses, both in this file:
#           (1) SPK_RELIEF_CLR's own block — the relief is PLUG clearance, and "the connector
#               already fills the cavity to within 0.80mm, so the lead CANNOT travel over the
#               top of it"; the recorded route is that the lead "leaves through the side channel
#               that already serves this Y span";
#           (2) the stand's speaker-wire route — "the board's speaker header is on a LONG EDGE,
#               so the wire has to reach the slab slot".
#           A rear exit cannot substitute: the stand's route is 16 wide on ST_W/2 and this
#           connector docks about ST_W/2 + 22.4, i.e. ~14mm outboard of it, so a wire leaving
#           the back face there is pinched between shell and stand — precisely the hazard both
#           files were written to avoid. Blocking it would strand the desk speaker.
SIDE_BLOCK = {
    "desk":   {("L", 0)},                       # BAT
    "mobile": {("L", 0), ("R", SPK_CONN_I)},    # BAT + SPK
}


def _side_spans():
    """Every connector's NOMINAL flank span, tagged, before any variant suppression.

    Kept separate from what is actually cut because the LABELS and the access ledger both need
    to reason about connectors that no longer have an opening — which is the whole point of the
    ledger now that "served" no longer means "has a side channel".
    """
    hi = [(("R", i), (y0 - CHAN_PAD, y1 + CHAN_PAD)) for i, (y0, y1) in enumerate(CONN_R)]
    lo = [(("L", i), (y0 - CHAN_PAD, y1 + CHAN_PAD)) for i, (y0, y1) in enumerate(CONN_L)]
    slit = (SD_SOCKET[2] + SD_SLIT_INSET, SD_SOCKET[3] - SD_SLIT_INSET)
    (lo if _SD_CX < BW/2 else hi).append((("SD", 0), slit))
    return hi, lo


def side_channels(variant=None):
    """(spans on the x=BW edge, spans on the x=0 edge), derived from the component tables.

    The microSD slit goes on WHICHEVER EDGE THE SOCKET IS ON — read from SD_SOCKET, not typed.
    That is deliberate: the last time this was decided by a human reading a coordinate, the
    coordinate was a placeholder and the opening landed on the far side of the board.

    variant=None returns the NOMINAL set — every connector's span, nothing suppressed. That is
    what the labels are packed against, so a label's position does not shift between variants
    just because a neighbour's opening closed. Pass a variant name for what is actually CUT.
    """
    _blocked = SIDE_BLOCK.get(variant, set())
    hi, lo = _side_spans()
    hi = [s for k, s in hi if k not in _blocked]
    lo = [s for k, s in lo if k not in _blocked]
    return _merge_spans(hi, CHAN_RIB), _merge_spans(lo, CHAN_RIB)

# ============================================================================
# 5a-bis. BACK-FACE LABELS  --  SD, VOL, a power symbol, MIC
# ============================================================================
#
# DEBOSSED, and for the same reason the button caps are: this face prints against the bed, so
# a raised feature becomes the lowest thing on the part and the shell balances on it. The
# depth is a whole number of the SHELL's layers -- see LABEL_DEBOSS for why it is 2 and not 3.
#
# ⚠️ MIRRORED IN X, AND THIS IS THE ONE THAT SHIPS BACKWARDS IF NOBODY WRITES IT DOWN.
# The back face is seen from -Z. For a viewer there with +Y up, their right-hand direction is
# forward x up = (0,0,1) x (0,1,0) = (-1,0,0) -- so model +X runs to their LEFT. Every glyph
# is therefore authored in READING space (u to the right as read) and mirrored on placement by
# _back_label(). The wyrm mark on the FRONT bezel is also mirrored, but for art-direction
# reasons, so it is not precedent for this and copying its sign would prove nothing.
#
# TWO SIZES, NOT ONE, and the split is forced rather than stylistic. The big cap is 13.27mm
# across flats, which caps a three-letter label at h=3.80. The flat back has room for h=5.50,
# and SD NEEDS it: at h=5.10 the S's upper counter pinches to 0.843mm against the 0.90 floor.
# Using the cap size everywhere would have put an unprintable S on the part; using the flat
# size everywhere would not fit on the cap.
import strokefont as _SF

LABEL_W      = 0.90            # groove width == this repo's nozzle floor, the same 0.90 the
                               # wyrm mark asserts. It is an ARGUMENT to the stroke font, not
                               # a consequence of a typeface -- see tools/strokefont.py.
LABEL_GAP    = 1.90            # centreline gap between glyphs -> exactly 1.00mm of material.
                               # 1.80 was tried and lands the gap ON 0.90, i.e. zero margin.
# ⚠️ WAS `3 * LAYER_H` = 0.48, i.e. three layers of the BEZEL's height applied to a SHELL feature
# — 2.4 layers at the shell's own 0.20. TWO layers, not three, and the reason is the pad assert
# below rather than taste: at 3 shell layers (0.60) the big cap keeps
# WALL - DEBOSS_BIG - LABEL_DEBOSS = 2.60 - 0.80 - 0.60 = 1.20, exactly ON the 1.20 floor, and a
# value sitting on a constraint boundary has no slack. 2 layers leaves 1.40.
LABEL_DEBOSS = 2 * LAYER_H_SHELL   # 0.40
LABEL_H_CAP  = 3.80            # centreline cap height on a button face (ink 4.70)
LABEL_H_FLAT = 5.50            # centreline cap height on the flat back  (ink 6.40)
LABEL_MARGIN = 0.80            # keepout from any edge or neighbouring feature
# ---- and two constants that exist only because a slice of the finished mesh was looked at ----
#
# >>> THE FIRST CUT OF THE CONNECTOR LABELS READ `SPKI2C` AND `BATUARTSD`. <<<
#
# Every assert passed. Each label cleared its 0.90mm floor, each sat on its own port, and no
# two ink boxes came within LABEL_MARGIN. And the result was unreadable, because LABEL_MARGIN
# is 0.80 while the material BETWEEN TWO GLYPHS of one word is LABEL_GAP - LABEL_W = 1.00 —
# so the space between two labels was SMALLER than the space inside one, and the eye correctly
# read them as a single word. A keepout is not a word space; nothing had ever needed the
# difference before because no two labels had ever been neighbours.
LABEL_WORD_GAP = 2 * (LABEL_GAP - LABEL_W)   # 2.00 — twice the material inside a word.
# 3x was tried first and does not fit: at 3.00 the UART label is forced down until its ink
# reaches into BAT's own channel, which trades a legibility defect for a naming one. 2.00 is
# the largest word space the left strip can carry with all three labels still over their own
# features, and it is double the 1.00mm that reads as a letter space.
# ⚠️ AND SHRINKING THE LABELS TO AFFORD IT IS NOT AVAILABLE, WHICH IS WORTH RECORDING BECAUSE
# IT WAS THE OBVIOUS MOVE AND IT FAILED ON THE FIRST BUILD. A 4.50 connector height was tried;
# `S` immediately went under the floor at 0.638mm, because the glyph is normalised and the
# 0.90 stroke is not, so every counter scales with h while the stroke does not:
#
#     S's material at h  =  (0.98 + 0.90) * h/5.50 - 0.90   ->  S needs h >= 5.27
#
# `SPK` contains an S, so the connector set cannot go below ~5.27 at all. Everything therefore
# stays at LABEL_H_FLAT, and the room for the word space is found in the PLACEMENT RULE
# instead — see _pack_labels and the ledger below.
PWR_R        = 2.70            # power-symbol ring, centreline radius (ink dia 6.30)
PWR_STEP_DEG = 12.0            # ring subdivision. Sagitta = r*(1-cos(6deg)) =
                               # 0.015mm, invisible at a 0.4mm nozzle, and the
                               # CHECK reads the same polyline the cut does.
PWR_GAP_DEG  = 84.0            # DERIVED, not styled: the material between a ring end and the
                               # bar is PWR_R*sin(gap/2) - LABEL_W, so clearing 0.90 needs
                               # gap >= 83.6 deg. A conventional 60-deg break measures 0.45mm
                               # and prints as a closed ring with a smudge in it.

_pwr_web = PWR_R * math.sin(math.radians(PWR_GAP_DEG / 2)) - LABEL_W
assert _pwr_web >= LABEL_W, (
    f"the power symbol's break leaves {_pwr_web:.3f}mm between the ring end and the bar, "
    f"under the {LABEL_W}mm floor. Widen PWR_GAP_DEG or grow PWR_R.")


def _label_sketch(paths, w):
    """Reading-space centrelines -> one 2D sketch of round-capped strokes.

    2D rather than 3D on purpose: ~130 segments across the four labels, and fusing that many
    SOLIDS in OCC is minutes where fusing faces is seconds. One extrude at the end.

    ⚠️ BULK-FUSED, NOT ACCUMULATED. `sk = sk + piece` in a loop is quadratic in OCC -- it
    rebuilds the whole result every iteration -- and it took this model from 3s to over four
    minutes. `Sketch() + [pieces]` fuses in one pass: measured 0.30s vs 5.01s on 120 discs,
    and the gap widens with count. One round cap per unique VERTEX rather than two per
    segment halves the face count again."""
    pieces, seen = [], set()
    for poly in paths:
        for i, (vx, vy) in enumerate(poly):
            key = (round(vx, 6), round(vy, 6))
            if key not in seen:                 # one cap per vertex, not two per segment
                seen.add(key)
                pieces.append(Pos(vx, vy) * Circle(w / 2))
            if i + 1 < len(poly):
                (bx_, by_) = poly[i + 1]
                L = math.hypot(bx_ - vx, by_ - vy)
                if L > 1e-9:
                    pieces.append(Pos((vx + bx_) / 2, (vy + by_) / 2)
                                  * Rot(0, 0, math.degrees(math.atan2(by_ - vy, bx_ - vx)))
                                  * Rectangle(L, w))
    return Sketch() + pieces


def _back_label(paths, cx, cy, z0, z1, rot90=False):
    """Cut-solid for a label centred on the back face at board (cx, cy). See the mirror note."""
    if rot90:                                  # reads bottom-to-top, for a label beside a slit
        paths = [[(-v, u) for (u, v) in poly] for poly in paths]
    paths = [[(-u, v) for (u, v) in poly] for poly in paths]        # <-- THE MIRROR
    return Pos(cx, cy, z0) * extrude(_label_sketch(paths, LABEL_W), z1 - z0)


def _label_ok(paths, what):
    """Every label proves its own material clearance before it is allowed onto the part."""
    d, who, n = _SF.min_gap(paths, LABEL_W)
    assert n > 0, (
        f"label {what!r}: min_gap measured ZERO pairs, which reads as a pass and is not one — "
        f"it means every counter has fused into ink. See strokefont.min_gap's RETURNS note.")
    assert d >= LABEL_W, (
        f"label {what!r} leaves {d:.3f}mm of material at its tightest point, under the "
        f"{LABEL_W}mm floor — it will print as a smudge. Worst pair: {who}")
    return d


def _hex_holds(w, h, R, margin, what):
    """Does an ink box of w x h fit inside a FLAT-TOP hexagon of circumradius R, inset by
    `margin`? Flat-top means the binding constraint is the slanted edge, not the width:
    a point is inside iff |y| <= sqrt(3)R/2 AND sqrt(3)|x| + |y| <= sqrt(3)R."""
    Ri = R - 2 * margin / math.sqrt(3)          # inset perpendicular to every edge
    x, y = w / 2.0, h / 2.0
    slack = math.sqrt(3) * Ri - (math.sqrt(3) * x + y)
    assert y <= math.sqrt(3) * Ri / 2 and slack >= 0, (
        f"{what}: a {w:.2f}x{h:.2f}mm label does not fit a hexagon of R={R:.3f} with "
        f"{margin}mm of margin (slack {slack:+.3f}mm). Shrink LABEL_H_CAP.")
    return slack / math.sqrt(3)                 # spare margin, perpendicular to the slant


def _hex_holds_circle(d, R, margin, what):
    """Same question for a ROUND mark. A circle is not its bounding box and using the box
    test on the power symbol failed it by 1.94mm on a hexagon it clears by 0.98 — the box's
    corners overhang the circle by 41%, and a hexagon is exactly where that bites."""
    apothem = math.sqrt(3) * R / 2.0
    slack = apothem - d / 2.0 - margin
    assert slack >= 0, (
        f"{what}: a {d:.2f}mm round mark does not fit a hexagon of R={R:.3f} with {margin}mm "
        f"of margin (slack {slack:+.3f}mm). Shrink PWR_R.")
    return slack


# ---- WHERE EACH LABEL GOES. Every coordinate DERIVED from the feature it names. ------------
#
# This file has been bitten twice by a coordinate that named a feature and was linked to it
# only by a human reading both (the dead SD_PLATE, the dead GRILLE_SLOT_W). A label is the
# purest form of that hazard -- it is a coordinate whose ENTIRE JOB is to point at something
# else -- so none of these are typed. Move the mic and its label follows; move the hex field
# and the SD label re-centres in whatever margin is left.
_LBL = {}
_LBL["VOL"] = _SF.text_paths("VOL", LABEL_H_CAP,  LABEL_W, LABEL_GAP)
_LBL["PWR"] = _SF.power_paths(PWR_R, LABEL_W, PWR_GAP_DEG, PWR_STEP_DEG)
_LBL["SD"]  = _SF.text_paths("SD",  LABEL_H_FLAT, LABEL_W, LABEL_GAP)
_LBL["MIC"] = _SF.text_paths("MIC", LABEL_H_FLAT, LABEL_W, LABEL_GAP)
for _t in ("UART", "I2C", "SPK", "BAT", "IO"):          # the connector set, issue #27
    _LBL[_t] = _SF.text_paths(_t, LABEL_H_FLAT, LABEL_W, LABEL_GAP)
# ---- THE SAME NAMES AT THE MOBILE'S SIDE-FLANK SIZE (a different print class entirely) ----
# Smaller glyphs on a narrower stroke, for a VERTICAL WALL rather than the bed face. Built here
# beside their full-size twins so the two sets cannot drift apart in content, and floor-checked
# against the stroke they are actually drawn with rather than against LABEL_W.
# SD is deliberately absent: its S does not fit the flank band at a printable stroke, and the
# mobile file carries the shortfall number. A set that silently dropped it would read as an
# oversight; a set that never had it, with the arithmetic beside it, reads as a decision.
LBL_SIDE_H = 3.90
LBL_SIDE_W = 0.80
LBL_SIDE_GAP = LBL_SIDE_W + 1.00
_LBL_SIDE = {}
for _t in ("UART", "I2C", "IO"):
    _LBL_SIDE[_t] = _SF.text_paths(_t, LBL_SIDE_H, LBL_SIDE_W, LBL_SIDE_GAP)
    _d, _who, _ = _SF.min_gap(_LBL_SIDE[_t], LBL_SIDE_W)
    assert _d >= 2 * 0.40, (
        f"side label {_t!r} pinches to {_d:.3f}mm of material at h={LBL_SIDE_H}, under the two "
        f"extrusions (0.80) that are this project's only PROVEN web on a vertical wall (the back "
        f"grill). Worst pair: {_who}")

# SD at the mobile flank's EXPERIMENTAL stroke (JP: "try on the sude anyway"). Its own entry,
# its own floor check against its own stroke -- deliberately NOT in _LBL_SIDE, so the three
# proven labels cannot inherit its risk by sharing a dict.
_LBL_SIDE_SD = _SF.text_paths("SD", 3.90, 0.50, 1.50)
_d_sd, _who_sd, _ = _SF.min_gap(_LBL_SIDE_SD, 0.50)
assert _d_sd >= 2 * 0.40, (
    f"experimental SD pinches to {_d_sd:.3f}mm of MATERIAL, under two extrusions. The stroke is "
    f"the authorised experiment; the web is not -- if the web fails too there is nothing to "
    f"learn from the print. Worst pair: {_who_sd}")

for _k in _LBL:
    _label_ok(_LBL[_k], _k)

_SD_W,  _SD_H  = _SF.ink_size("SD",  LABEL_H_FLAT, LABEL_W, LABEL_GAP)
_MIC_W, _MIC_H = _SF.ink_size("MIC", LABEL_H_FLAT, LABEL_W, LABEL_GAP)
_VOL_W, _VOL_H = _SF.ink_size("VOL", LABEL_H_CAP,  LABEL_W, LABEL_GAP)

# SD: centred in the free margin strip between the board edge and the hex field, and centred
# on the SLIT so the two read as one thing. Rotated, so its INK HEIGHT is what spends the
# strip's width.
LBL_SD_X = HEX_FIELD_X0 / 2.0
LBL_SD_Y = (SD_SOCKET[2] + SD_SOCKET[3]) / 2.0
assert LBL_SD_X - _SD_H / 2 >= LABEL_MARGIN and LBL_SD_X + _SD_H / 2 <= HEX_FIELD_X0 - LABEL_MARGIN, (
    f"the SD label is {_SD_H:.2f}mm across and the margin strip is only {HEX_FIELD_X0}mm "
    f"wide; it would foul the board edge or the hex field. Shrink LABEL_H_FLAT.")
assert (LBL_SD_Y - _SD_W / 2 >= SD_SOCKET[2] - 2.0
        and LBL_SD_Y + _SD_W / 2 <= SD_SOCKET[3] + 2.0), (
    "the SD label has drifted off the slit it names")

# MIC: butted up to the mic hole's keepout on the side away from the corner boss, and centred
# on the hole's own Y so the label sits beside it rather than under it.
LBL_MIC_X = MIC[0] - MIC_HOLE_D / 2 - LABEL_MARGIN - _MIC_W / 2
LBL_MIC_Y = MIC[1]
assert LBL_MIC_Y - _MIC_H / 2 >= HEX_FIELD_Y1 + LABEL_MARGIN, (
    f"the MIC label reaches y={LBL_MIC_Y - _MIC_H/2:.2f} and the hex field ends at "
    f"{HEX_FIELD_Y1} — it would cut into the vent cells.")
assert LBL_MIC_X - _MIC_W / 2 >= HOLES[2][0] + CBORE_D / 2 + LABEL_MARGIN, (
    "the MIC label runs into the upper-left screw counterbore")
assert LBL_MIC_X + _MIC_W / 2 <= MIC[0] - MIC_HOLE_D / 2 - LABEL_MARGIN + 1e-9, (
    "the MIC label runs into the mic hole")

# ============================================================================
# CONNECTOR LABELS -- issue #27.  UART / I2C / SPK / BAT / IO.
# ============================================================================
#
# >>> THE MAPPING IS THE ENTIRE RISK IN THIS FEATURE, AND IT IS NOT DERIVABLE. <<<
#
# `CONN_R` and `CONN_L` are ANONYMOUS Y-SPANS lifted out of the vendor STEP. Nothing in this
# file knows which of them is the battery and which is the UART, and a label is a coordinate
# whose entire job is to point at something else — so getting it wrong produces exactly the
# fault the opening/component ledger at check 0d exists for, except permanent, in plastic, and
# on the port a person is about to plug a LiPo into. The block at BTN_TIP_Z is the precedent:
# BOOT and RESET were swapped by re-deriving an assignment from a drawing IN GOOD FAITH.
#
# So the names come from the vendor silkscreen (Figure 5-1, ES3C28P outline drawing), and the
# ORDER along each edge is pinned by that drawing's own dimension chains — which are asserted
# below against this file's `CONN_*`, because a chain that closes is evidence and a chain
# nobody checked is a chain someone read backwards.
#
#   silkscreen, X=0 edge (2 connectors)   BAT (2-pin, "- +")   UART (4-pin, RXD TXD GND 5V)
#   silkscreen, X=50 edge (3 connectors)  SPEAKER (2-pin)      I2C (3.3V GND SCL SDA)   IO
#
# ⚠️ WHICH EDGE IS WHICH IS **NOT** TAKEN FROM THE DRAWING. That is the handedness question the
# drawing cannot answer (see BTN_TIP_Z). It is taken from the five-way STEP solid fit that also
# fixed CONN_R/CONN_L, corroborated here by the microSD: the chain puts the socket centre at
# BL-35.03 and `SD_SOCKET` independently centres 0.06mm away, on the low-x edge. The drawing is
# used only for the ORDER ALONG an edge, and Y is not the disputed axis.
_DRAW_CHAIN_R = (13.55, 17.85, 18.25)   # CONN_R[0] -> [1] -> [2] -> board end
_DRAW_CHAIN_L = (11.82, 15.97, 35.03)   # CONN_L[0] -> [1] -> microSD centre -> board end
CONN_LBL_R = ("SPK", "I2C", "IO")       # X=50 edge, in increasing Y
CONN_LBL_L = ("BAT", "UART")            # X=0  edge, in increasing Y
# ---- and the tie back to the spans, so a suppressed opening suppresses its label ----
#
# >>> NO LABEL MAY NAME AN OPENING THAT IS NOT THERE. <<<
#
# This is check 0d's rule applied to ink instead of plastic, and it is the sharper half: an
# opening with nothing behind it is invisible until someone looks; a LABEL beside solid plastic
# actively sends a person hunting for a port that does not exist. The desk's BAT and the
# mobile's BAT and SPK are dropped rather than re-captioned — a moulded-in name is wayfinding
# for a port you can USE, and the connector's position is already documented in the vendor
# drawing and in this file. Positions of the SURVIVING labels are packed against the NOMINAL
# span set, so nothing shifts sideways just because a neighbour closed.
CONN_LBL_KEY = {**{_n: ("R", _i) for _i, _n in enumerate(CONN_LBL_R)},
                **{_n: ("L", _i) for _i, _n in enumerate(CONN_LBL_L)}}


def _chain_centres(chain):
    """Feature centres implied by a drawing dimension chain that closes on the board end."""
    out, y = [], float(BL)
    for d in reversed(chain):
        y -= d
        out.append(y)
    return list(reversed(out))


# ⚠️ AND THE CONTROL IS THE REVERSED READING, because that is the mistake available here. A
# chain is a list of gaps; reading it from the wrong end is a mirror in Y and produces a
# perfectly self-consistent set of centres that lands on the wrong connectors. It has to MISS.
for _chain, _spans, _what in ((_DRAW_CHAIN_R, CONN_R, "CONN_R"), (_DRAW_CHAIN_L, CONN_L, "CONN_L")):
    _want = [(a + b) / 2 for (a, b) in _spans]
    _got = _chain_centres(_chain)[:len(_want)]
    assert all(abs(g - w) <= 0.05 for g, w in zip(_got, _want)), (
        f"the vendor drawing's {_what} chain {_chain} implies centres "
        f"{[round(g,2) for g in _got]} but the STEP gives {[round(w,2) for w in _want]} — the "
        f"chain no longer closes, so the silkscreen ORDER it establishes is unsupported and "
        f"the labels below may be naming the wrong ports. Do not adjust the tolerance")
    _rev = [sum(_chain[:i + 1]) for i in range(len(_want))]
    assert not all(abs(r - w) <= 0.05 for r, w in zip(_rev, _want)), (
        f"[self-test] reading the {_what} chain from the OTHER end also closes, so the chain "
        f"cannot tell which way round the edge runs and it is not evidence of the order")
assert abs(_chain_centres(_DRAW_CHAIN_L)[2] - (SD_SOCKET[2] + SD_SOCKET[3]) / 2) <= 0.10, (
    "the drawing's chain and SD_SOCKET disagree about the microSD centre — that closure is "
    "what ties the drawing's bottom edge to this file's LOW-X edge, and without it the "
    "BAT/UART pair could belong to either long edge")

# ---- placement ----
# One strip per edge, mirroring the SD rule (centred between the board edge and the hex field),
# and one label per connector, ROTATED so the ink HEIGHT is what spends the strip's width.
LBL_CONN_X_L = HEX_FIELD_X0 / 2.0                 # 4.50, the same strip SD uses
LBL_CONN_X_R = (HEX_FIELD_X1 + BW) / 2.0          # 45.50
# The Y window is set by the corner counterbores, which sit dead centre of BOTH strips.
_LBL_Y_LO = HOLES[0][1] + CBORE_D / 2 + LABEL_MARGIN          #  7.70
_LBL_Y_HI = HOLES[2][1] - CBORE_D / 2 - LABEL_MARGIN          # 78.30


def _pack_labels(items, y_lo, y_hi, what):
    """Centres for a column of labels: on their own feature where possible, else separated.

    ⚠️ CENTRING EACH LABEL ON ITS OWN CONNECTOR DOES NOT FIT AND CANNOT BE MADE TO. BAT and
    UART are 11.78mm apart and their ink is 13.28 and 18.04 long, so the two would overlap by
    3.9mm; shrinking to fit needs h <= 2.93, which is far under the stroke floor. So the rule
    is: nominal = the connector's own centre, then push apart to LABEL_MARGIN in increasing Y,
    then slide the whole column down if it has run out the top. ORDER IS PRESERVED BY
    CONSTRUCTION, which is the property that keeps each label next to its own port.
    """
    c = [n for (_, n, _) in items]
    ln = [l for (_, _, l) in items]
    for i in range(1, len(c)):
        c[i] = max(c[i], c[i - 1] + (ln[i - 1] + ln[i]) / 2 + LABEL_WORD_GAP)
    _over = (c[-1] + ln[-1] / 2) - y_hi
    if _over > 0:
        c = [v - _over for v in c]
    assert c[0] - ln[0] / 2 >= y_lo - 1e-9, (
        f"the {what} label column needs "
        f"{sum(ln) + LABEL_WORD_GAP*(len(ln)-1):.2f}mm and the strip has "
        f"{y_hi - y_lo:.2f}mm between the corner counterbores. Shorten a label or LABEL_H_FLAT")
    return c


_FACE_OPENING = {"SPK": SPK_RELIEF_Y}   # ports whose relief pierces the back face
_CH_HI, _CH_LO = side_channels()                  # x=BW edge, x=0 edge
_conn_place = {}                                  # name -> (x, y, own channel span)
for _names, _spans, _x, _yhi, _what in (
        # ⚠️ the LEFT column stops at the SD label, not at the counterbore: SD is already on
        # this strip and is not moving for us. The right strip is empty, so it gets the lot.
        (CONN_LBL_L, _CH_LO, LBL_CONN_X_L, LBL_SD_Y - _SD_W / 2 - LABEL_WORD_GAP, "x=0"),
        (CONN_LBL_R, _CH_HI, LBL_CONN_X_R, _LBL_Y_HI, "x=%g" % BW)):
    # ⚠️ A PORT WITH A HOLE IN THE FACE CANNOT HAVE ITS LABEL ON TOP OF IT (#33). SPK's relief
    # is a through-opening across y 31.79..40.94, which is exactly where SPK's ink wanted to
    # be, so its nominal moves to just clear of the opening instead of onto its port. That is
    # not a downgrade in association: a label beside a visible hole points harder than a label
    # over an invisible connector. The `nearest label wins` ledger below is what checks it.
    _items = []
    for _i, _n in enumerate(_names):
        _len = _SF.ink_size(_n, LABEL_H_FLAT, LABEL_W, LABEL_GAP)[0]
        _nom = (_spans[_i][0] + _spans[_i][1]) / 2
        if _n in _FACE_OPENING:
            _nom = min(_nom, _FACE_OPENING[_n][0] - LABEL_WORD_GAP - _len / 2)
        _items.append((_n, _nom, _len))
    for _n, _cy in zip(_names, _pack_labels(_items, _LBL_Y_LO, _yhi, _what)):
        _conn_place[_n] = (_x, _cy, _spans[list(_names).index(_n)])

# ---- and the ledger: every label must name the connector it sits on ----
#
# This is check 0d's question asked of labels instead of openings, and it is the one thing
# here a render cannot answer: a label 6mm off its port looks perfectly deliberate.
for _n, (_x, _cy, _own) in _conn_place.items():
    _w, _h = _SF.ink_size(_n, LABEL_H_FLAT, LABEL_W, LABEL_GAP)
    # THE ASSOCIATION RULE IS "THE INK SPANS THE PORT'S CENTRELINE", not "the label's centre
    # sits in the channel", and the weaker-looking rule is the better one for two reasons.
    # It is what a reader actually does — look across from the port into the strip and read
    # whatever is level with it — and the stricter rule is unsatisfiable here: BAT and UART
    # are 11.78mm apart carrying 13.28 and 18.04mm of ink, so pinning both centres inside
    # their channels leaves 16.88mm for a 15.66mm + word-space column. The strict rule would
    # have forced the word space back down to 1.22mm, i.e. back to labels that merge.
    _port = (_own[0] + _own[1]) / 2
    # >>> THE RULE IS "EVERY PORT'S NEAREST LABEL IS ITS OWN". <<<
    #
    # It was "the ink spans the port's centreline", which is the stronger and nicer property
    # and four of the five still satisfy it exactly. SPK cannot: #33 put a through-opening
    # over its port, so no ink can be level with it. Weakening to nearest-wins is not giving
    # up — it is the property that was actually meant. "This label names that port" IS a
    # nearest-neighbour claim, and stating it that way covers the case where the port's own
    # relief is the thing the label points at.
    _dist = lambda cy, w: max(0.0, abs(_port - cy) - w / 2)
    _mine = _dist(_cy, _w)
    for _o, (_ox, _ocy, _) in _conn_place.items():
        if _o == _n or (_ox < BW / 2) != (_x < BW / 2):
            continue
        _ow = _SF.ink_size(_o, LABEL_H_FLAT, LABEL_W, LABEL_GAP)[0]
        assert _dist(_ocy, _ow) > _mine, (
            f"the {_o} label is nearer to {_n}'s port at y={_port:.2f} "
            f"({_dist(_ocy, _ow):.2f}mm) than {_n}'s own is ({_mine:.2f}mm) — the two labels "
            f"have swapped ports, or one has been packed past the other")
    assert _mine <= LABEL_WORD_GAP + (_own[1] - _own[0]) / 2, (
        f"the {_n} label's ink is {_mine:.2f}mm from its port at y={_port:.2f} — near enough "
        f"to win the nearest-label test only because nothing else is close, which is not the "
        f"same as labelling it")
    _s0, _s1 = (0.0, float(HEX_FIELD_X0)) if _x < BW / 2 else (float(HEX_FIELD_X1), float(BW))
    assert _s0 + LABEL_MARGIN <= _x - _h / 2 and _x + _h / 2 <= _s1 - LABEL_MARGIN, (
        f"the {_n} label is {_h:.2f}mm across and its margin strip is x {_s0:g}..{_s1:g} — it "
        f"would foul the board edge or the hex field. Shrink LABEL_H_FLAT")
    for _o, (_ox, _ocy, _oown) in _conn_place.items():
        if _o == _n or (_ox < BW / 2) != (_x < BW / 2):
            continue                              # different edge: no possible confusion
        assert _cy + _w / 2 < _oown[0] or _cy - _w / 2 > _oown[1], (
            f"the {_n} label's ink reaches into {_o}'s channel ({_oown[0]:.2f}..{_oown[1]:.2f}) "
            f"— two ports and one label between them is worse than no label")
        _ow = _SF.ink_size(_o, LABEL_H_FLAT, LABEL_W, LABEL_GAP)[0]
        assert abs(_cy - _ocy) >= (_w + _ow) / 2 + LABEL_WORD_GAP - 1e-9, (
            f"the {_n} and {_o} labels are {abs(_cy-_ocy)-(_w+_ow)/2:.2f}mm apart, under the "
            f"{LABEL_WORD_GAP}mm word space — at {LABEL_GAP - LABEL_W}mm they read as ONE WORD, "
            f"which is what `SPKI2C` and `BATUARTSD` were")
# and nothing may collide with the label that was already on the left strip
# ⚠️ A WORD SPACE, NOT A KEEPOUT. SD is the third label on this strip and it merges with UART
# exactly as UART merged with BAT — the first cut read `BATUARTSD` as one string. LABEL_MARGIN
# would satisfy a clearance check and still print an unreadable column.
_uart_top = _conn_place["UART"][1] + _SF.ink_size("UART", LABEL_H_FLAT, LABEL_W, LABEL_GAP)[0] / 2
assert _uart_top <= LBL_SD_Y - _SD_W / 2 - LABEL_WORD_GAP + 1e-9, (
    f"the UART label ends at y={_uart_top:.2f} and the SD label's ink starts at "
    f"{LBL_SD_Y - _SD_W/2:.2f} — under a {LABEL_WORD_GAP}mm word space they read as one word")
# ⚠️ STATED RATHER THAN ASSERTED, because it is true and unavoidable: UART's ink DOES overlap
# the microSD channel's Y span by ~1.8mm. The microSD is not one of the five ports being
# labelled, it already carries its own label 0.8mm further on, and the alternative is a UART
# label that no longer covers the UART. The foreign-channel assert above is therefore scoped
# to the CONNECTORS, which is the confusion that actually matters.

# CAP LABELS. The remaining cap thickness is the thing to watch, and it was worth a number
# rather than a shrug. Since r11 the cap face is FLAT (the r10 bench killed the face recess)
# and the label alone spends DEBOSS_* + LABEL_DEBOSS: the big cap keeps 1.40mm under its VOL
# ink and full 2.60 everywhere else — strictly stiffer than the r10 plate whose 1.22 already
# bowed only 0.033mm under a 2N press (~8% of the 0.25mm switch travel). The assert below is
# unchanged because the label FLOOR never moved; only the face around it rose.
for _cx in BTN:
    _cy, _R, _deb = cap_geometry(_cx[0])
    _big = (_cx[0] == BTN_BOOT_X)
    _rem = WALL - _deb - LABEL_DEBOSS
    assert _rem >= 1.20, (
        f"a label on the cap at x={_cx[0]} leaves {_rem:.2f}mm of cap. Too floppy to drive "
        f"the pip; either shallow the label or shallow the cap deboss.")
    if _big:
        _slack = _hex_holds(_VOL_W, _VOL_H, _R - CAP_INSET, LABEL_MARGIN, "VOL on the big cap")
    else:
        _pw = 2 * (PWR_R + LABEL_W / 2)
        _slack = _hex_holds_circle(_pw, _R - CAP_INSET, LABEL_MARGIN,
                                   "power symbol on the small cap")

# ---- USB-C PORT, CONFORMING (r11) ----
#
# JP, 2026-08-02: "can we make the bottom usb c opening conform a little better the the
# acutaly usb c plug?" A USB-C shell is a STADIUM — full-radius ends on an 8.94 x 3.25 body
# (USB_X/USB_Z, measured off the vendor STEP) — and the uniform offset of a stadium is a
# stadium, so both cuts now derive from the receptacle's own numbers plus one clearance.
# The old cuts were rectangles typed in whole-mm slop (14 x 6 bore, 19 x 8.6 relief): the
# port read as a letterbox and told the plug nothing about where centre was.
USBC_CLR = 0.80                           # bore clearance around the RECEPTACLE shell. The
                                          # PLUG shell is smaller still (8.34 x 2.56 nominal),
                                          # so the plug itself sees ~1.1/side: a snug guide
                                          # that still accepts a blind stab in the dark.
USBC_CX  = (USB_X[0] + USB_X[1]) / 2      # 25.000 — the receptacle's own axis, never retyped
USBC_CZ  = (USB_Z[0] + USB_Z[1]) / 2      # -3.225
USBC_W   = (USB_X[1] - USB_X[0]) + 2*USBC_CLR    # 10.54
USBC_H   = (USB_Z[1] - USB_Z[0]) + 2*USBC_CLR    #  4.85; end radius H/2 makes a true stadium
# The outside relief seats the moulded body, not the shell. TAIL_W's survey: no moulded
# USB-C body is over 14mm across; heights run to ~6.5. ⚠️ 15.0 x 7.0 IS SIZED TO THAT
# SURVEY, not measured off one cable — the same standing as CABLE_OD, and the same risk.
USBC_OM_W, USBC_OM_H, USBC_OM_R = 15.0, 7.0, 2.5
USBC_OM_DEPTH = 1.6                       # unchanged from the r10 relief
assert USBC_OM_W >= USBC_W + 2*1.0 and USBC_OM_H >= USBC_H + 2*1.0, (
    f"the overmould pocket ({USBC_OM_W} x {USBC_OM_H}) must contain the bore ({USBC_W:.2f} x "
    f"{USBC_H:.2f}) with a >=1.0 ledge all round -- the ledge is what the moulded body seats on")
assert 18.0 <= USBC_CX - USBC_W/2 and USBC_CX + USBC_W/2 <= 32.0 \
   and -6.60 <= USBC_CZ - USBC_H/2 and USBC_CZ + USBC_H/2 <= -0.60, (
    "the conforming bore has left the r10 bore's window (x 18..32, z -6.60..-0.60). That "
    "window is air the bench has already seen; outside it, prove the wall is clear first")
assert -8.20 <= USBC_CZ - USBC_OM_H/2 and USBC_CZ + USBC_OM_H/2 <= 0.40 \
   and 15.5 <= USBC_CX - USBC_OM_W/2 and USBC_CX + USBC_OM_W/2 <= 34.5, (
    "the conforming relief has left the r10 relief's window (x 15.5..34.5, z -8.20..0.40) "
    "-- same rule as the bore: only cut where the old cut proved there was nothing to hit")

# ---- BRAILLE (r11), for fun ----
#
# JP, holding the printed r10: "the deep deboss of the button lables is a good tactile hint
# but you should add brail too for fun." One Grade-1 cell per button, the letter the INK
# already uses (V for VOL, P for PWR — braille agrees with the print, not the schematic),
# recessed into the bottom edge flanking the USB-C well.
#
# WHY THE BOTTOM EDGE — the obvious homes were measured and none holds a cell:
#   * on a cap: VOL's ink is 10.63 wide; in a flat-top hex only 13.27 tall through centre,
#     text + a 6.5-tall cell overruns the slant inset at every offset. The small cap is
#     worse (R 5.77 barely holds the cell ALONE).
#   * left face strip: 4.55mm free between the (4,4) boss and BAT's ink; a cell needs 6.5.
#   * right face strip: fits ONE cell in the boss..SPK gap, not two — and splitting the
#     pair breaks the property that actually matters (next paragraph).
# The bottom edge has ~12mm clear each side of the port and nothing else on it.
#
# THE MAPPING IS ADJACENCY, NOT CHIRALITY: V sits on the big cap's side of the port (cell
# centre 14.65 vs island 16.66), P on the small cap's (35.35 vs 35.66) — nearest-cell-wins,
# the same rule the port labels use. A mirror mistake can misdraw a letter; it can never
# point a letter at the wrong button.
#
# RECESSED, NOT RAISED, deliberately: real braille is embossed, but raised dots here would
# grow the 91.90 Y envelope and ride the stand's slot floor; recesses cost neither and a
# vertical wall prints them crisply (the flank labels' class). Standard cell metrics
# otherwise: 2.5mm dot pitch, O-1.6 dots, 0.8 deep (leaves WALL - 0.8 = 1.80 of wall).
#
# ⚠️ READING FRAME IS PROVISIONAL UNTIL PLASTIC — the flank labels earned that rule tonight.
# Authored to read with the BACK FACE UP and the bottom edge toward the reader (the pose in
# which the caps are pressed and their labels read): reading-right = model -X, reading-up =
# model -Z. If the bench reads the letters mirrored, flip BRL_CHIR alone and nothing else.
BRL_PITCH, BRL_DOT_D, BRL_DEPTH = 2.5, 1.6, 0.8
BRL_CHIR = -1.0                # reading-right, in model X. BENCH-PENDING (r11 will answer)
BRL_GAP  = 0.80                # cell ink to pocket edge; LABEL_MARGIN's value, same job
_BRL = {"V": ((0,0),(0,1),(0,2),(1,2)),      # dots 1,2,3,6   (col, row), row 0 = cell top
        "P": ((0,0),(0,1),(0,2),(1,0))}      # dots 1,2,3,4
_BRL_EXT = (BRL_PITCH + BRL_DOT_D) / 2                    # cell centre -> ink edge, 2.05
BRL_CX_V = USBC_CX - USBC_OM_W/2 - BRL_GAP - _BRL_EXT     # 14.65
BRL_CX_P = USBC_CX + USBC_OM_W/2 + BRL_GAP + _BRL_EXT     # 35.35
assert abs(BRL_CX_V - CAP_CX_BOOT) < abs(BRL_CX_V - CAP_CX_RESET) \
   and abs(BRL_CX_P - CAP_CX_RESET) < abs(BRL_CX_P - CAP_CX_BOOT), (
    "a braille cell is nearer the OTHER button's island -- adjacency is the whole mapping; "
    "move the cells, not the letters")
assert WALL - BRL_DEPTH >= 1.60, (
    f"braille dots leave {WALL - BRL_DEPTH:.2f}mm of bottom wall, under the 1.60 solid floor")
_brl_z_lo = USBC_CZ - BRL_PITCH - BRL_DOT_D/2             # -6.525, lowest ink
_brl_z_hi = USBC_CZ + BRL_PITCH + BRL_DOT_D/2             # +0.075, highest ink
assert _brl_z_lo >= BACK_Z + 2.0 and _brl_z_hi <= 0.40, (
    "braille ink has left the bottom wall band this design has proof of: below, the back-"
    "face chamfer (0.80 at BACK_Z, defined later in this file) plus margin; above, the r10 "
    "relief's top edge (0.40) -- wall beyond either has never been shown to exist")
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
