jphein/ember.realm.watch/esphome/tools/check_navigability.py

#!/usr/bin/env python3
"""Button-only navigability walk: every ui_mode reachable AND exitable without touch.

WHY THIS EXISTS (#23)

Three bugs in one day were the same KIND of bug, and no existing check could see any of
them, because each is a question about whether a PATH EXISTS. `esphome compile` and
`check_tiling` only confirm that the code ON a path is well-formed:

  * the mode-submenu cursor advanced `% 4` in a 3-row menu — a cursor state that lands
    on a row that is never drawn (#4);
  * the mode submenu had no `ui_mode == 3` long-press branch, so it was enterable from
    the BOOT button and NOT LEAVABLE from it (#4);
  * and the enclosure equivalents: a stand in front of the screen, buttons sealed inside
    it — present, and unreachable.

The second is the dangerous shape and it is specifically dangerous here. GPIO0/BOOT is
the ENTIRE hardware input budget (K1/RESET is hardwired to CHIP_PU and cannot be read),
so these menus exist ON the button precisely because recovering the device must not
require the touchscreen — `btn_rouse_touch` is a row in the power menu for exactly that
reason. A mode you cannot leave without a working touch controller defeats the menu's
whole purpose, and it was introduced within an hour of the submenu being added, by
reusing a mechanism that looked like it transferred. **A reused mechanism does not carry
its guarantees with it.**

HOW IT AVOIDS BEING A COPY OF THE FIRMWARE

The obvious way to write this is to hand-transcribe the two button lambdas into a
simulator. That inherits exactly the drift problem it is meant to catch — this repo has
a figure that hand-wrote a button outline as a rectangle and went on drawing squares
after the part became hexagonal, and a twelve-row truth table that verified *a
transcription of* the watchdog rather than the watchdog.

So this script EXTRACTS the action lists from `ember-satellite.yaml` and TRANSLATES them
into C++ mechanically, then compiles and runs them. The lambda bodies are emitted
verbatim. If the firmware's lambdas change, this walk changes with them; if they stop
compiling, this fails.

⚠️ THE TRANSLATION PRESERVES THE ONE SEMANTIC THAT MATTERS MOST. Each `- lambda:` action
becomes an immediately-invoked `[&]{ ... }();`, because **a `return` in an ESPHome lambda
ends that lambda and does NOT abort its sibling actions in the enclosing action list.**
That is not a detail — it is the bug in #15 and the bug oracle-verifier found on the
`va_state == 1` guard. A translation that let `return` escape the whole handler would be
a *different state machine* that happened to look right.

WHAT IT ASSERTS
  1. every ui_mode (0 normal, 1 volume, 2 power, 3 modes) is REACHABLE from (0, -1) by
     GPIO0 short/long presses only — no touch events at all;
  2. every reachable state can get BACK to ui_mode == 0 the same way, without rebooting;
  3. the cursor visits exactly the rows that are DRAWN — every drawn row reachable, and
     no row beyond the drawn count ever selected (this is the `% 4` bug);
  4. the three places that independently encode each menu's row count agree: the paint
     loop bound, the cursor modulus, and the touch hit-test bound;
  5. every drawn row is ACTIONABLE from the button — a long press on it must not do
     merely what a long press with nothing selected does.
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
